JCastel358/Eltec406mca/hardware/single_detector_usb_master_r1/research/adc_seller_image_05.jpg

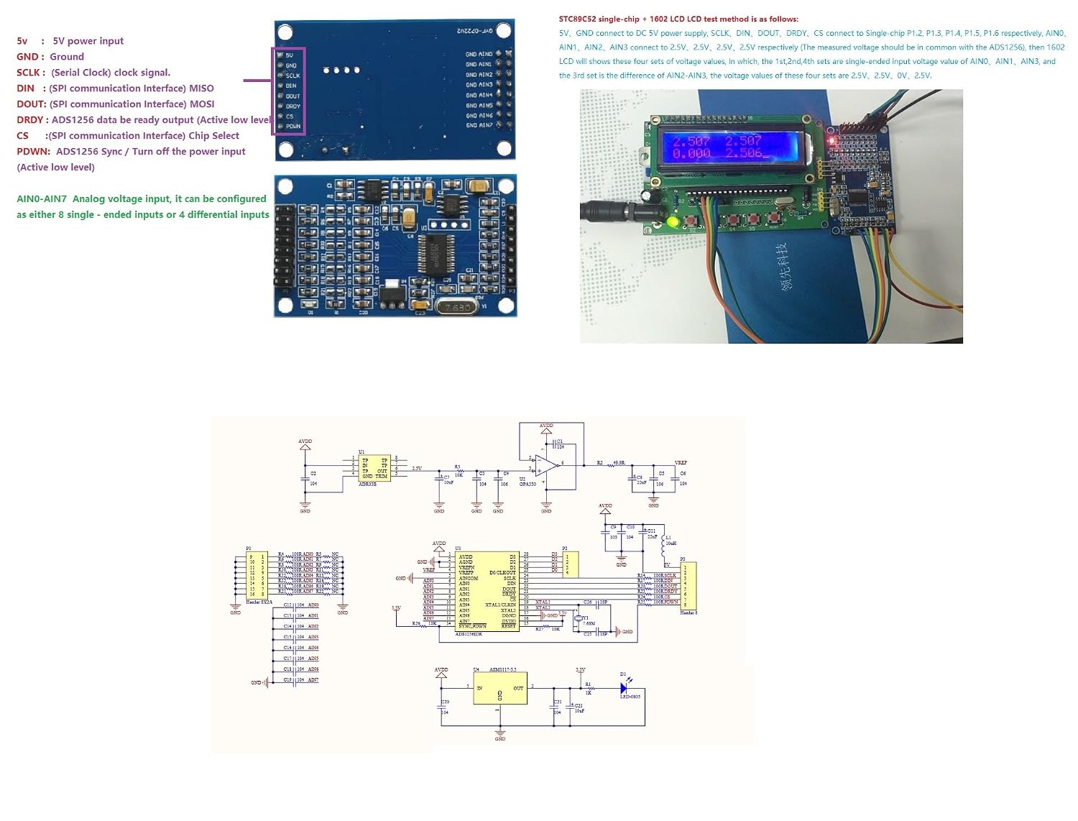
hardware/single_detector_usb_master_r1/research/adc_seller_image_05.jpg
