JCastel358/Eltec406mca/hardware/single_detector_usb_master_r1/reports/copper_review_complete/review.md

# Completed-board copper verification

**Final bounded verification is complete; no additional native repair is requested.** Audited main PCB SHA-256: `2ab4937f2ec558227736722549489c8d60b382db2a86436887f104acd336f4e2`. It matches `reports/final_ground_integration/integration.json`. The native integration report and its hash verify **0 DRC violations, 0 unconnected items and 0 schematic parity issues**. Protected-Kelvin verification passes independently on the audited snapshot.

The actual filled-reference audit was rerun into this new directory; all historical reports remain intact. The 562 selected SPI/control and analog tracks across 58 nets produce the same reference-coverage results as the preceding signal-route review: no sampled EM_GND crossing or antenna intrusion; 179 local reference-void runs, with a maximum individual span of 1.496 mm. The preceding detailed check identified their midpoints as through-pad/via clearance openings. The local clock/MOSI geometry and limits documented in `reports/copper_review_final/review.md` remain applicable because the final integration preserved every prior signal track and added only ground connections.

Actual nearest GND through-connection distances now confirm the intended improvement:

| Signal transition, mm | Before | Completed board | Actual GND stitch, mm |
| --- | --- | --- | --- |
| ADC_SCLK [55.8,91.25] | 7.994 mm | 1.005 mm | [55.9,92.25] |
| AMP_OUT5 [31.35,20.25] | 18.120 mm | 2.789 mm | [28.65,19.55] |
| AMP_OUT5 [32.5,22.5] | 18.863 mm | 2.003 mm | [32.6,24.5] |
| AMP_OUT5 [31.7,24.4] | 18.066 mm | 0.906 mm | [32.6,24.5] |

Each listed GND via connects the actual filled GND regions on both In1.Cu and In2.Cu. C11, C13, C39 and C36 retain their dedicated 1.2 mm local surface ground access. The separate C12/C16 ground improvements are present in the verified integration report. No CAD was modified by this audit, and the audit/helper tools are frozen after this evidence.

This confirms native geometry, sampled reference coverage and shorter physical inter-plane return access. It does not qualify RF performance, impedance, measured noise, mounted ESL, regulator stability or detector performance. Evidence is in `complete_validation.json`, `copper_review.json` and the hashed `source_snapshot.kicad_pcb`; the combined native DRC evidence remains under `reports/final_ground_integration`.
