JCastel358/Eltec406mca/hardware/single_detector_usb_master_r1/exports/board_review/final_candidate/visual_review.md

# Final board PDF visual review

The primary design agent viewed all seven individually rendered pages on
2026-09-09, after export from board SHA-256
`2ab4937f2ec558227736722549489c8d60b382db2a86436887f104acd336f4e2`.
The accompanying JSON binds this review to the exact PDFs and rendered pages.

| File / page | Inspected result |
|---|---|
| assembly_top.pdf / 1 | Outline, module envelopes, centered references, polarity/pin markers and CUSTOMER annotations visible. Antenna keepout text is inside its empty region. Drawing and right-side module labels clear the page frame and title block. |
| copper_top.pdf / 1 | Complete top copper and legend shown; C12 and C16 return stubs visible. Board drawing clears the title block. Dense copper/legend overlay is intentional; use assembly drawing for part identification. |
| copper_bottom.pdf / 1 | Complete bottom view, explicitly labeled mirrored. Outline and copper contained within margins; title clear. |
| copper_layers.pdf / 1 | Complete F.Cu drawing, viewed from top, with no legend overlay. |
| copper_layers.pdf / 2 | Complete In1.Cu fill; ground-domain separations and antenna void visible; outline and title clear. |
| copper_layers.pdf / 3 | Complete In2.Cu fill; ground-domain separations and antenna void visible; outline and title clear. |
| copper_layers.pdf / 4 | Complete B.Cu drawing viewed from top, consistent with the separately mirrored bottom review. |

No unresolved page clipping, title overlap, missing drawing region or misplaced
module label was found. The earlier automatic-fit copper drawings touched the
title block; these final exports use explicit 2:1 scaling on A3 portrait pages
and resolve that issue. Small pin/reference details require normal PDF zoom.

This review checks the appearance of the PDFs. Native DRC/connectivity, copper
reference analysis, fabrication coordinates and physical qualification are
separate evidence. DNP crosses on the two jacks are deliberate. Module envelopes
are placement references, not fabricated module bodies or confirmed fit.
