JCastel358/Eltec406mca/hardware/single_detector_usb_master_r1/exports/fabrication_draft/20260909T153915_341509Z_690d80156d71_DRAFT/evidence/native_drill_report_DRAFT.txt

Drill report for single_detector_usb_master.kicad_pcb
Created on 2026-09-09T11:39:25

Copper Layer Stackup:
    =============================================================
    L1 :  F.Cu                      front
    L2 :  In1.Cu                    in1
    L3 :  In2.Cu                    in2
    L4 :  B.Cu                      back

Drill file 'single_detector_usb_master-PTH.drl' contains
    plated through holes:
    =============================================================
    T1  0.300mm  0.0118"  (214 holes))
    T2  0.800mm  0.0315"  (3 holes))
    T3  1.000mm  0.0394"  (18 holes)  (with 6 slots)
    T4  1.020mm  0.0402"  (54 holes))
    T5  1.200mm  0.0472"  (6 holes))

    Total plated holes count 295

Drill file 'single_detector_usb_master-NPTH.drl' contains
    unplated through holes:
    =============================================================

    Total unplated holes count 0
