JCastel358/Eltec406mca/docs/DATA_MAP.md

# Data map — where results, captures and calibration files live

**Nothing the apps record is stored inside this repository.** Every batch CSV,
attempt log, waveform snapshot, raw noise capture and reference-calibration
file is written to a per-model folder under the signed-in user's `Documents`.
This file maps those folders, the naming conventions, the in-repo evidence
that backs the production constants, and the backup routine.

Reconciled with the Windows bench laptop on **2026-09-02**.

---

## 1. Results roots (one per sensor model)

| Model | Root (Windows `%USERPROFILE%\Documents\…`, Xubuntu `~/Documents/…`) | Set in |
| --- | --- | --- |
| 405 M22 | `Eltec_405M22_Test_Results\405m22_esp32\` | `sensor_versions.py` / `m405m22` tester |
| 406 MCA | `Eltec_406MCA_Test_Results\v6_1_esp32\` (the folder name is the historical v6.1 build id — it is the correct, live location) | `m406mca` tester |
| 449 M18 | `Eltec_449M18_Test_Results\449m18_esp32\` | `m449m18` tester |
| 40623 array (DAQ rig) | `Eltec_40623_Test_Results\40623_array_daq\` | `array_rig/m40623` tester (`ELTEC_ARRAY_RESULTS_ROOT` overrides it for engineering runs) |

The apps create these on first save. A batch started on Windows is readable on
Xubuntu and vice versa (same CSV format, same layout). Re-entering an existing
batch number resumes it at the next sensor.

On the single-detector rigs a sensor number is only spent by a **PASS**
(2026-09-02), so a batch CSV holds **one row per test**: `500-7` appears once
for each part tried under that number, the last of them the pass that earns
it. `number_attempt` says which of those a row is.

### Inside each root

```
<root>\
├── <prefix>_lot_<lot>.csv              one verdict row per TEST (the production record); a number
│                                       that has not been passed yet repeats until a part earns it
├── <prefix>_lot_<lot>_attempts.csv     one row per event: measured / measure_error / stopped /
│                                       saved / stream_retry / rig_note  (attempt history; since
│                                       2026-09-09 a reference-unit lockout is a measure_error row)
├── autosave\                           in-progress batch state (crash recovery)
├── waveform_snapshots\lot_<lot>\       PNG per "Capture waveform" (+ cycle CSV sidecars);
│                                       automatic for failing noise captures / unstable drives
├── noise_captures\lot_<lot>\           405 M22 only: <sensor>_noise_raw.csv + .npz — the RAW
│                                       1000 SPS emitter-off record (opt-in button, and automatic
│                                       whenever any window goes over the limit)
├── calibration\*_cycles.csv            stability_calibration.py evidence captures (engineering)
└── reference_sensor_calibration.json   AIN1 reference baseline (the gate is ON again on every
                                        model since 2026-09-09; files predating the isolated
                                        buffer board are refused on load and kept as evidence)
```

`<prefix>` is `405m22_esp32`, `406mca_esp32` or `449m18_esp32`. The 449 M18
snapshots carry `_5hz` / `_18hz` suffixes.

### Inside the array rig's root (one tray = up to fifty parts)

```
Eltec_40623_Test_Results\40623_array_daq\
├── 40623_array_lot_<lot>.csv               one row per loaded POSITION per noise attempt; automatically saved
│                                           after capture; every row is
│                                           stamped calibration_status / calibration_id / verdict_status
├── 40623_array_lot_<lot>_attempts.csv      one row per TRAY event: offset_measured / locked / vacuum_confirmed / stabilisation_shortened /
│                                           capture_started / capture_retry / capture_error / noise_settled / judged / saved / remeasure
├── noise_captures\lot_<lot>\tray_<n>_raw.npz   the RAW 1000 SPS capture of all 50 channels (float32 [50, N],
│                                           ~4 MB compressed per 60 s tray) + 310-sample edge contexts, channel/
│                                           position/sensor-number arrays and metadata — the evidence for the
│                                           pending noise-limit derivation; never delete
└── grid_snapshots\lot_<lot>\tray_<n>.png       the coloured 5x10 grid (the TP120 data sheet equivalent)
```

Columns: `array_rig/m40623/README.md`. Sensor numbers are assigned when
**Measure noise** freezes the accepted offset readings, row-major over the
loaded positions, continuing the batch's highest number. Offset screening
reserves no numbers: each `offset_measured` event retains JSON with all fifty
readings, occupancy and classifications, including failures before replacement.
Since 2026-09-08 this also keeps initial/recheck voltages, occupancy source,
the inferred-empty cutoff/policy, actual recheck delay, and each position's
classification **if loaded**, so zero-output readings excluded as likely empty
remain reviewable. `locked` records the accepted map and manual overrides;
`vacuum_confirmed` records the operator's map/count and gauge confirmation.
`stabilisation_shortened` explains the deliberate departure from TP120's
five-minute power-on delay (the app cannot measure time since power-on).
`noise_settled` retains the successful capture's settling trace, including
unsettled deadline starts. Each one-second window records loaded-channel
maxima/minima and their deltas. The raw NPZ duplicates that trace in
`quiet_diagnostics_json`; CSV and NPZ record `noise_timing_policy`, the
criterion/tolerance, minimum/maximum wait, actual wait and stop reason.
A noise retry keeps its numbers (`tray_attempt` increments). The legacy
engineering lock API still records high-offset failure rows at lock time.

Simulation uses a separate root: the system temp directory's
`eltec-array-simulation`, or `<ELTEC_ARRAY_RESULTS_ROOT>/simulation` when
overridden. Rows carry `simulated=YES` and demo noise-limit provenance.

CSV columns are documented in each model README
([405](../single_detector_rig/m405m22/README.md),
[406](../single_detector_rig/m406mca/README.md),
[449](../single_detector_rig/m449m18/README.md)). Older batch files keep their
original header when columns are added later — rows stay aligned, new columns
are simply absent. A `NOT MEASURED` row (rig fault, nothing recorded) has empty
measurement columns and `failure_mode_tag = NM`; it is excluded from yield.

### Provenance suffixes seen on the bench laptop

Files were occasionally renamed by hand to keep history:
`_superseded_<date>_<reason>`, `_backup_all50_<date>`, `_hold_…`,
`_new15_only_backup`, `…_crosstalk_contaminated_<date>.json.bak`. Treat any
such file as **frozen evidence** — never delete or "clean up" without checking
[`CALIBRATION_RECORD.md`](CALIBRATION_RECORD.md) for what it backs. Prefer this
convention for future manual archiving: `<original name>_<YYYYMMDD>_<reason>`.

---

## 2. What is on the bench laptop today (2026-08-28)

| Folder | Size | Contents that matter |
| --- | --- | --- |
| `Eltec_405M22_Test_Results\405m22_esp32\` | ~15 MB, 75 files | **lot 500** (`405m22_esp32_lot_500.csv` + `_backup_all50_20260818` + `_superseded_20260817_reference_crosstalk`), test lots (`lot_test`, `lot_test2`, `lot_test_2`), `noise_captures\` (39 files, 9.7 MB — the raw captures behind the 15 % rule, the 60 s soak and the FIR change), `waveform_snapshots\` (18 files), `noise_experiments\` (2026-08-13 bench A/B: `part_in`, `part_out`, `covered`, `fan_off` `.npz` + `noise_experiment.py`), copies of the lot-500 Excel pair data, `reference_sensor_calibration_crosstalk_contaminated_20260817.json.bak` |
| `Eltec_406MCA_Test_Results\v6_1_esp32\` | ~16 KB | `406mca_esp32_lot_test.csv` + attempts, `reference_sensor_calibration.json` (historical schema-v2 baseline; refused on load since the 2026-09-09 schema v3 bump — kept as evidence, recalibrate instead) |
| `Eltec_449M18_Test_Results\449m18_esp32\` | ~5 KB | one attempts log — no production batch yet (calibration pending) |

Related folders outside this repository:

- `Documents\Eltec_IR_Telescope\` — the two-detector IR telescope: its own git
  repository (firmware v2.2 with `STREAM,START,BOTH`, app, session data).
  Unrelated to the sensor rig except that the same ESP32 board is reflashed
  between the two.
- `Documents\406_mca_data\` and `Documents\rename_to_Eltec_TestRig.cmd` —
  LabJack-era loose data and a leftover rename script. Candidates for archiving
  or deletion; not referenced by anything in this repository.

---

## 3. Evidence kept inside the repository

| Path | What it is | Backs |
| --- | --- | --- |
| `analysis/405M22_Data/405M22_Data_old_fixture.xlsx`, `405M22_Data_new_fixture.csv.xlsx` | lot-500 paired measurements, legacy fixture vs this rig (2026-08-17) | sensitivity factor **4.30**, noise allowance **15 %** |
| `analysis/reports/405M22_Noise_Filtering_Explained.md` (+ `.docx`, two PNGs) | explainer for the noise pipeline passband and the anti-alias FIR (2026-08-20) | noise verdict band, FIR change |
| `analysis/reports/LabJack_T7_406MCA_Buffer.docx`, `406MCA_Original_Buffer_Issue_Explanation_Readable.docx` | LabJack-era buffer write-ups | historical background for the op-amp buffer stage |
| `analysis/reports/406MCA_SNR_Analysis_Report.docx`, `406MCA_SNR_Group_Summary.csv` | outputs of the retired v1 SNR sweep analysis | historical |

The raw captures themselves (`.npz`) are **not** in git (they are ignored by
`.gitignore`) — see §5.

---

## 4. Tools that read this data

| Tool | Reads | Purpose |
| --- | --- | --- |
| `engineer_tools/noise_band/replot_noise_capture.py` | `noise_captures/**/*_noise_raw.npz|.csv` | Replays a saved raw capture through the exact production pipeline and through alternative bands / boxcars; prints a verdict-comparison table and a PNG per capture. This is why raw captures must never be lost — any future limit or band change can be re-judged on real parts. `--boxcar 20` reproduces the pre-2026-08-20 pipeline. |
| `engineer_tools/noise_band/filter_response_analysis.py` | (synthetic + a measured capture spectrum) | Characterises the pipeline's passband and aliasing; tests legacy-amplifier passband hypotheses. |
| `single_detector_rig/<model>/stability_calibration.py` | live rig → `calibration/*_cycles.csv` | Collects known-good peak-delta evidence for the stability threshold (`capture`, `summarize`). Engineering only — never issues verdicts. |
| `array_rig/m40623/daq_bench_probe.py` | live DAQ → stdout, optional `.npz` (`--save`) | Bench checks of the array rig's acquisition path (identity, self-cal, config read-back, own-scale scan — the -HG question needs a known, metered voltage on an input — unsettled conversion slot, instrument floor, 60 s stream integrity, crosstalk). Engineering only. |
| `array_rig/m40623/daq_rig_readout.py` | live DAQ → stdout; CSV (`-o`) and `.npz` (`--npz`) only where told | The array rig's bench readout (offsets of any or all positions, captures, text-mode watch). Writes nothing unless given an output path — never under `Documents`. Its `.npz` uses the bench probe's key layout (+ `drop_first`) and replays in `replot_noise_capture.py` given the file path. Engineering only, no verdicts. |
| `array_rig/m40623/daq_live_waveform.py` | live DAQ → screen; `s` or `--save-on-exit` → `<save-dir>/daq_live_<YYYYmmdd_HHMMSS>.npz` | The array rig's live scope. `--save-dir` defaults to the current working directory (never `Documents`); a saved file holds the whole buffer of all channels (up to `--max-window`) in the readout's layout and replays in `replot_noise_capture.py` given the path. Engineering only, no verdicts. |
| `engineer_tools/array_parity/array_noise_parity.py` | `noise_captures/lot_<lot>/tray_*.npz` (or the lot CSV) + a typed legacy data sheet | Pairs legacy-fixture DMM readings with array captures by sensor id (or tray + position), fits the chain factor (median ratio and regression through origin, worst-window and median-window metrics), replays other bands, proposes the pin-level noise limits and writes `calibration/parity_<date>.csv|.png` (CALIBRATION_RECORD §4b.2). |
| `engineer_tools/reference_unit/reference_candidate_qualifier.py` | live rig → `~/Documents/Eltec_ReferenceCandidates/<label>/<label>_run<n>_<stamp>.json|.npz`, `comparison_<stamp>.csv|.png` | Reference-unit candidate selection: each run is the production 406 MCA path on one candidate (offset settle series, the adaptive 10 Hz capture, a drive hold, the post-emitter offset re-read) saved as JSON (numbers + series) and npz (raw waveforms, `waveform_v` + `sample_rate_hz` so the replot tool can read them); `compare` ranks the candidates. Its own folder, never an evidence folder (the tool refuses `Eltec_*_Test_Results`). Engineering only, no verdicts. |
| `engineer_tools/noise_band/replot_noise_capture.py --model 40623 [--position 2-4]` | `noise_captures/lot_<lot>/tray_*_raw.npz` | Replays one or every loaded position of an array tray capture through the production pipeline and alternative bands; "no limit" until the array limits exist. |

---

## 5. Backup — required, not optional

The ~15 MB of captures on the bench laptop is the **only copy** of the
evidence behind three production constants (the 4.30 factor, the 15 % noise
rule, the 60 s soak). The laptop is a single point of failure.

Routine (owner: the rig engineer):

1. **After every calibration lot and at least monthly**, zip the four roots:
   `Eltec_405M22_Test_Results`, `Eltec_406MCA_Test_Results`,
   `Eltec_449M18_Test_Results`, `Eltec_40623_Test_Results` →
   `Eltec_TestResults_backup_<YYYY-MM-DD>.zip` (the array root grows by a
   few MB per tray: every raw 50-channel capture is kept).
2. Copy the zip to the company share / cloud drive (not the same laptop).
3. Open the zip once and confirm `lot_500` CSVs and `noise_captures\lot_500\`
   are inside.
4. Note the backup date in [`CHANGELOG.md`](../CHANGELOG.md) when a
   calibration lot was added.

Keep the lot-500 files permanently. Test-lot files (`lot_test*`) can be pruned
once backed up, but the `noise_captures` under them are still useful for
replay work.

Also back up `analysis/405M22_Data/` implicitly — it is in git, so pushing to
the remote covers it.
