JCastel358/Eltec406mca/hardware/single_detector_usb_master_r1/research/source_mechanical_audit.md

# Source and mechanical evidence audit

Date: 2026-09-09. This is a read-only audit of the supplied original design and photographs; no original files were changed. Coordinates and dimensions below are confirmed in the supplied CAD, not physical measurements or approval of the replacement board.

## Source selection and provenance

- Original archive: `C:/Users/JoseCastelblanco/Downloads/ESP32_test_board.zip`, 111,006,702 bytes, SHA256 `2DADA1CE844D0854E8EF3A0DF1814969033200C3C066BBAC00AF3113214D43CF`.
- Current native members: `ESP32_test_board/ESP32_test_board.kicad_sch`, `.kicad_pcb`, and `.kicad_pro`. Selected current top-level files; excluded `.history` git internals and `_restore_backup_2026-07-27T09-18-41-617`.
- Extracted bytes are under `../source_reference/ESP32_test_board/`; all extraction targets were normalized and checked to stay within `source_reference`, individual entries were restricted to 5 MB, and original archive paths were retained.
- `../source_reference/source_provenance.json` records member names, lengths, and SHA256 hashes for every extracted file and copied photograph.
- Original native PCB SHA256: `9A4D2F2CABA80031463D3540B79024CE9E34D5625D32769739845703F8EAEA64`.
- Original native schematic SHA256: `8CF750AB7967E7993EF7BA2EA656DF6E8EEC73FAEB421930F8CC7B3901AD3F88`.
- Original archive project SHA256: `61F5AFC5841D5DF5EDEE4F90A96EB91648CF93F5C522C01B3AECA97D9C2D84B8`.
- `C:/Users/JoseCastelblanco/Documents/ESP32_test_board/ESP32_test_board.kicad_pcb` and `.kicad_sch` exactly match the extracted originals. The Documents `.kicad_pro` differs only by `pcbnew/last_paths/step` being an empty string rather than absent; this is export-path state, not different design geometry.
- Native schematic identifies itself as **ESP32 Modular Interface, rev B, 8-4-2026**, generated by KiCad 10.0. Board format is `20260206`; schematic format is `20260306`. Installed KiCad 10.0.6 Python/pcbnew reopened the supplied PCB successfully for this inspection.

## Supplied files that are photographs, not mechanical CAD

- `SingleDetectorCase` has JPEG/JFIF/Exif file contents. Preserved byte-for-byte as `../source_reference/SingleDetectorCase.jpg` for display. The photo shows a hinged printed optical enclosure, a detector at the lower end, and external cable routing. It contains no scale or dimension annotations.
- `SingleDetectorPCB` also has JPEG/JFIF/Exif contents. Preserved byte-for-byte as `../source_reference/SingleDetectorPCB.jpg`. It shows the populated blue carrier board, socketed USB-C ESP32, an ADS1256 module, two right-angle barrel jacks, and soldered emitter/detector wires.
- `SingleDetectorPCBschematic.png` is a schematic raster. The native schematic is more authoritative for connectivity and coordinates.
- A bounded search of Downloads and the unpacked original project found no related STEP/STP, STL, DXF, Fusion, SolidWorks, FreeCAD, or IGES enclosure/block drawing. Unrelated 50SensorBreakoutBoard STEP files were not treated as evidence for this fixture.
- Do not infer detector optical-axis locations, enclosure clearances, mounting-hole centers, connector manufacturer, or dimensions by scaling these photos.

## Confirmed original board geometry

| Item | Native CAD evidence | Confidence/limitation |
|---|---|---|
| Outline | One Edge.Cuts rectangle from (12, 12) to (98, 115) mm; 86 x 103 mm | Confirmed original CAD outline; physical dimensions unmeasured |
| Copper stack | 2 copper layers; board thickness 1.6 mm | Native design setting |
| Carrier mounting holes | No NPTH pads and no mounting-hole footprints; original NPTH drill file is empty | Original carrier has no designed mounting holes; module holes visible in photograph belong to modules |
| Original layout inventory | 55 footprints, 401 track/via objects, 1 copper zone | Does not establish electrical correctness |
| Barrel-jack separation | J1 and J2 pad-1 origins separated by 48 mm | Original CAD; preserve if reusing enclosure interface |
| USB interface | USB-C receptacle belongs to plug-in ESP32 board; no independent carrier USB connector | Photo and native schematic agree |

All coordinates below are in the original KiCad global coordinate system (mm). Subtract (12,12) for offsets from the original outline minimum corner.

## Original externally constrained component locations

| Reference | Footprint | Anchor X,Y mm | Rotation deg |
|---|---|---|---|
| J1 | `Connector_BarrelJack:BarrelJack_GCT_DCJ200-10-A_Horizontal` | 82.2, 26.5 | 90 |
| J2 | `Connector_BarrelJack:BarrelJack_GCT_DCJ200-10-A_Horizontal` | 82.2, 74.5 | 90 |
| U1 | `Eltec Footprints:ESP32_DEVKITV1` | 44.17, 113.67 | 90 |
| U2 | `Eltec Footprints:ADS1256_BOARD` | 44.32, 83.515 | 90 |
| Test1 | `Eltec Footprints:Sensor` | 23.62, 83.4075 | 180 |
| Ref1 | `Eltec Footprints:Sensor` | 23.62, 70.985 | 180 |
| Test2 | `Eltec Footprints:Sensor` | 23.62, 58.5825 | 180 |
| Ref2 | `Eltec Footprints:Sensor` | 23.62, 46.1625 | 180 |
| Test3 | `Eltec Footprints:Sensor` | 23.74, 34.3625 | 180 |
| Ref3 | `Eltec Footprints:Sensor` | 23.6541, 21.985 | 180 |
| E1 | `Eltec Footprints:Emitter` | 32.235, 111.17 | 90 |
| E2 | `Eltec Footprints:Emitter` | 23.735, 111.17 | 90 |
| E3 | `Eltec Footprints:Emitter` | 15.235, 111.17 | 90 |

### Barrel jacks

- Assigned footprint: `Connector_BarrelJack:BarrelJack_GCT_DCJ200-10-A_Horizontal`; footprint description cites GCT drawing `https://gct.co/files/drawings/dcj200-10.pdf` and 5.5 mm outer / 2.05 mm inner mating diameter. This identifies the design footprint, **not the manufacturer of the physically installed jack**, which is not recoverable from the photo.
- J1 is the detector/reference/buffer battery input; J2 is the emitter battery input. Pad 1 is positive, pad 2 is battery return; pad 3 has no electrical net in the original design. Do not connect its mounting/support tab to ground unless the chosen part confirms that use.
- Slot geometry is directly recoverable. These drill dimensions are the unrotated pad-local dimensions; the footprints are rotated 90 degrees in the board.

| Ref.pad | Center X,Y mm | Pad-local size mm | Pad-local drill mm |
|---|---|---|---|
| J1.1 | 82.2, 26.5 | 4.6, 2 | 3.6, 1 |
| J1.2 | 88.5, 26.5 | 4.2, 2 | 3.2, 1 |
| J1.3 | 85.1, 21.7 | 2, 4.2 | 1, 3.2 |
| J2.1 | 82.2, 74.5 | 4.6, 2 | 3.6, 1 |
| J2.2 | 88.5, 74.5 | 4.2, 2 | 3.2, 1 |
| J2.3 | 85.1, 69.7 | 2, 4.2 | 1, 3.2 |

### ESP32 module/header

- U1 is a 30-position ESP32 DEVKIT V1 pattern: two 1x15 rows, 2.54 mm pitch, 25.4 mm row separation. Pads are 2 mm circles with 1 mm drills in the source. The existing photograph supports a 30-pin USB-C module, but exact ESP32 module vendor, underside height, and USB plug keepout remain unverified.
- Row A: pad 1 (3V3) at (86.08,87); pad 15 (D23) at (50.52,87). Row B: pad 16 (VIN) at (86.08,112.4); pad 30 (EN) at (50.52,112.4). Each row runs toward decreasing X.
- **Source defect:** there are actually 31 pads because pad 28 occurs twice. One duplicate pad 28 is coincident with pad 27 at (58.14,112.4), while the intended pad 28 is (55.6,112.4). The duplicate is present both in the board and original library. Preserve the proper 30 pin locations, remove the coincident erroneous duplicate in the new design, and verify symbol-to-footprint parity.
- Original module footprint is marked `smd` despite through-hole pads and has no courtyard. Recreate as an appropriate socket/module assembly representation and include physical keepouts. Do not use the source metadata unchanged to generate placement data.
- Module ground pins 2 and 17 have differently named nets in the source; do not infer intentional isolation merely from these names because the plug-in module may connect them internally. Likewise the ADC module ground headers need explicit continuity reasoning.

### ADS1256 module/header

- U2 has 24 unique positions: one digital/power 1x8 header and an analog 2x8 header; all pitch is 2.54 mm. Pads are 2 mm circles with 1 mm drills.
- Digital/power row: pads 1 through 8 have centers X = 53.21 + 2.54*(pad-1), Y = 80.975 mm.
- Analog input row: pads 9 through 16 have centers X = 53.21 + 2.54*(pad-9), Y = 23.825 mm.
- Analog ground row: pads 17 through 24 have centers X = 53.21 + 2.54*(pad-17), Y = 26.365 mm.
- Separation of the digital row and analog input row is 57.15 mm; digital to analog ground row is 54.61 mm.
- The standalone library silk body rectangle is 62.23 x 35.56 mm. It is a draft graphic, not a manufacturer body drawing; pin coordinates are stronger evidence than that body rectangle. No module mounting holes are implemented in the carrier footprint.
- Original module footprint is marked `smd` despite through-hole pads; no proper courtyard is defined. Socket height and clearance under the module require actual header choice and module underside measurements.

| U2 pad | Native symbol/function | Original net |
|---|---|---|
| 1 | 5V | `Net-(U1-VIN)` |
| 2 | GND | `Net-(U2-GND)` |
| 3 | SCLK | `Net-(U1-D18)` |
| 4 | DIN | `Net-(U1-D23)` |
| 5 | DOUT | `Net-(U1-D19)` |
| 6 | DRDY | `Net-(U1-D4)` |
| 7 | CS | `Net-(U1-D5)` |
| 8 | PDWN | `Net-(U1-3V3)` |
| 9 | AIN0 | `Net-(U2-AIN0)` |
| 10 | AIN1 | `Net-(U2-AIN1)` |
| 11 | AIN2 | `Net-(U2-AIN2)` |
| 12 | AIN3 | `Net-(U2-AIN3)` |
| 13 | AIN4 | `Net-(U2-AIN4)` |
| 14 | AIN5 | `Net-(U2-AIN5)` |
| 15 | AIN6 | `unconnected-(U2-AIN6-Pad15)` |
| 16 | AIN7 | `Net-(U2-AIN7)` |
| 17 | GND0 | `Net-(O1-V-)` |
| 18 | GND1 | `Net-(O1-V-)` |
| 19 | GND2 | `Net-(O1-V-)` |
| 20 | GND3 | `Net-(O1-V-)` |
| 21 | GND4 | `Net-(O1-V-)` |
| 22 | GND5 | `Net-(O1-V-)` |
| 23 | GND6 | `unconnected-(U2-GND6-Pad23)` |
| 24 | GND7 | `Net-(O1-V-)` |

### Detector/reference and emitter wire connections

- E1/E2/E3 are **wire solder-pad patterns**, not emitter body footprints: 2 pads on 2.54 mm pitch, 2 mm pads with 1.2 mm drills. The source symbol value is IR-56. No emitter optical or body geometry can be recovered from these pads.
- Test1/Ref1 through Test3/Ref3 are **wire solder-pad patterns**, not directly mounted sensor bodies. Pads 1 and 2 are 5.08 mm apart, diameter 2.54 mm, drill 1 mm; pad 3 is a 2.54 x 7 mm rectangular surface pad for return/shield soldering.
- Pad 1 is detector V+, pad 2 is signal, pad 3 is GND/case. The photo shows wires and shield/braid soldered to the first test/reference pair. Nothing in the source establishes optical detector lead orientation or optical-axis spacing.
- The original generic footprint metadata uses `smd` and DNP/assembly attributes for these solder pads; solder land groups should not become fictitious physical components in a new populated-board BOM.

| Ref | V+ pad center mm | Signal/return pad center mm | GND/case surface pad center mm |
|---|---|---|---|
| Test1 | 16, 81.5025 | 16, 76.4225 | 21.842, 78.5815 |
| Ref1 | 16, 69.08 | 16, 64 | 21.842, 66.159 |
| Test2 | 16, 56.6775 | 16, 51.5975 | 21.842, 53.7565 |
| Ref2 | 16, 44.2575 | 16, 39.1775 | 21.842, 41.3365 |
| Test3 | 16.12, 32.4575 | 16.12, 27.3775 | 21.962, 29.5365 |
| Ref3 | 16.0341, 20.08 | 16.0341, 15 | 21.8761, 17.159 |
| E1 | 36.045, 109.9 | 33.505, 109.9 | n/a |
| E2 | 27.545, 109.9 | 25.005, 109.9 | n/a |
| E3 | 19.045, 109.9 | 16.505, 109.9 | n/a |

## Library and assembly completeness of the original

- `Eltec Footprints.pretty` contains 9 supplied `.kicad_mod` files: ADS1256_BOARD, AMS1117, Battery, Emitter, ESP32_DEVKITV1, IRLB8748, LMC6062, Sensor, and Untitled.
- No standalone current `.kicad_sym` library or `sym-lib-table` is included. Custom symbols are embedded inside the schematic under `lib_symbols` (`Eltec Part:*`); these can be extracted into the new project-owned symbol library.
- `fp-lib-table` also names `${KIPRJMOD}/eltect footprintw.pretty`, but that directory is not present in the current project (only in an excluded older backup). New project libraries must not retain this stale dependency.
- Original `production/bom.csv` lists electronic SMD parts, but omits RV1, the headers/modules, jacks, wire pads, and logo. It is historical evidence, not a complete purchasing/assembly BOM for the new project.
- Original RV1 uses `Potentiometer_THT:Potentiometer_Bourns_3296W_Vertical`, 1 kOhm, 2.54 mm pin pitch. User requests only the ESP32, ADS1256 and jacks be unpopulated, so any retained trimmer and sockets need explicit assembly purchasing support rather than inheriting the old BOM omission.
- Original production exports identify KiCad 10.0.3 and a 2026-08-04 timestamp. They are stored for comparison only; never submit these as outputs for the replacement design.

## Decisions recoverable without asking the user

- Preserve the original 86 x 103 mm outline and jack/header locations as the first trial geometry; label the revised placement preliminary until actual module clearances and enclosure fit are checked.
- Preserve the original wire-pad polarity and avoid pretending the emitter and detector bodies are on the PCB.
- Rebuild the malformed module footprint metadata and ESP32 duplicate pad in new project libraries.
- Retain independent emitter and detector supply returns where the schematic genuinely isolates them; do not short returns solely to simplify routing.

## Evidence still needed before mechanical/fabrication release

1. Confirmation that the replacement must fit the photographed enclosure with exactly the original carrier outline and jack/USB locations; no dimensioned enclosure/block drawing was supplied. Existing native carrier geometry can be used for trial layout without claiming fit approval.
2. Actual socket part numbers or allowed substitution, installed header height, underside component protrusion, and USB connector/cable clearance. Original pin-center geometry is known; vertical clearances are not.
3. Actual replacement barrel-jack part or confirmation that the existing two jacks will be transferred and fit the original slot pattern. Assigned footprint identity alone is not actual part authentication.
4. If moving from soldered wires to populated detachable connectors, connector selection and any enclosure clearance constraint must be resolved; original source does not select such connectors.
5. Actual optical-block CAD/lead drawings if the design scope expands to mounting detector/emitter bodies directly. The current supplied design only carries wire attachment points.

## Verification performed in this audit

- Checked JPEG magic and visually inspected both photographs.
- Compared SHA256 of top-level native original files against the separately unpacked project.
- Reopened the original PCB using installed KiCad 10.0.6 `pcbnew.LoadBoard`, read board outline, layer count, thickness, footprint locations, pads, drills, and net names; did not save or mutate it.
- Cross-checked absence of NPTH with original drill export; examined library entries and duplicate pad numbers.
- This audit did **not** run ERC/DRC or certify original board correctness, new layout correctness, module internals, enclosure fit, battery ratings, or power sequencing. Those checks belong to the new project validation work.
