JCastel358/Eltec406mca/analysis/reports/406MCA_SNR_Analysis_Report.docx

406MCA SNR Sweep Analysis

CSV analyzed: C:\Users\vma\Documents\Eltec_406MCA_Test_Results\406mca_results.csv

Report generated: 2026-06-02T11:17:30

Main Result

Strict highest-SNR candidate: 5.6 cm at 5.5 V with mean SNR 16.63 dB, mean sensitivity 16.50 mV, and mean noise 0.736 mV.

Practical lower-voltage candidate within 1 dB of strict best: 5.6 cm at 5.2 V with mean SNR 16.15 dB, mean sensitivity 12.37 mV, and mean noise 0.598 mV.

Top Candidates

Distance cm | Voltage V | Runs | Mean SNR dB | Sensitivity mV | Noise RMS mV | Pass rate
5.6 | 5.5 | 1 | 16.63 | 16.50 | 0.736 | 100%
5.6 | 5.4 | 1 | 16.61 | 15.49 | 0.692 | 100%
5.6 | 5.3 | 1 | 16.26 | 13.93 | 0.676 | 100%
5.6 | 5.2 | 1 | 16.15 | 12.37 | 0.598 | 100%
4.5 | 5.5 | 1 | 15.96 | 24.03 | 1.284 | 100%
6.5 | 5.5 | 1 | 15.94 | 15.51 | 0.757 | 100%
4.5 | 5.4 | 1 | 15.74 | 22.20 | 1.230 | 100%
5.6 | 5.1 | 1 | 15.60 | 10.93 | 0.575 | 100%
6.5 | 5.4 | 1 | 15.58 | 14.61 | 0.712 | 100%
5.6 | 5 | 1 | 15.29 | 10.73 | 0.543 | 100%

Best Setting By Distance

Distance cm | Best voltage V | Best SNR dB | Sensitivity mV | Noise RMS mV
4.5 | 5.5 | 15.96 | 24.03 | 1.284
5.6 | 5.5 | 16.63 | 16.50 | 0.736
6.5 | 5.5 | 15.94 | 15.51 | 0.757

Warnings And Follow-Up

- 39 of 39 distance/voltage groups have fewer than 3 runs. Repeat the leading candidates before making a final setting.

- All logged distances are under 10 cm. If these were intended to be 45, 56, or 65 cm, enter the full centimeter value in the tester.

- At 4.5 cm, the best SNR was at the highest tested voltage (5.5 V). If safe, test slightly above this voltage or repeat the top range.

- At 5.6 cm, the best SNR was at the highest tested voltage (5.5 V). If safe, test slightly above this voltage or repeat the top range.

- At 6.5 cm, the best SNR was at the highest tested voltage (5.5 V). If safe, test slightly above this voltage or repeat the top range.

- The strict best candidate is based on too few repeats for a production decision.

What Signal-To-Noise Ratio Means

SNR compares the useful waveform signal to the random or repeatability noise. Here it is calculated as signal RMS divided by noise RMS, then converted to dB with 20 * log10(signal RMS / noise RMS). Higher dB is better.

A 3 dB improvement is about 1.41x more signal-to-noise ratio. A 6 dB improvement is about 2x. A 10 dB improvement is about 3.16x.

What Was Done In This Tester

- The tester records AIN0 waveform samples and AIN2 blade sync samples.

- The waveform is split into complete blade-sync cycles after the initial settling cycles are ignored.

- Stable cycles are selected using the existing stability check.

- Sensitivity is measured as the median peak-to-peak signal from the stable cycles, corrected for external gain.

- Noise is measured by aligning stable cycles by phase, subtracting the average cycle shape, and calculating the residual RMS.

- SNR uses the RMS of the average cycle shape as signal RMS and the residual RMS as noise RMS.

- Distance and input voltage are logged with every run so settings can be grouped and compared.

Other Useful Ways To Choose Distance And Voltage

- Repeat the best candidates 3 to 5 times each and compare means plus variation, not just single runs.

- Randomize or reverse the run order to catch drift from warm-up, sensor heating, or alignment changes.

- Use a response-surface sweep: coarse voltage/distance grid first, then smaller steps near the best region.

- Use a practical tie rule: if settings are within 1 to 2 dB, prefer lower voltage, lower current, lower heat, and easier fixture distance.

- Track current, emitter temperature, and any clipping warnings so the best SNR setting is also safe and stable.

- Run a dark/no-emitter or blocked-path noise capture to separate electronics noise from optical/signal noise.

- Validate the chosen setting on multiple sensors, not only one sensor, before using it as a production setting.

- If production tolerance matters, use confidence intervals or an ANOVA-style comparison to decide whether differences are real.
