JCastel358/Eltec406mca/docs/daq_usb_aio16_64ma/DPK-AIO16-64MA_Useful_Links.docx

# DPK-AIO16-64MA DAQ Useful Links

Install the 64MA Windows driver/software package before using the DAQ. The LabVIEW VIs are optional and are not a substitute for the driver.

DPK-AIO16-64MA Product Page (https://accesio.com/product/dpk-aio16-64ma/)

USB-AIO16-64MA Windows Driver and Software Package (https://accesio.com/files/packages/USB-AIO16-64MA%20Install.exe)

USB-AIO16-64MA Datasheet (https://accesio.com/DS/USB-AIO16-64MA%20Datasheet.pdf)

DAQ-PACK M Series User Guide (https://accesio.com/MANUALS/DAQ-PACK%20M%20Series%20Guide.pdf)

USB Software Reference Manual (https://accesio.com/MANUALS/USB%20Software%20Reference%20Manual.html)

LabVIEW Software Packages (Optional) (https://accesio.com/files/VIs)
