JCastel358/Eltec406mca/output/pdf/Eltec_USB_Master_Power_Rev_A.pdf

# One USB switch; two battery supplies

Complete retrofit = battery switch board + protected ADC socket adapter. No firmware change is required.

ELTEC | USB master power | Rev A | 2026-09-08 | Prototype: bench qualification required | 1 / 6

### Laptop / PC

Original USB data connection

### RIITOP switched extension

Use its device-side switched power

### ESP32 + ADS1256

USB still powers the existing digital circuitry

### Battery 1: 6.5 V

Emitter: maximum 200 mA stated by user

### Q1 battery switch

Positive lead only; schematic on sheet 2

### Existing emitter barrel jack

Keep the regulator and emitter PWM circuit

### Battery 2: 6.5 V

Detector + reference + buffer supply

### Q2 battery switch

Positive lead only; schematic on sheet 2

### Existing detector barrel jack

All detector-side loads remain behind Q2

SOCKET ADAPTER: unplug the ADS1256 module and insert the adapter beneath it.

Intercept every AIN0-AIN7 contact. Keep the two sides of each analog contact separate and connect them through sheet 4. Pass the other header contacts straight through by verified function. AINCOM may pass through only if it is grounded; otherwise it needs its own protected channel.

Take V5 and GND for this circuit from the USB-powered ADC supply. V5 must be the actual ADC AVDD rail: use the module 5V header only after confirming they are the same net. Preserve the original USB cable, USB-C configuration wiring, and signal-ground connections.

Build limits: 5.5-7.5 V battery range; 5 V USB only; analog signals 0-4.0 V while measuring. Confirm detector current and jack polarity. This is a prototype design, not a bench-tested retrofit.

# Battery switches - use both IRLB8748s

## CHANNEL 1 / EMITTER (original jack J2)

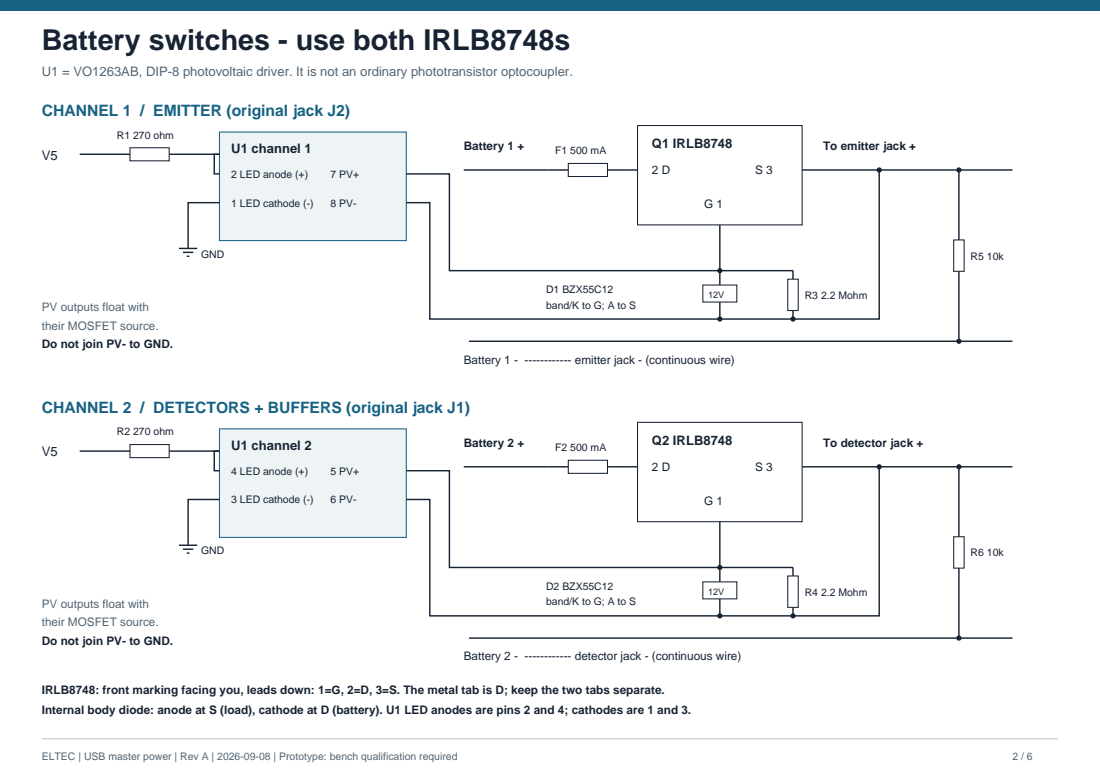
[picture p8: page 2]

U1 = VO1263AB, DIP-8 photovoltaic driver. It is not an ordinary phototransistor optocoupler.

PV outputs float with
their MOSFET source.
Do not join PV- to GND.

Battery 1 - ------------ emitter jack - (continuous wire)

CHANNEL 2 / DETECTORS + BUFFERS (original jack J1)

Battery 2 - ------------ detector jack - (continuous wire)

IRLB8748: front marking facing you, leads down: 1=G, 2=D, 3=S. The metal tab is D; keep the two tabs separate.
Internal body diode: anode at S (load), cathode at D (battery). U1 LED anodes are pins 2 and 4; cathodes are 1 and 3.

# ADC supply supervisor and isolation control

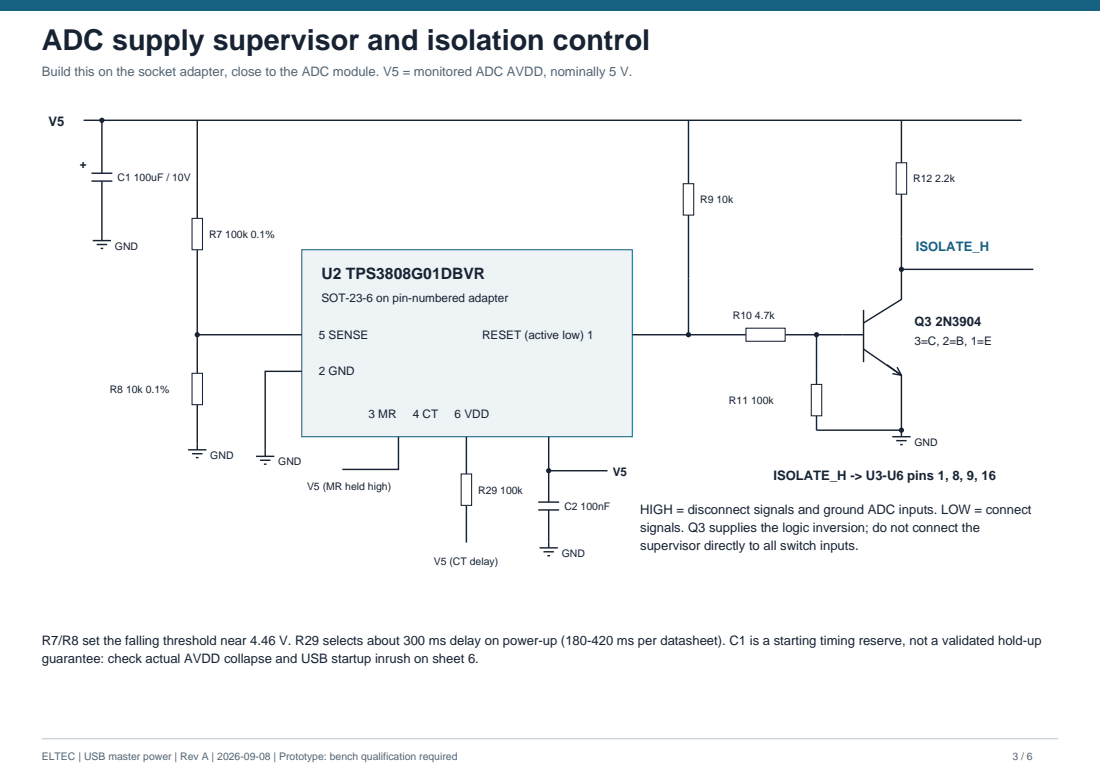
[picture p9: page 3]

Build this on the socket adapter, close to the ADC module. V5 = monitored ADC AVDD, nominally 5 V.

SOT-23-6 on pin-numbered adapter

HIGH = disconnect signals and ground ADC inputs. LOW = connect
signals. Q3 supplies the logic inversion; do not connect the
supervisor directly to all switch inputs.

R7/R8 set the falling threshold near 4.46 V. R29 selects about 300 ms delay on power-up (180-420 ms per datasheet). C1 is a starting timing reserve, not a validated hold-up
guarantee: check actual AVDD collapse and USB startup inrush on sheet 6.

# ADC socket adapter - two inputs per ADG4613

Build this circuit FOUR times: U3 (AIN0/1), U4 (AIN2/3), U5 (AIN4/5), U6 (AIN6/7).

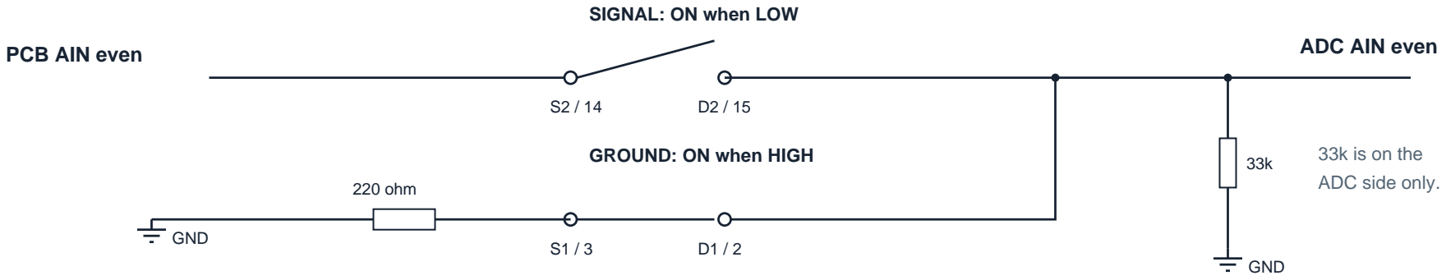
[picture p10: figure]
PCB AIN even; SIGNAL: ON when LOW; ADC AIN even; GROUND: ON when HIGH; 220 ohm; GND; 33k is on the ADC side only.
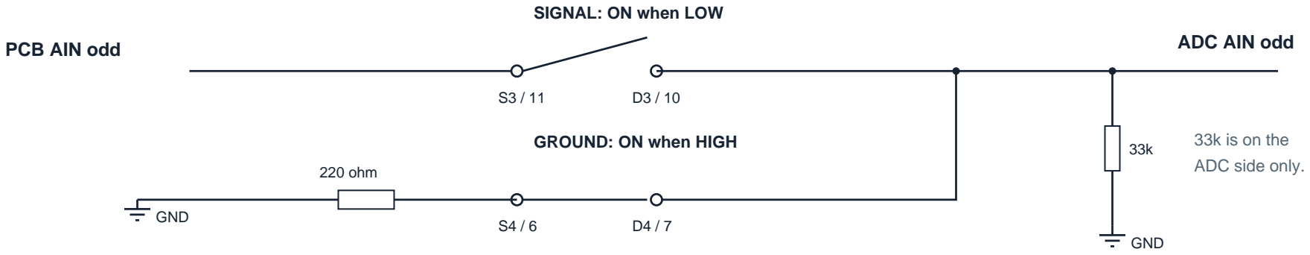
[picture p11: figure]
PCB AIN odd; SIGNAL: ON when LOW; ADC AIN odd; GROUND: ON when HIGH; 220 ohm; GND; 33k is on the ADC side only.

ELTEC | USB master power | Rev A | 2026-09-08 | Prototype: bench qualification required | 4 / 6

Each IC: pin 13 = V5; pins 4 and 5 = GND; pin 12 = no connection.
Pins 1, 8, 9 and 16 = ISOLATE_H. Fit one 100 nF capacitor C3-C6 from pin 13 to pin 5.

Do not leave a straight-through header pin or wire bypassing either signal switch.

The drawing shows ISOLATE_H = HIGH. At shutdown the 220-ohm ground paths discharge ADC-side capacitors. When power reaches zero, all ADG4613 switches open; the 33k resistors hold the ADC inputs near ground against leakage.

Use ADG4613BRUZ on TSSOP-16-to-DIP adapters, not ADG4612. Keep analog wiring short and away from emitter power leads. No added capacitors on analog inputs; verify existing module input capacitance is at most 1 uF per input.

# Parts and pin-to-pin wiring

Resistors: 1/4 W, 1% unless stated otherwise. Q1/Q2 IRLB8748 and perfboard are already available.

ELTEC | USB master power | Rev A | 2026-09-08 | Prototype: bench qualification required | 5 / 6
References | Qty | Value / part | Build note
U1 | 1 | VO1263AB, DIP-8 | Dual photovoltaic driver; DIP socket recommended
U2 | 1 | TPS3808G01DBVR | Adjustable supervisor + SOT-23-6 breakout
U3-U6 | 4 | ADG4613BRUZ | Four TSSOP-16 chips + four numbered DIP adapters
Q1,Q2 / Q3 | 2 / 1 | IRLB8748 / onsemi 2N3904 | Existing power MOSFETs / add one TO-92 NPN
D1,D2 | 2 | BZX55C12, 12 V zener | Cathode stripe to G; anode to S
R1,R2 / R3,R4 | 2 / 2 | 270 ohm 1% / 2.2 Mohm | LED current / gate discharge
R5,R6,R9 / R10 | 3 / 1 | 10k / 4.7k | Output bleeders + reset pull-up / Q3 base
R7 / R8 | 1 / 1 | 100k 0.1% / 10k 0.1% | Voltage-sense divider
R11,R29 / R12 | 2 / 1 | 100k / 2.2k | Base pull-down + CT timing / ISOLATE_H pull-up
R13-R20 / R21-R28 | 8 / 8 | 220 ohm / 33k | Ground discharge paths / ADC input pull-downs
C1 / C2-C6 | 1 / 5 | 100 uF 10 V / 100 nF 16 V | C1 electrolytic, - to GND; ceramic decouplers
F1,F2 | 2 | 500 mA DC fuses + holders | Initial choice; confirm both branch currents/inrush
Connections | set | Male/female headers; 22-24 AWG | Match actual ADC footprint and barrel dimensions

### Exact ADC routing (repeat the sheet 4 circuit for each row):

IC | PCB-side signals | ADC-side signal + grounding junctions | Ground resistor / pull-down
U3 | AIN0 -> 14; AIN1 -> 11 | AIN0 -> 15+2; AIN1 -> 10+7 | R13/R21 for AIN0; R14/R22 for AIN1
U4 | AIN2 -> 14; AIN3 -> 11 | AIN2 -> 15+2; AIN3 -> 10+7 | R15/R23 for AIN2; R16/R24 for AIN3
U5 | AIN4 -> 14; AIN5 -> 11 | AIN4 -> 15+2; AIN5 -> 10+7 | R17/R25 for AIN4; R18/R26 for AIN5
U6 | AIN6 -> 14; AIN7 -> 11 | AIN6 -> 15+2; AIN7 -> 10+7 | R19/R27 for AIN6; R20/R28 for AIN7

# Assembly checks and first power-up

Verify with current-limited supplies first; qualify the assembled board before technicians use it.

ELTEC | USB master power | Rev A | 2026-09-08 | Prototype: bench qualification required | 6 / 6
1. Map the module before soldering.
With all sources disconnected, confirm jack polarity and every header contact. V5 must follow the actual ADC AVDD; if the module has a regulator/filter between header 5V and AVDD, do not treat them as interchangeable. Confirm AINCOM is grounded and input capacitance is at most 1 uF per channel. Keep battery returns as originally wired; do not add a new ground tie across emitter isolation.
2. Test the battery board with dummy loads.
Use one 6.5 V current-limited source and a 33-ohm, 5 W resistor per branch (about 197 mA). Apply 5 V to V5/GND. Check each gate relative to its own SOURCE: at least 4.5 V ON, less than 0.5 V after OFF settles. Confirm switched outputs rise to the battery voltage and decay near zero after OFF. D and S must not be reversed. Keep the MOSFET drain tabs separate.
3. Test the socket adapter without the ADC.
Apply 5 V at V5; after the delay, ISOLATE_H should be below 0.4 V and each signal path should conduct. Below approximately 4.46 V it should go HIGH and each output should connect to ground through its 220-ohm path. With V5 absent and 4.0 V applied to each PCB-side input, each ADC-side input should remain below 0.2 V.
4. Check shutdown with an oscilloscope.
With the actual module and PC, capture AVDD, ISOLATE_H and each ADC input for USB OFF, unplugging, rapid toggles and brownouts. Require -0.3 V < AIN < AVDD + 0.3 V throughout; use a 0.2 V upper-margin target. Inputs must discharge before AVDD reaches zero. C1 sizing assumes no more than 500 mA discharges V5 and no more than 1 uF at each ADC input; verify both. Supervisor assertion time is typical, not a guaranteed system timing bound.
5. Recheck startup and measurement quality.
Confirm stable AVDD of 4.75-5.25 V and successful USB enumeration with the added 100 uF; check startup inrush and repeated starts on the actual PC. Verify every normal signal stays within 0-4.0 V. The switches and 33k loads change the analog path: compare offset, sensitivity, reference response and noise against the original setup, then recalibrate before production. Wait for the usual detector settling before testing.

Design basis and limits

Both batteries = 6.5 V and emitter maximum = 200 mA (user). Detector current, actual module circuitry and power waveforms remain unmeasured. The single-MOSFET battery paths do not block reverse current from an independently powered load and provide no reverse-battery protection. The adapter does not clamp an excessive detector voltage during normal ON operation.

IRLB8748 (https://www.infineon.com/part/IRLB8748) | VO1263 (https://www.vishay.com/doc/?84639) | TPS3808 (https://www.ti.com/lit/ds/symlink/tps3808.pdf) | ADG4613 (https://www.analog.com/media/en/technical-documentation/data-sheets/adg4612_4613.pdf) | 2N3904 (https://www.onsemi.com/download/data-sheet/pdf/2n3903-d.pdf) | BZX55 (https://www.vishay.com/docs/85604/bzx55.pdf)
