JCastel358/Eltec406mca/analysis/reports/406MCA_SNR_Group_Summary.csv

distance_cm | input_voltage_v | runs | pass_runs | fail_runs | pass_rate | mean_snr_db | std_snr_db | ci95_snr_half_width | min_snr_db | max_snr_db | mean_sensitivity_mv | std_sensitivity_mv | mean_noise_rms_mv | std_noise_rms_mv | mean_offset_v | fail_reasons
4.500000 | 4.300000 | 1 | 1 | 0 | 1.000000 | 12.105173 |  |  | 12.105173 | 12.105173 | 7.652134 |  | 0.542644 |  | 0.752494
4.500000 | 4.400000 | 1 | 1 | 0 | 1.000000 | 11.490319 |  |  | 11.490319 | 11.490319 | 8.093894 |  | 0.629949 |  | 0.750005
4.500000 | 4.500000 | 1 | 1 | 0 | 1.000000 | 11.628043 |  |  | 11.628043 | 11.628043 | 9.182543 |  | 0.691939 |  | 0.747228
4.500000 | 4.600000 | 1 | 1 | 0 | 1.000000 | 12.083600 |  |  | 12.083600 | 12.083600 | 11.202067 |  | 0.799934 |  | 0.743700
4.500000 | 4.700000 | 1 | 1 | 0 | 1.000000 | 12.425775 |  |  | 12.425775 | 12.425775 | 12.054056 |  | 0.859087 |  | 0.737268
4.500000 | 4.800000 | 1 | 1 | 0 | 1.000000 | 12.679899 |  |  | 12.679899 | 12.679899 | 13.332039 |  | 0.916153 |  | 0.732583
4.500000 | 4.900000 | 1 | 1 | 0 | 1.000000 | 13.001254 |  |  | 13.001254 | 13.001254 | 13.584495 |  | 0.988800 |  | 0.726324
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
