JCastel358/Eltec406mca/tech_app/v6_esp32/README.md

# Eltec 406MCA ESP32 Tester v6 for Xubuntu

This folder is the isolated v6 successor to the v5 ESP32/ADS1256 tester. It
keeps the guided batch workflow, battery and offset checks, waveform snapshots,
simulator, sensitivity/polarity/SNR gates, and strict serial diagnostics while
replacing fixed capture modes with adaptive peak-delta stabilization. Versions
v1 through v5 remain separate and unchanged.

## Reference sensor and test order

ADS1256 AIN1 is the permanently-mounted reference sensor and is a required
emitter-health gate. On the Batch information screen, the **AIN1 reference**
card simply shows whether the reference unit is calibrated. With a
known-good/new emitter installed, press **Calibrate reference unit**. For each
reading the app starts streaming immediately when PWM turns on; there is no
fixed warm-up delay. It requires five consecutive cycle-to-cycle robust-peak
deltas at or below `0.250 mV`, then averages the peak-to-peak response of the
next five complete cycles. Five of those stable reference readings are averaged
and saved here:

```text
~/Documents/Eltec_406MCA_Test_Results/v6_esp32/reference_sensor_calibration.json
```

All five calibration readings must themselves be repeatable within 10 percent
of their average. Calibration failure leaves DUT testing locked.

Every production measurement then follows this order:

```text
battery -> PWM on + immediate AIN1 peak-stability check -> five-cycle average -> +/-10% gate
        -> PWM off -> AIN0 DUT offset -> PWM on -> AIN0 adaptive capture
```

The app does not read AIN0 unless the fresh AIN1 reading is inside the saved
window. An out-of-window reading immediately stops the sequence, invalidates
the saved calibration, and blocks further DUT tests. Replace/check the emitter,
then use the visible **Calibrate AIN1 reference** button to establish a new
five-reading baseline. Each completed batch CSV records the calibration,
allowed window, fresh AIN1 reading, and percent drift used for that DUT.

Simulator mode uses a clearly identified synthetic in-range reference and does
not create or overwrite the hardware calibration.

The completed sensor screen emphasizes the large green **PASS** or red **FAIL**
verdict. Every FAIL also shows a required standard failure-mode selector. Use
**Show test details** to reveal offset, sensitivity, polarity, confidence, SNR,
stability telemetry, and diagnostic failure reasons. The
separate **Show waveform** control remains available independently.
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
