JCastel358/Eltec406mca/tech_app/v5_esp32/README.md

# Eltec 406MCA ESP32 Tester for Xubuntu

This folder contains the Xubuntu edition of the 406MCA emitter tester. It uses
the ESP32/ADS1256 rig and leaves the historical Windows/LabJack v4 application
unchanged.

It keeps the v4 guided batch workflow, CSV/snapshot output, simulator, live
waveform preview, Fast/Validation/Full capture modes, battery lockout, offset,
sensitivity, polarity, and pass/fail analysis. The hardware layer is replaced
with the ESP32/ADS1256 serial protocol on GPIO25/AIN0/AIN7.

## Firmware and rig status

The tester requires `Arduino/Eltec/Eltec.ino` **v1.7 or newer**. Version 1.7
verifies that the ADS1256 really accepted the 1000 SPS configuration, latches
real DRDY edges, and reports any ADC overrun. The application refuses older
firmware so a bad stream cannot create a test result.
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
