JCastel358/Eltec406mca/analysis/reports/405M22_noise_filter_chain.png

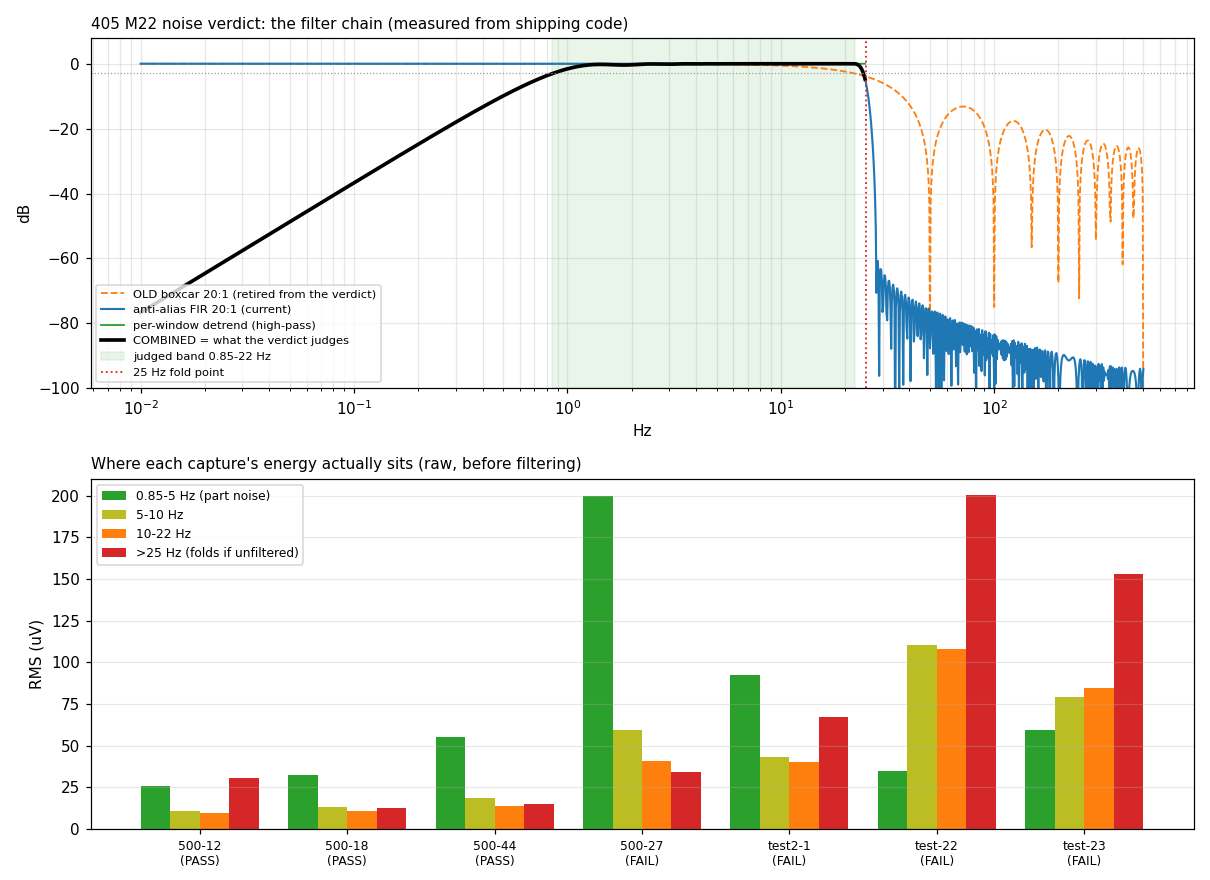
analysis/reports/405M22_noise_filter_chain.png
