JCastel358/Eltec406mca/hardware/single_detector_usb_master_r1/exports/board_review/final_routed_review/rendered_pages/copper_bottom-1.png

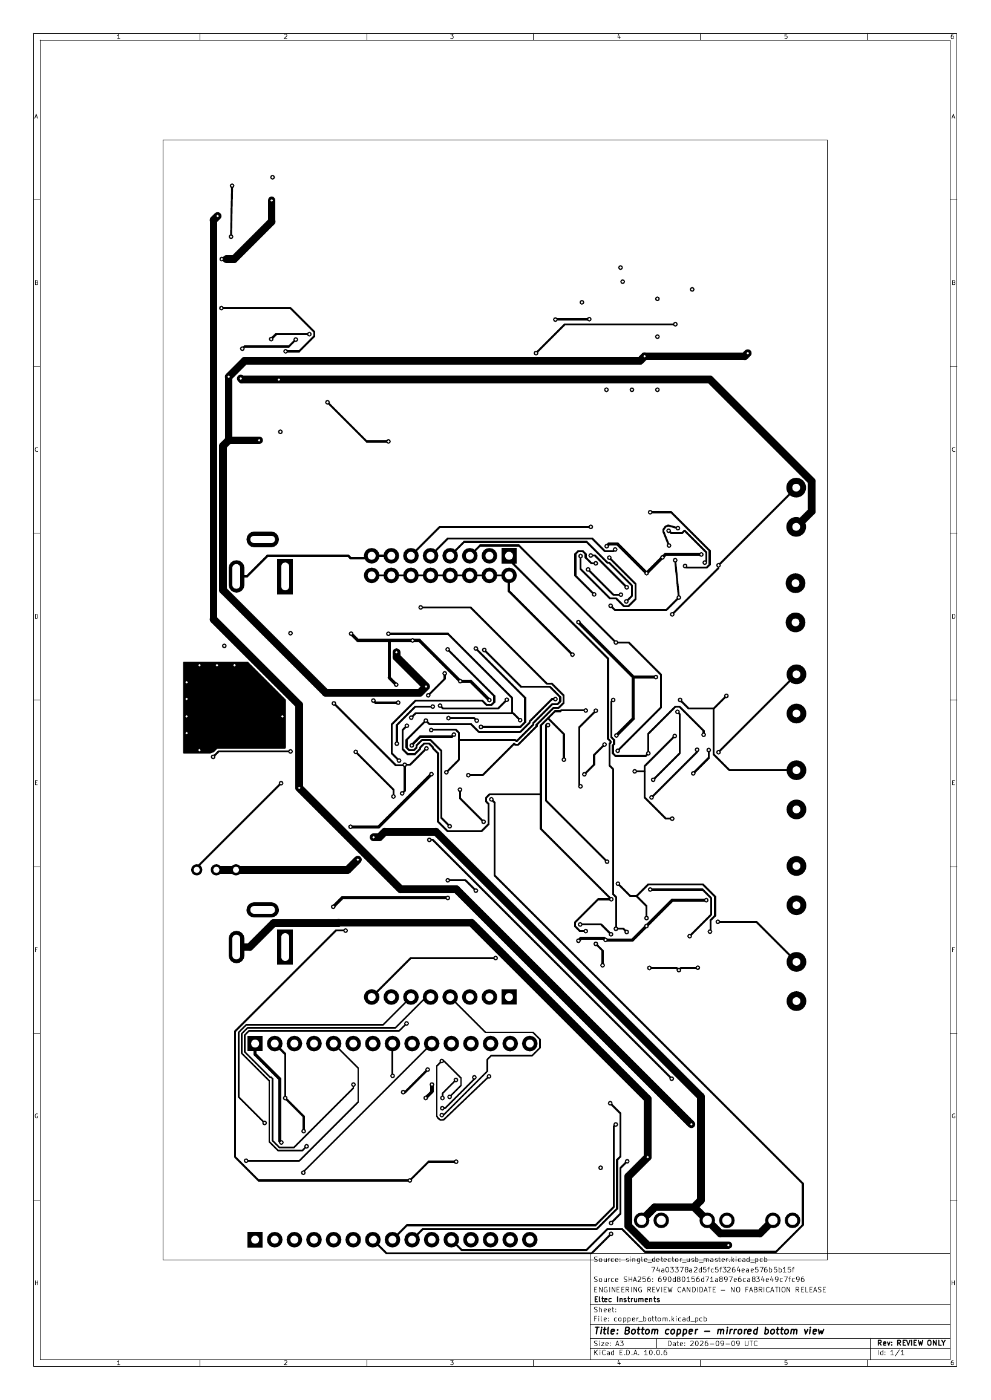
hardware/single_detector_usb_master_r1/exports/board_review/final_routed_review/rendered_pages/copper_bottom-1.png
