JCastel358/Eltec406mca/hardware/single_detector_usb_master_r1/exports/board_review/final_routed_review_v2/rendered_pages/copper_top-1.png

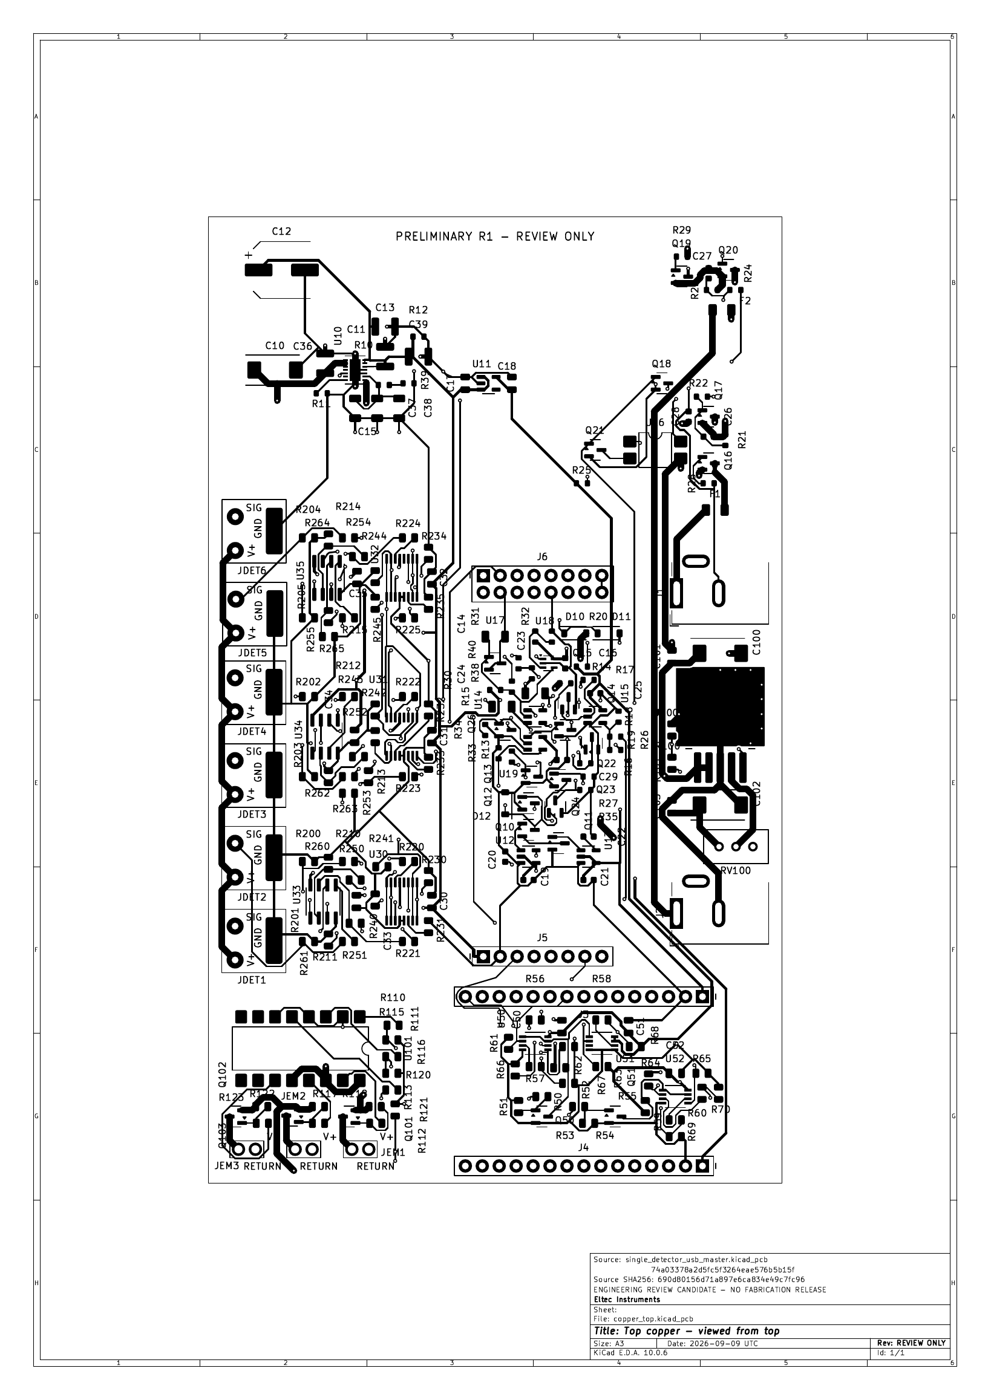
hardware/single_detector_usb_master_r1/exports/board_review/final_routed_review_v2/rendered_pages/copper_top-1.png
