JCastel358/Eltec406mca/hardware/single_detector_usb_master_r1/exports/board_review/trial01_copper_b/rendered_pages/copper_layers-4.png

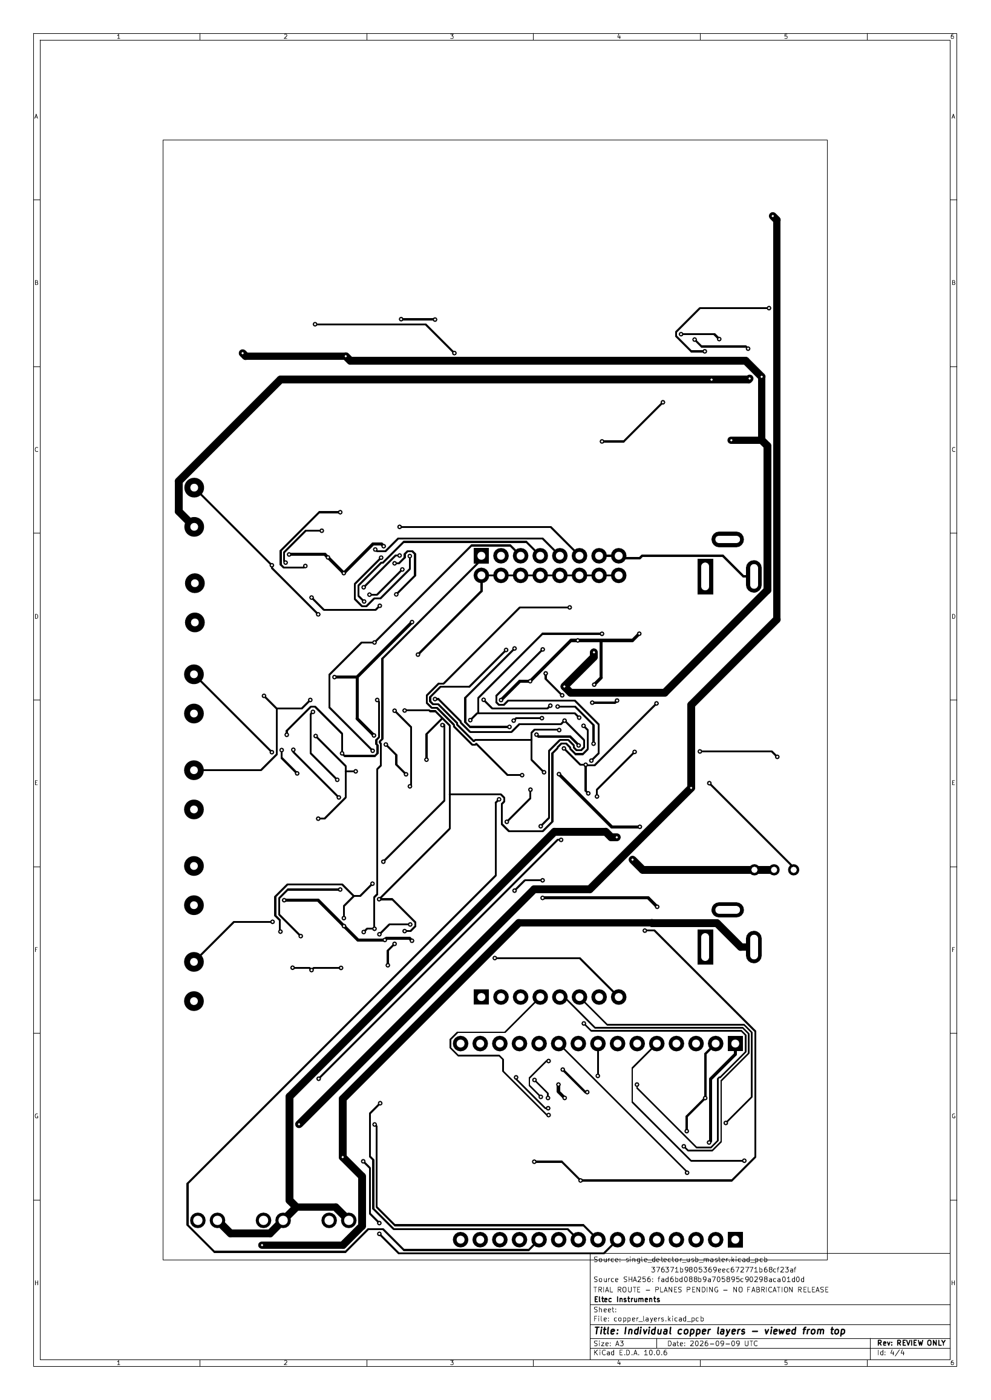
hardware/single_detector_usb_master_r1/exports/board_review/trial01_copper_b/rendered_pages/copper_layers-4.png
