JCastel358/Eltec406mca/hardware/single_detector_usb_master_r1/reports/detector_pdf_review/406MBN_2.png

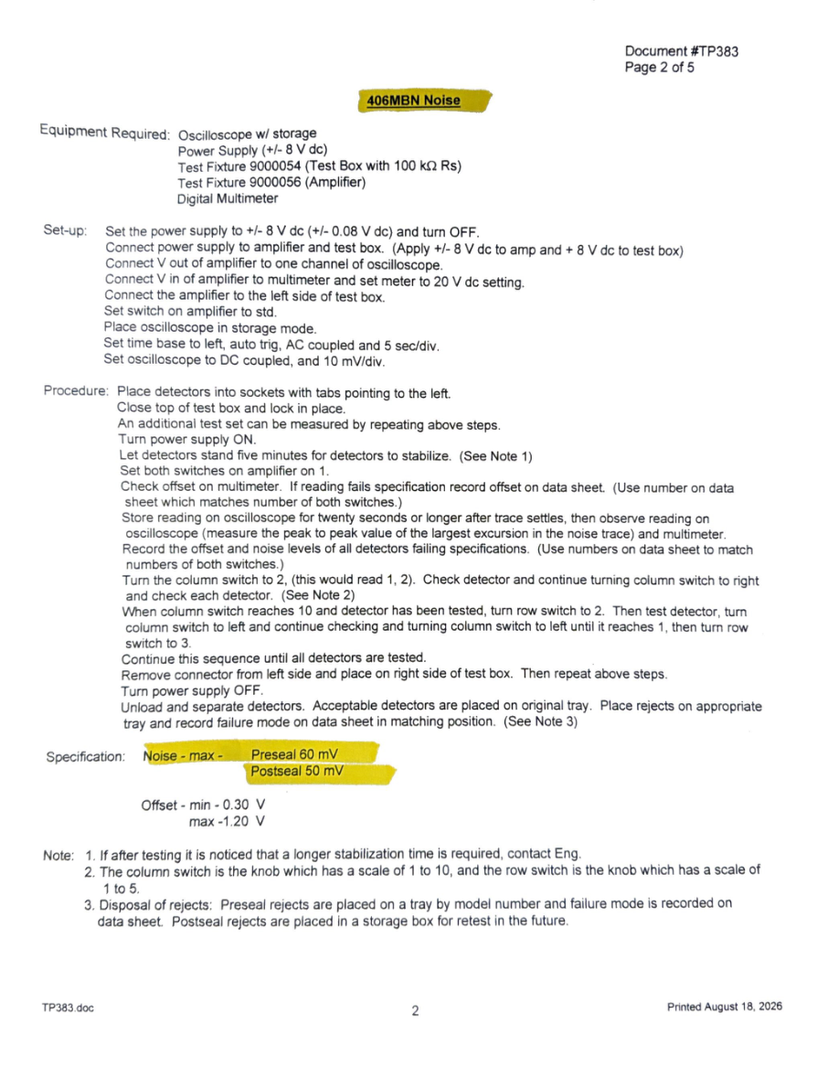
hardware/single_detector_usb_master_r1/reports/detector_pdf_review/406MBN_2.png
