JCastel358/Eltec406mca/hardware/single_detector_usb_master_r1/reports/detector_pdf_review/Data-Sheet-Model-405_1.png

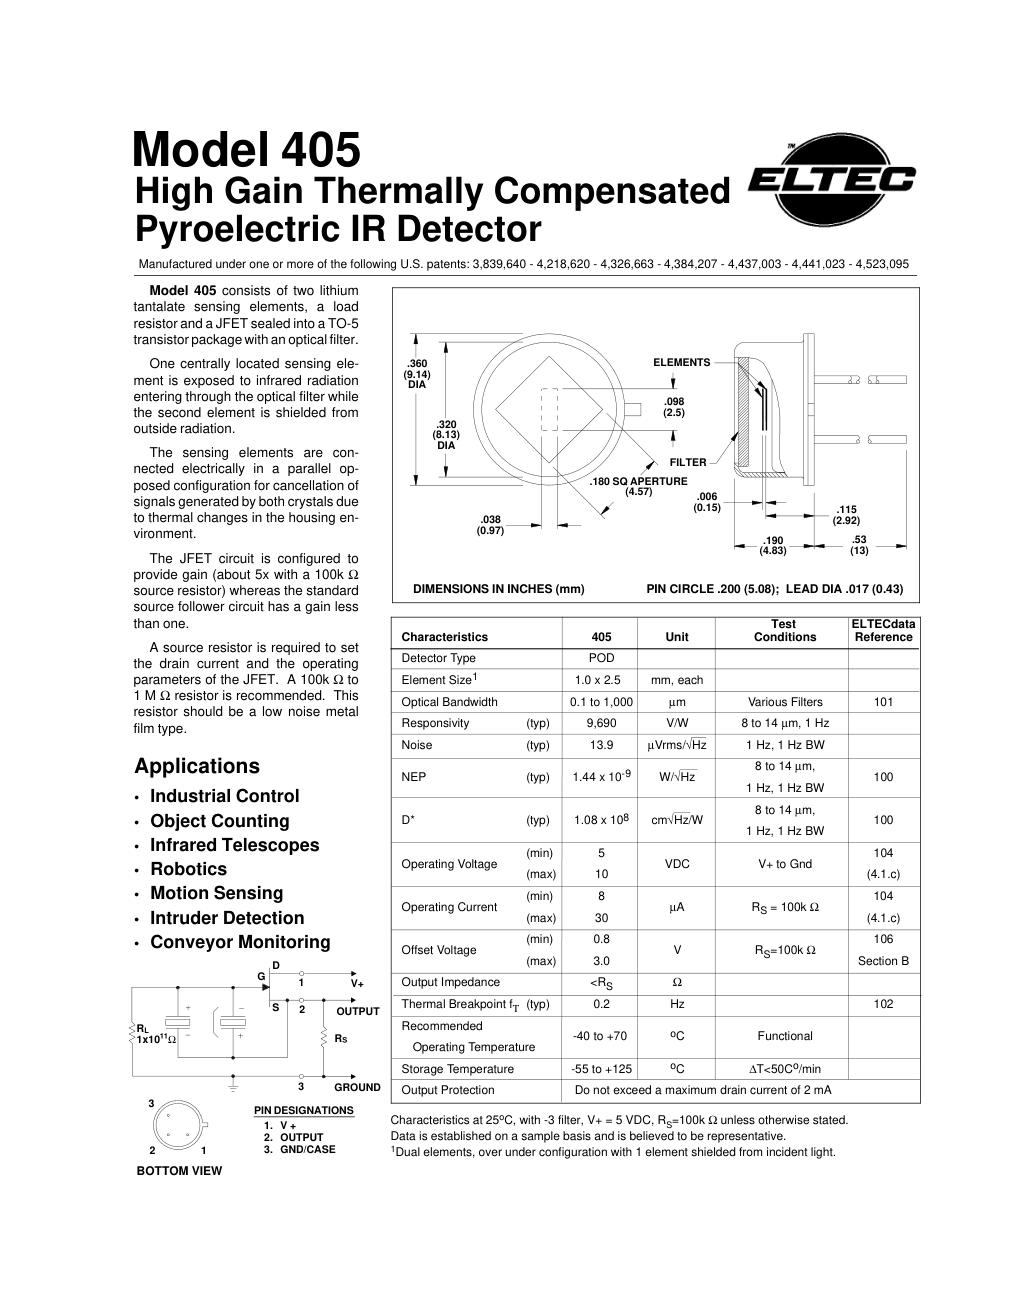
hardware/single_detector_usb_master_r1/reports/detector_pdf_review/Data-Sheet-Model-405_1.png
