JCastel358/Eltec406mca/hardware/single_detector_usb_master_r1/reports/drill_map_visual_review_2ab4937f/single_detector_usb_master-PTH-drl_map-1.png

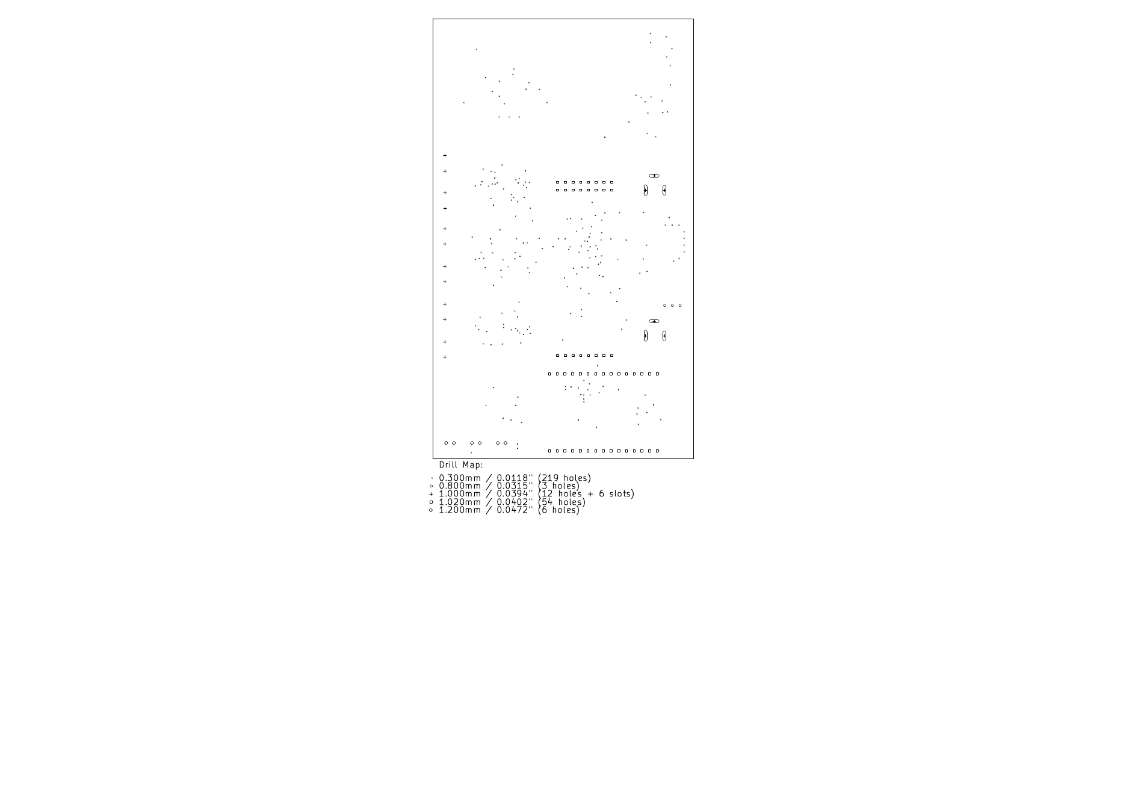
hardware/single_detector_usb_master_r1/reports/drill_map_visual_review_2ab4937f/single_detector_usb_master-PTH-drl_map-1.png
