JCastel358/Eltec406mca/hardware/single_detector_usb_master_r1/reports/placement_candidate.png

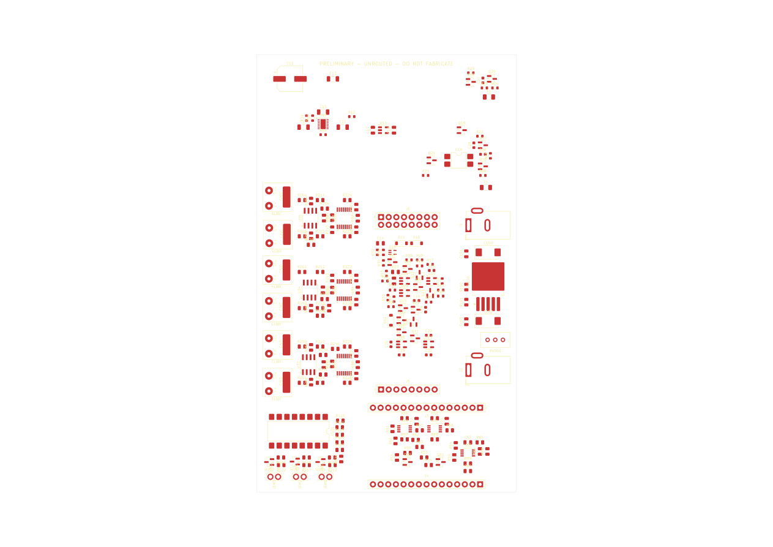
hardware/single_detector_usb_master_r1/reports/placement_candidate.png
