JCastel358/Eltec406mca/hardware/single_detector_usb_master_r1/reports/reference_planes/native_in1.png

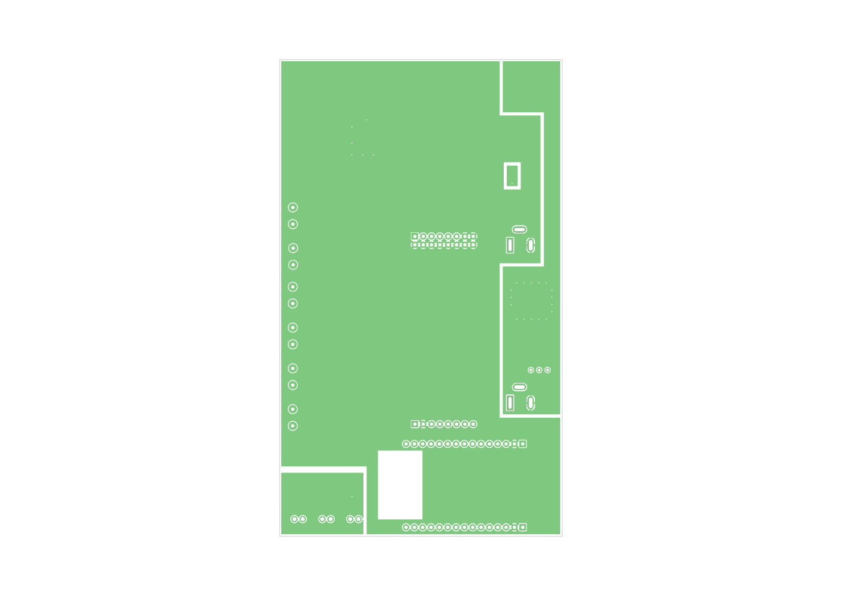
hardware/single_detector_usb_master_r1/reports/reference_planes/native_in1.png
