JCastel358/Eltec406mca/hardware/single_detector_usb_master_r1/reports/reference_planes/plane_plan.png

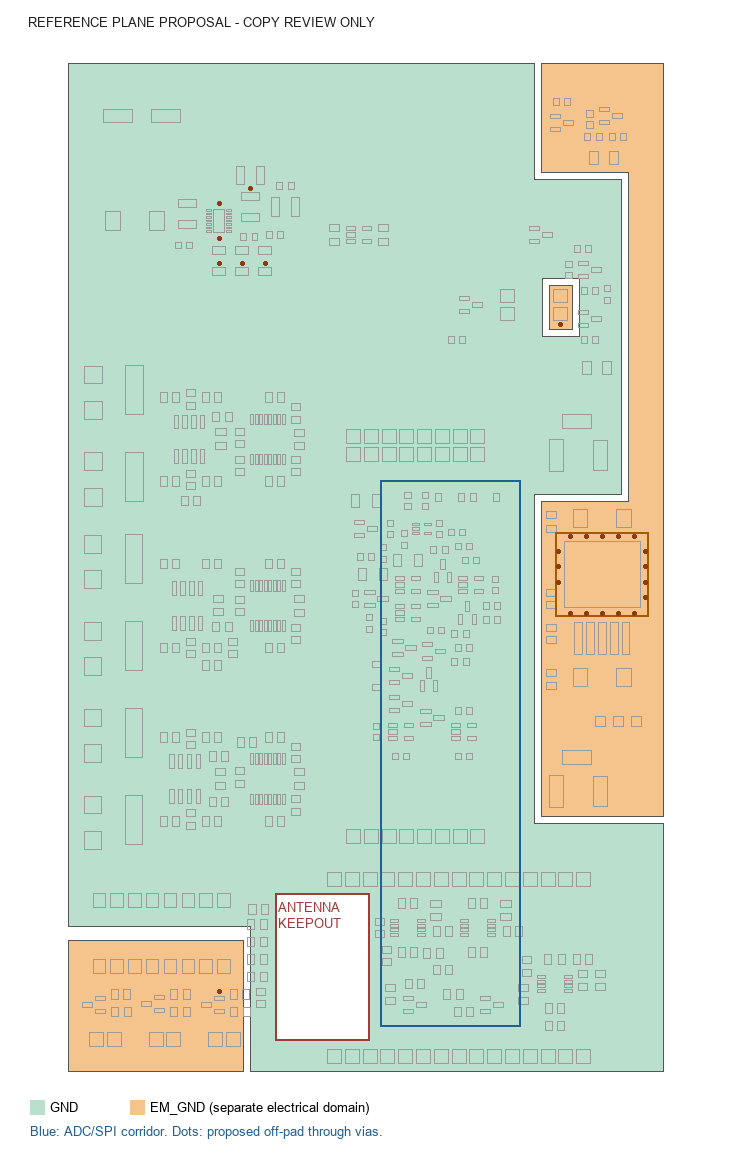
hardware/single_detector_usb_master_r1/reports/reference_planes/plane_plan.png
