JCastel358/Eltec406mca/hardware/single_detector_usb_master_r1/reports/reference_planes_routed/native_front.png

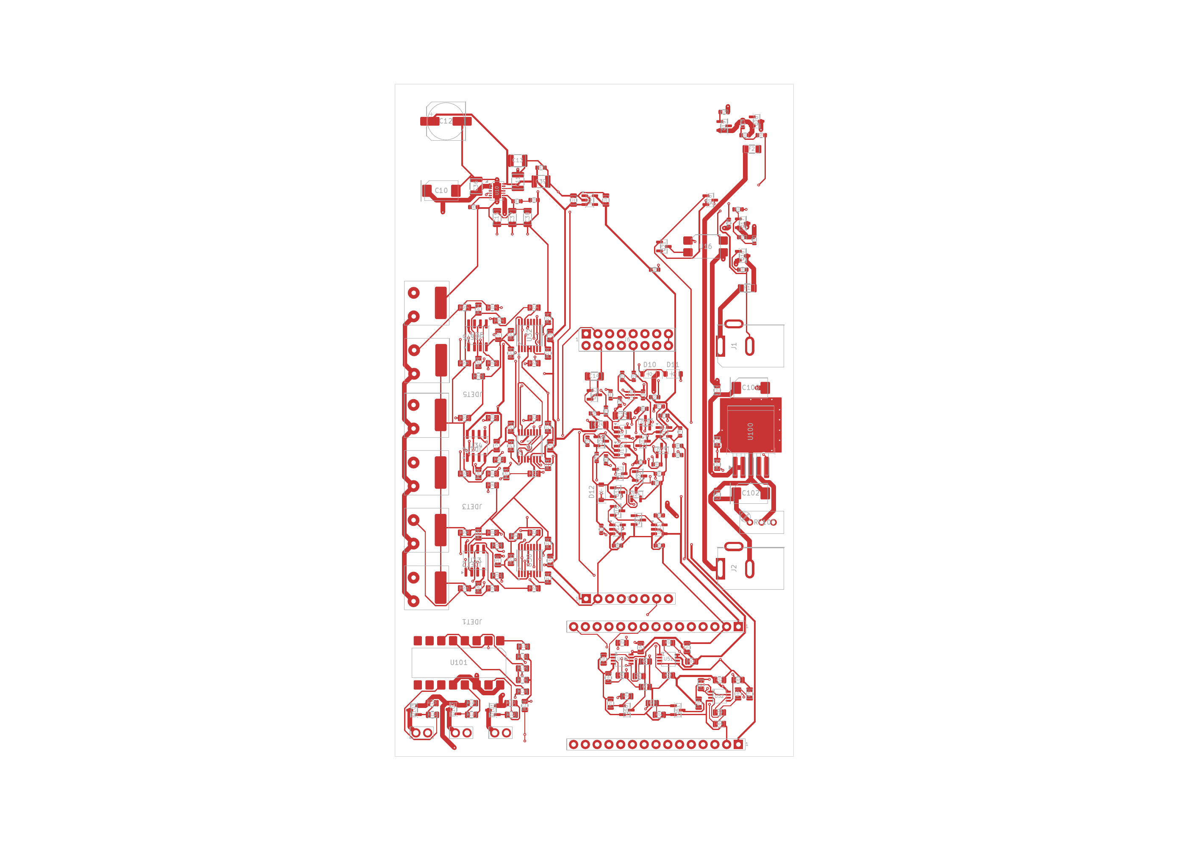
hardware/single_detector_usb_master_r1/reports/reference_planes_routed/native_front.png
