JCastel358/Eltec406mca/hardware/single_detector_usb_master_r1/reports/routing/trial01/power_top_closeup.png

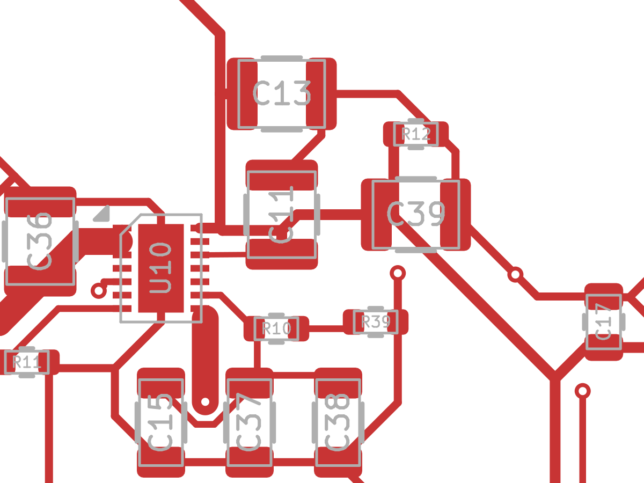
hardware/single_detector_usb_master_r1/reports/routing/trial01/power_top_closeup.png
