JCastel358/Eltec406mca/hardware/single_detector_usb_master_r1/reports/schematic_visual/adc_module_detail-03.png

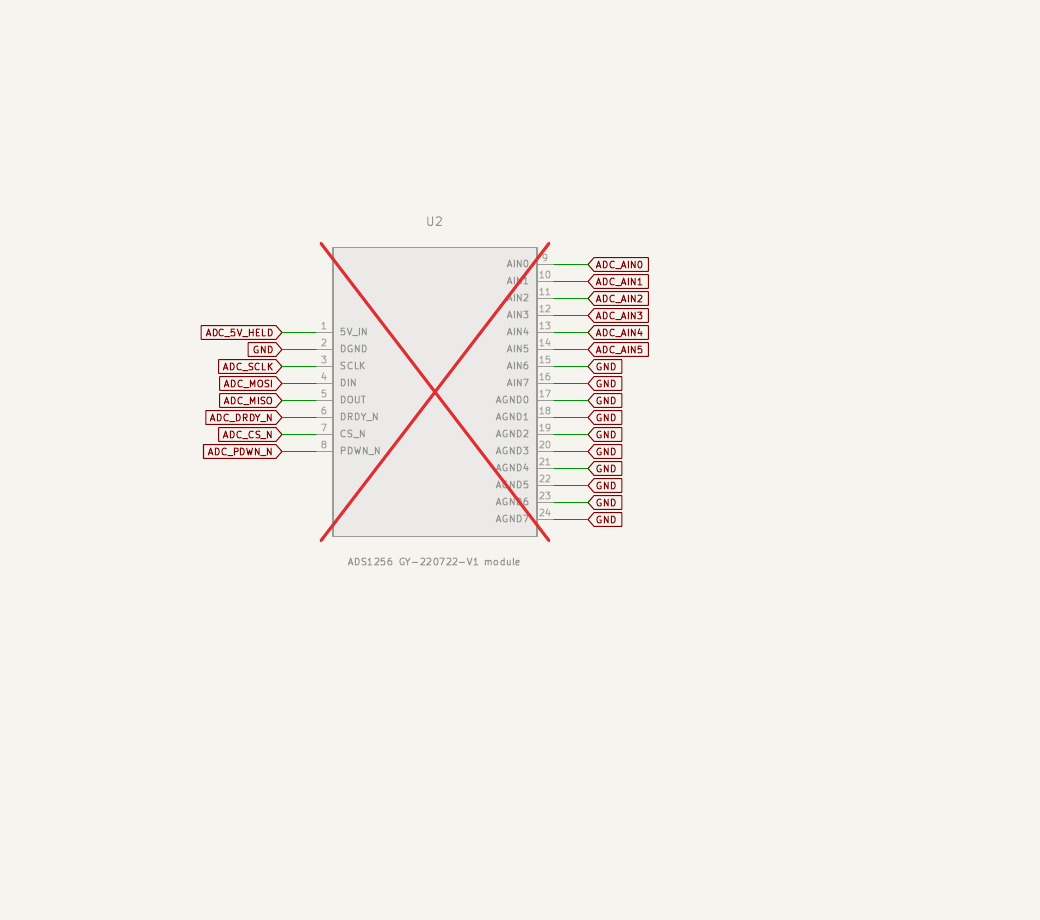
hardware/single_detector_usb_master_r1/reports/schematic_visual/adc_module_detail-03.png
