JCastel358/Eltec406mca/hardware/single_detector_usb_master_r1/reports/schematic_visual/current_page_15.png

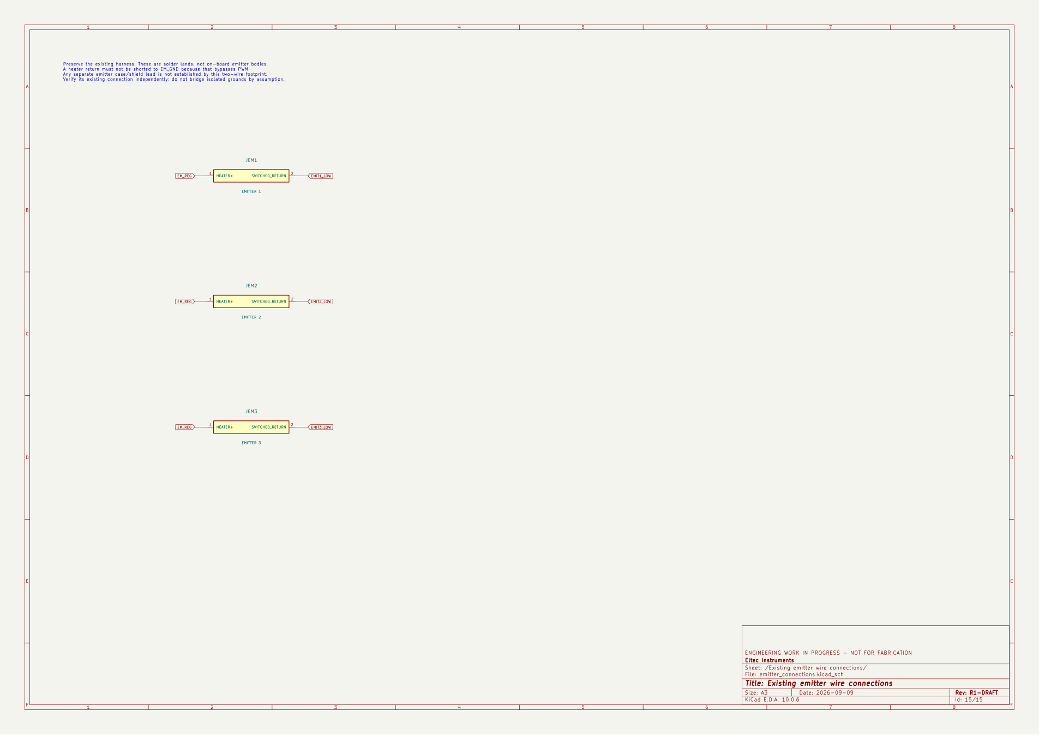
hardware/single_detector_usb_master_r1/reports/schematic_visual/current_page_15.png
