JCastel358/Eltec406mca/hardware/single_detector_usb_master_r1/reports/schematic_visual_current/page13_C102_detail-13.png

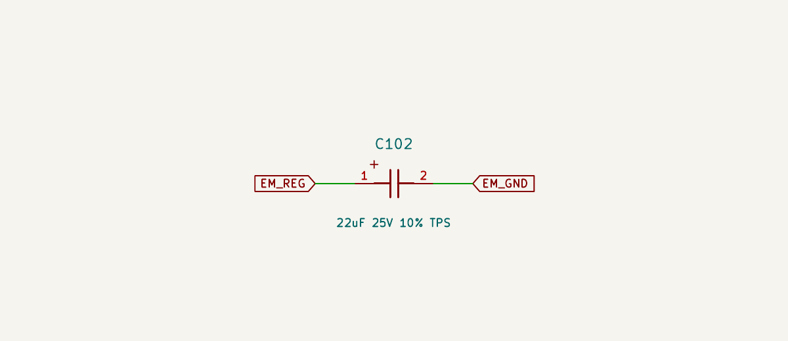
hardware/single_detector_usb_master_r1/reports/schematic_visual_current/page13_C102_detail-13.png
