JCastel358/Eltec406mca/hardware/single_detector_usb_master_r1/reports/silkscreen_cleanup/emitter_detail.png

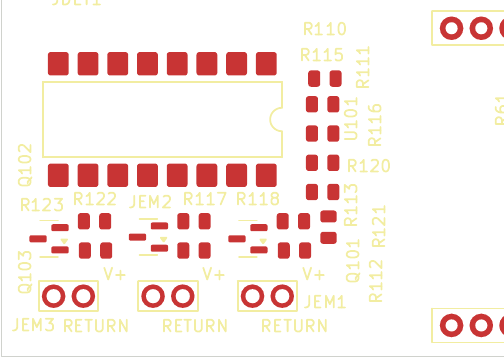
hardware/single_detector_usb_master_r1/reports/silkscreen_cleanup/emitter_detail.png
