JCastel358/Eltec406mca/hardware/single_detector_usb_master_r1/reports/silkscreen_cleanup/overview.png

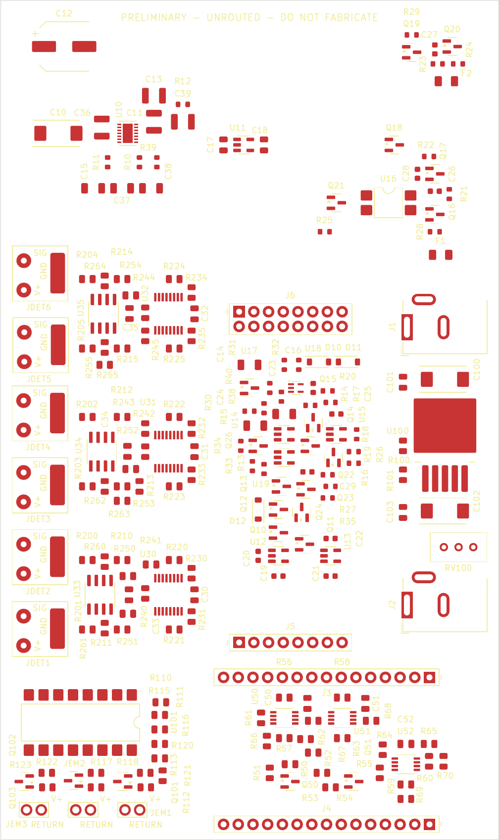
hardware/single_detector_usb_master_r1/reports/silkscreen_cleanup/overview.png
