JCastel358/Eltec406mca/hardware/single_detector_usb_master_r1/research/murata_grm32er71e226ke15_curves.png

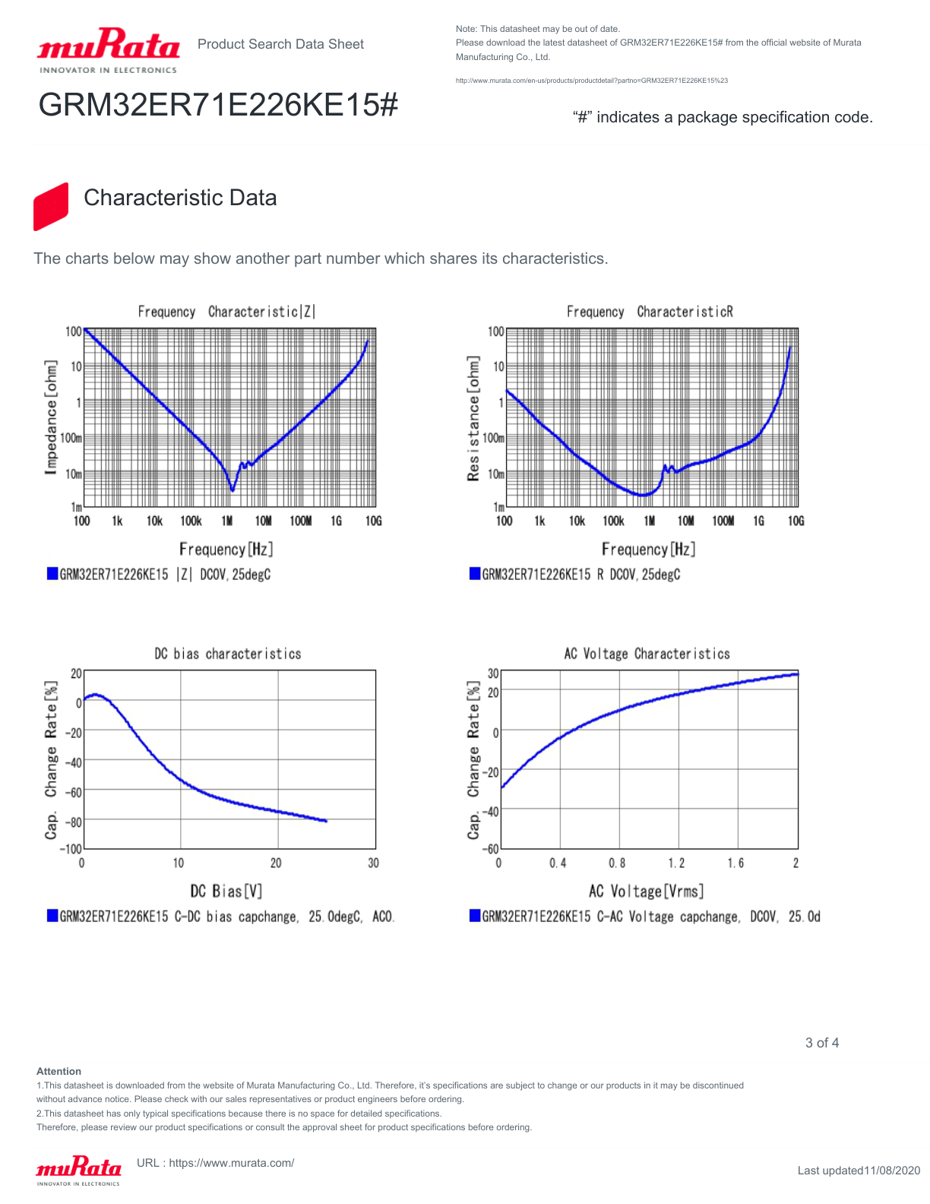
hardware/single_detector_usb_master_r1/research/murata_grm32er71e226ke15_curves.png
