JCastel358/Eltec406mca/hardware/single_detector_usb_master_r1/source_reference/SingleDetectorPCBschematic.png

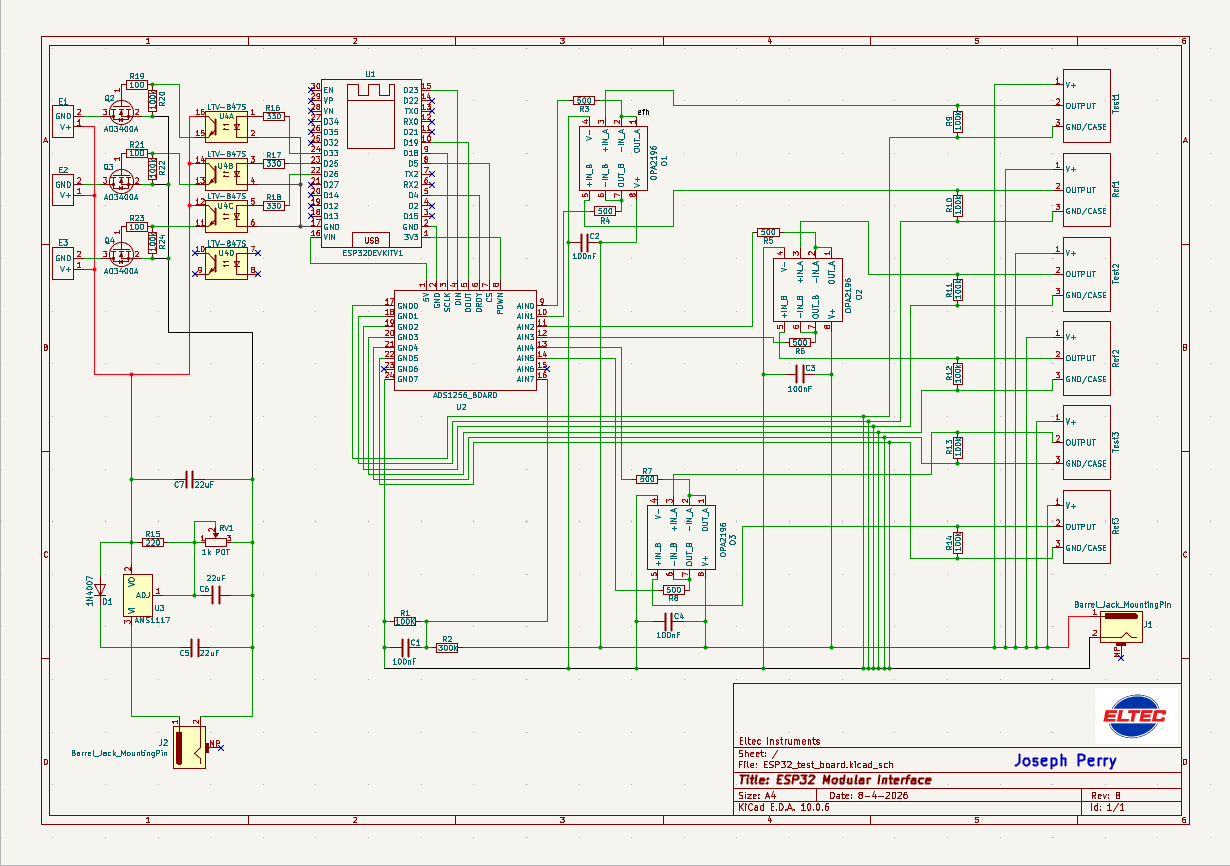
hardware/single_detector_usb_master_r1/source_reference/SingleDetectorPCBschematic.png
