JCastel358/Eltec406mca/tmp/emitter_stage_check/ir56_page2.png

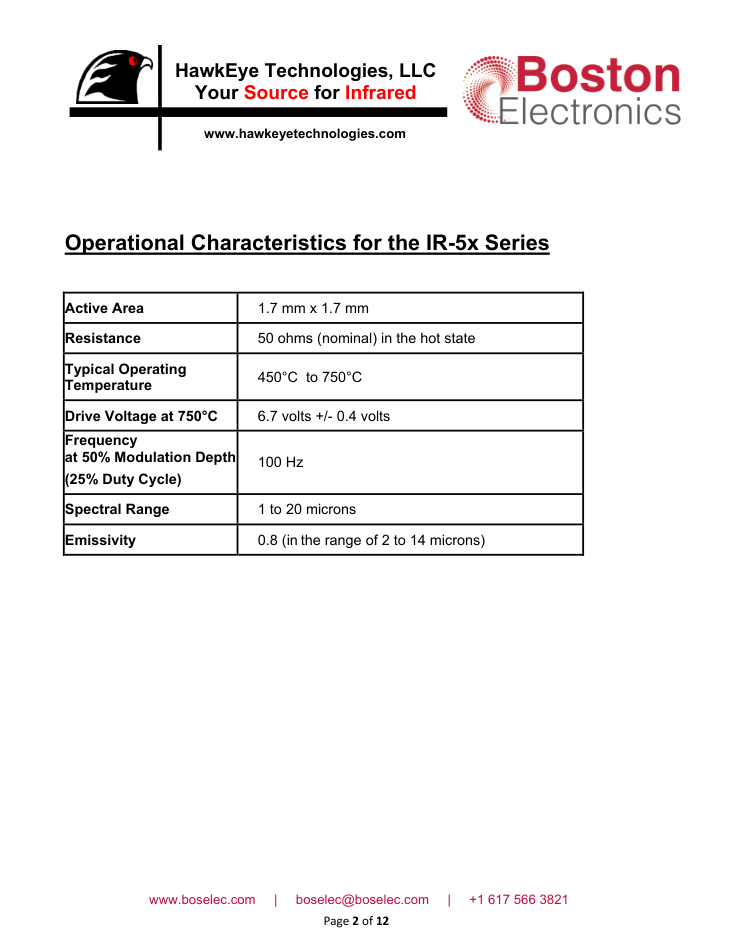
tmp/emitter_stage_check/ir56_page2.png
