JCastel358/Eltec406mca/tmp/emitter_stage_check/ir56_page4.png

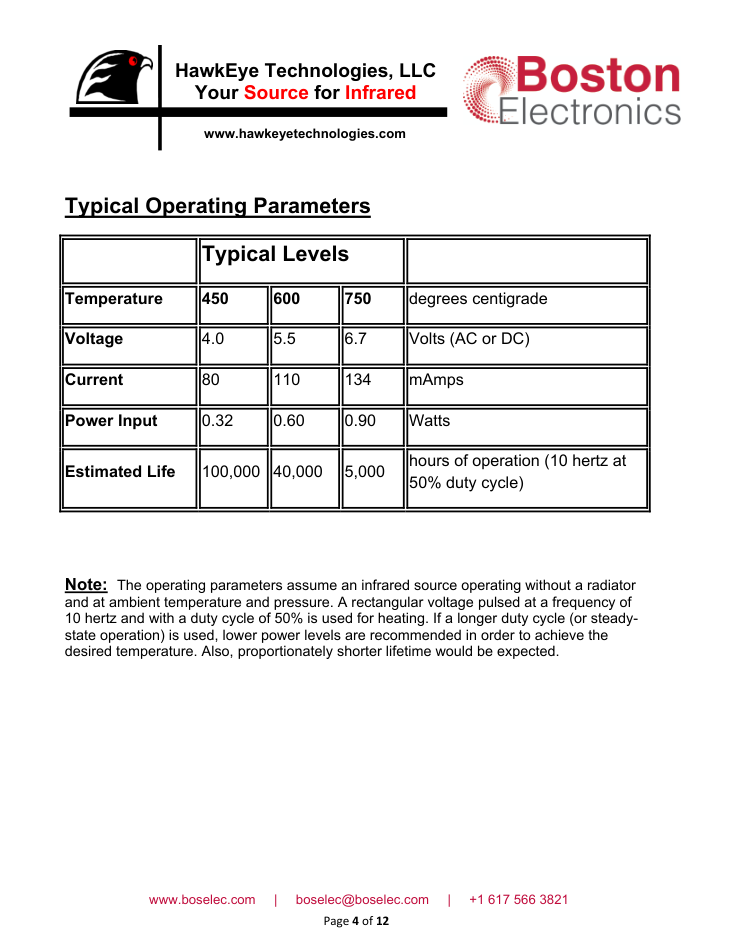
tmp/emitter_stage_check/ir56_page4.png
