JCastel358/Eltec406mca/tmp/emitter_stage_check/opa2325_clamp.png

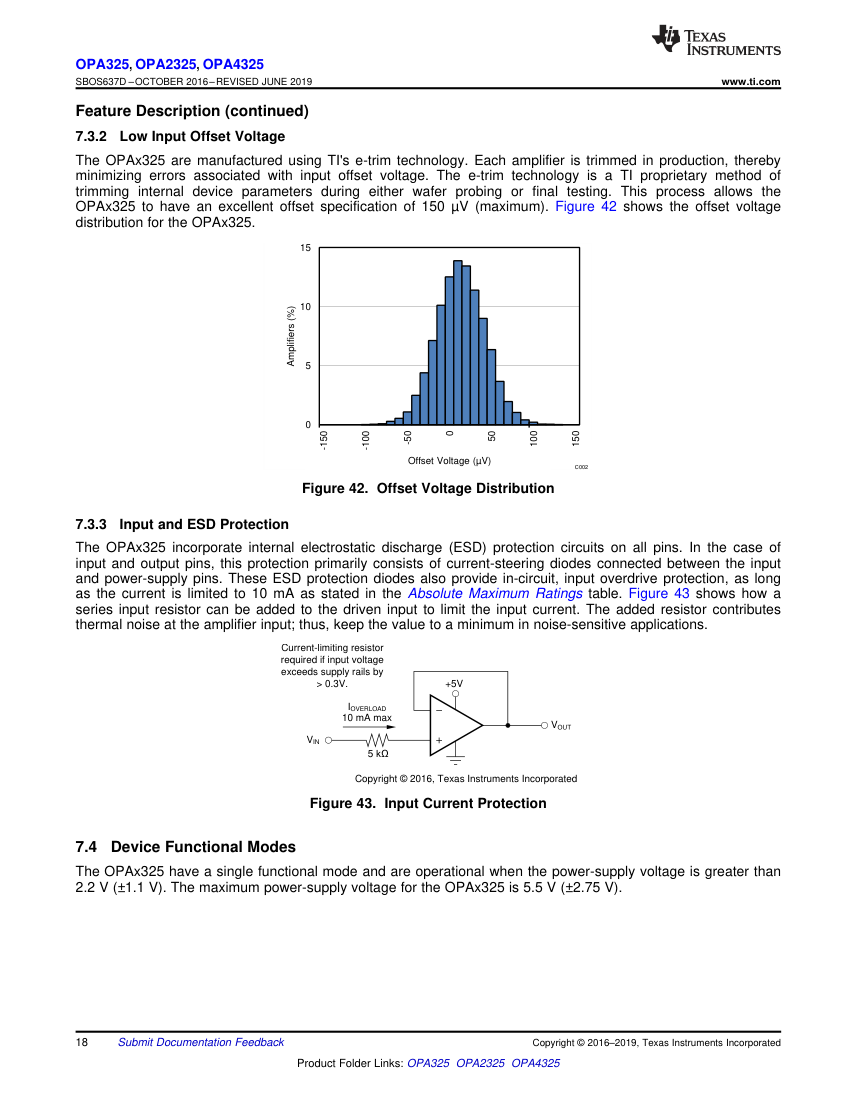
tmp/emitter_stage_check/opa2325_clamp.png
