JCastel358/Eltec406mca/tmp/emitter_stage_check/opa2325_power.png

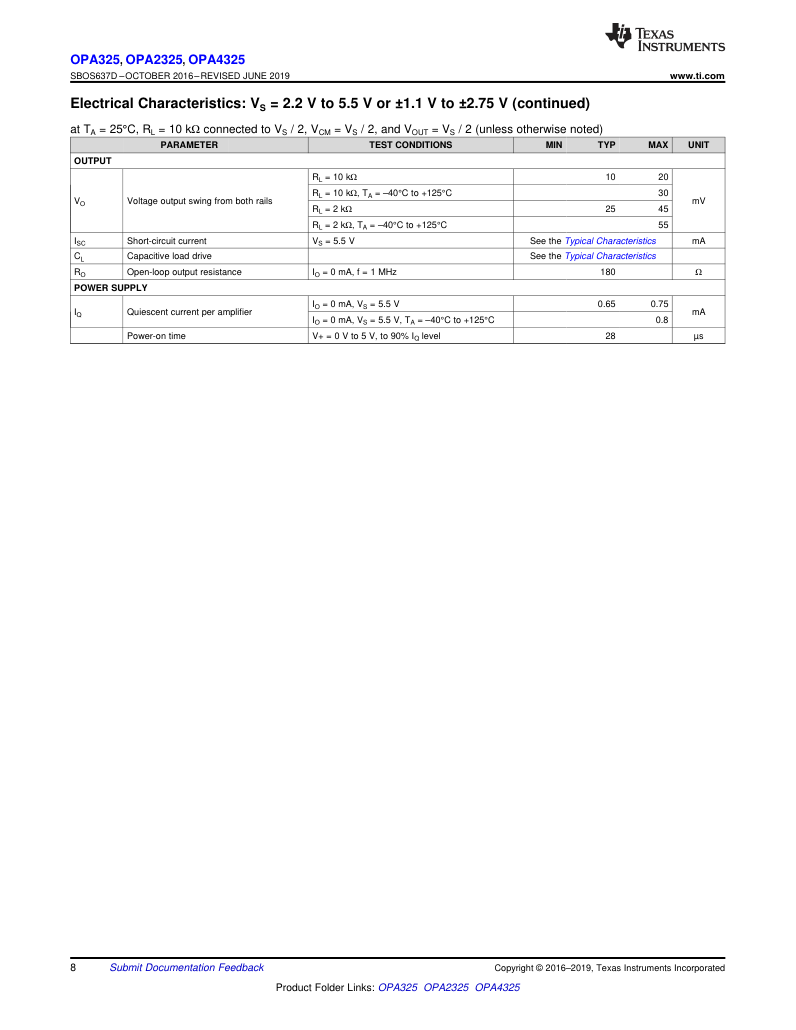
tmp/emitter_stage_check/opa2325_power.png
