JCastel358/Eltec406mca/tmp/emitter_stage_check/opa2325_table.png

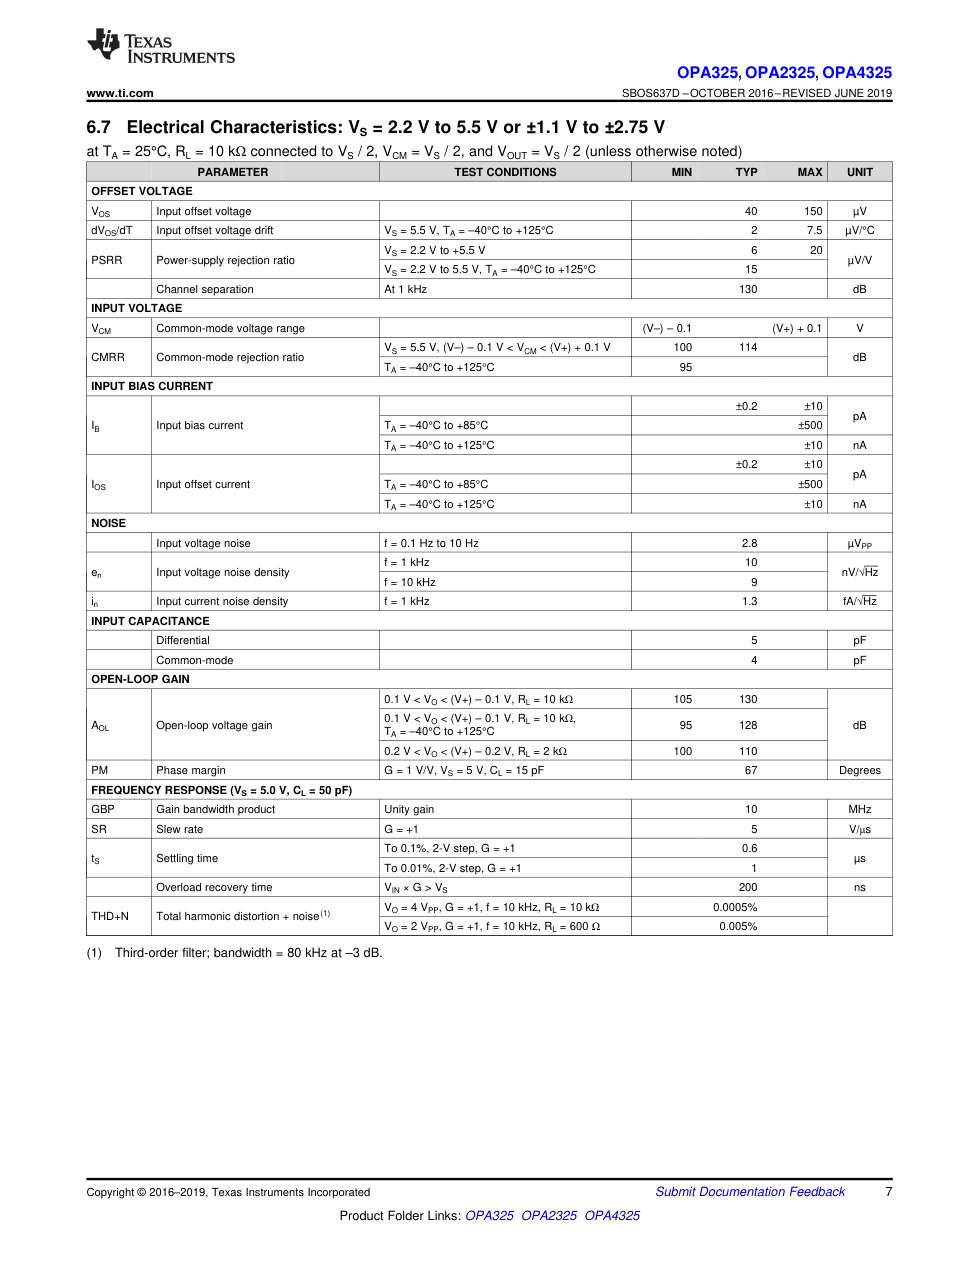
tmp/emitter_stage_check/opa2325_table.png
