JCastel358/Eltec406mca/tmp/emitter_stage_check/tps3842_table.png

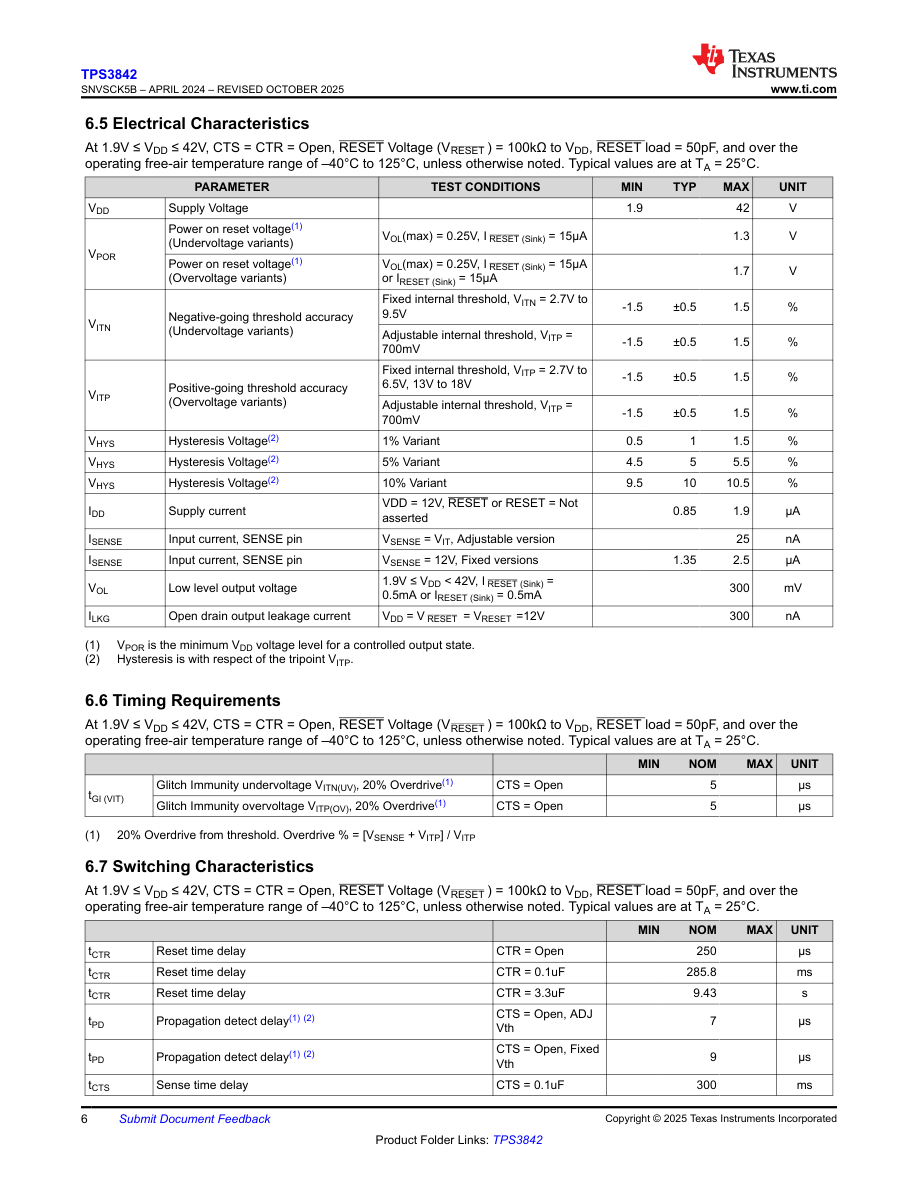
tmp/emitter_stage_check/tps3842_table.png
