JCastel358/Eltec406mca/tmp/emitter_stage_check/tps_table6.png

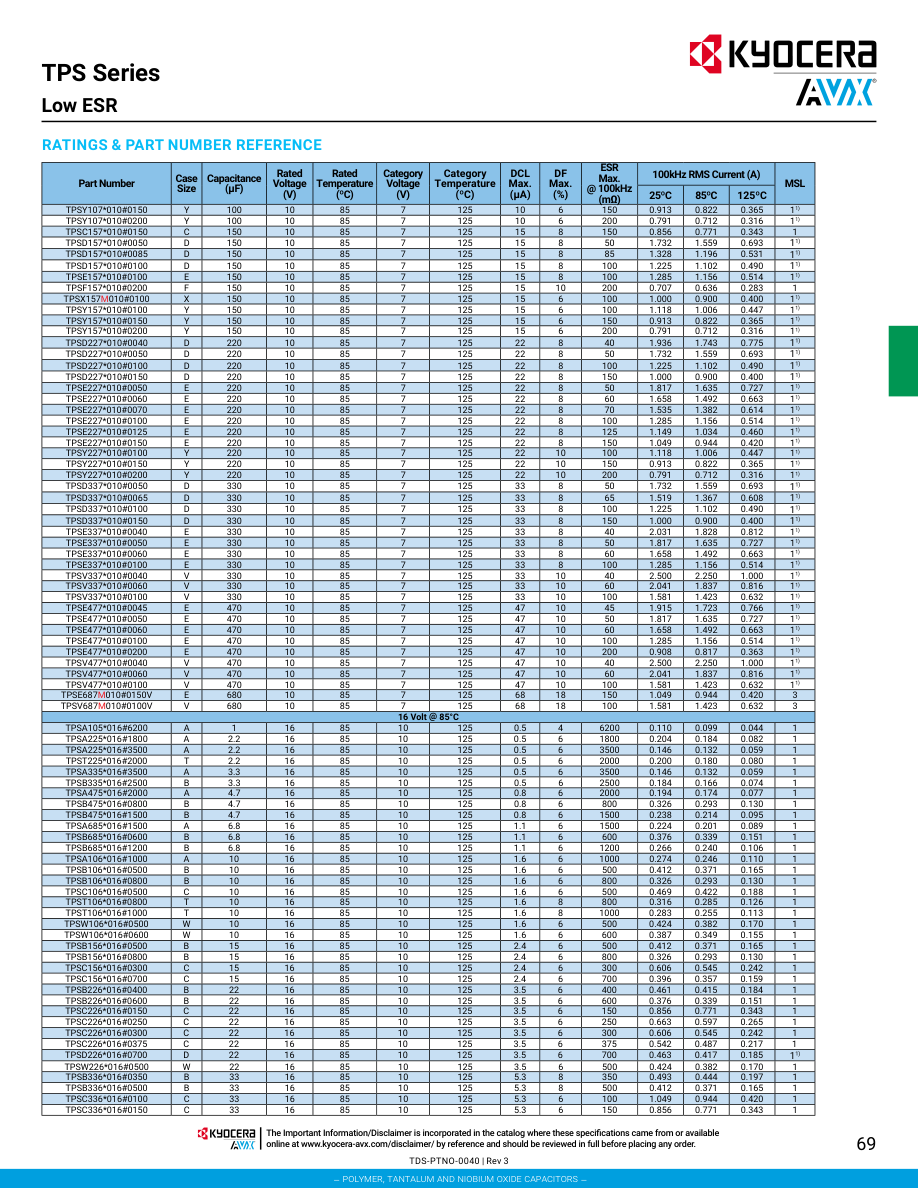
tmp/emitter_stage_check/tps_table6.png
