JCastel358/Eltec406mca/tmp/emitter_stage_check/tps_table8.png

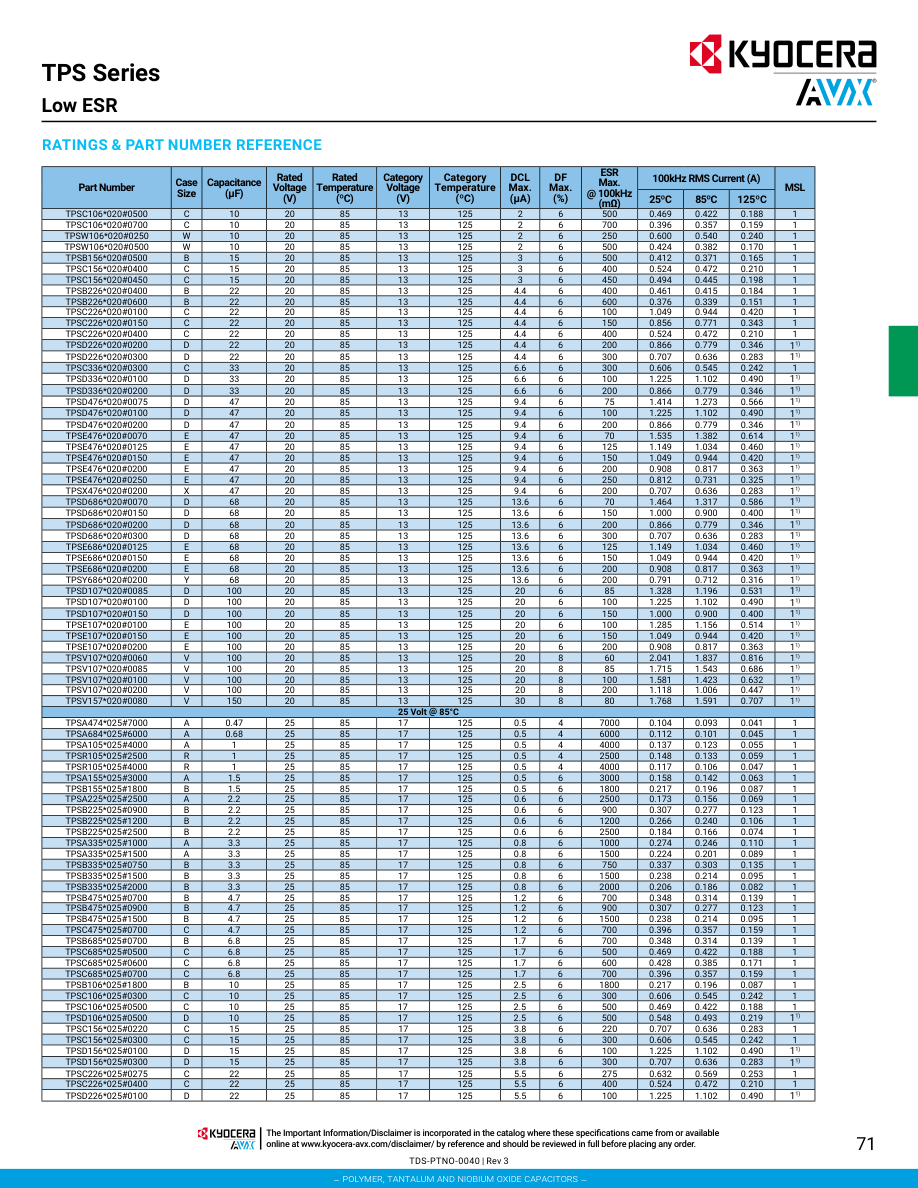
tmp/emitter_stage_check/tps_table8.png
