JCastel358/Eltec406mca/tmp/power_board_schematic/rendered/page-1.png

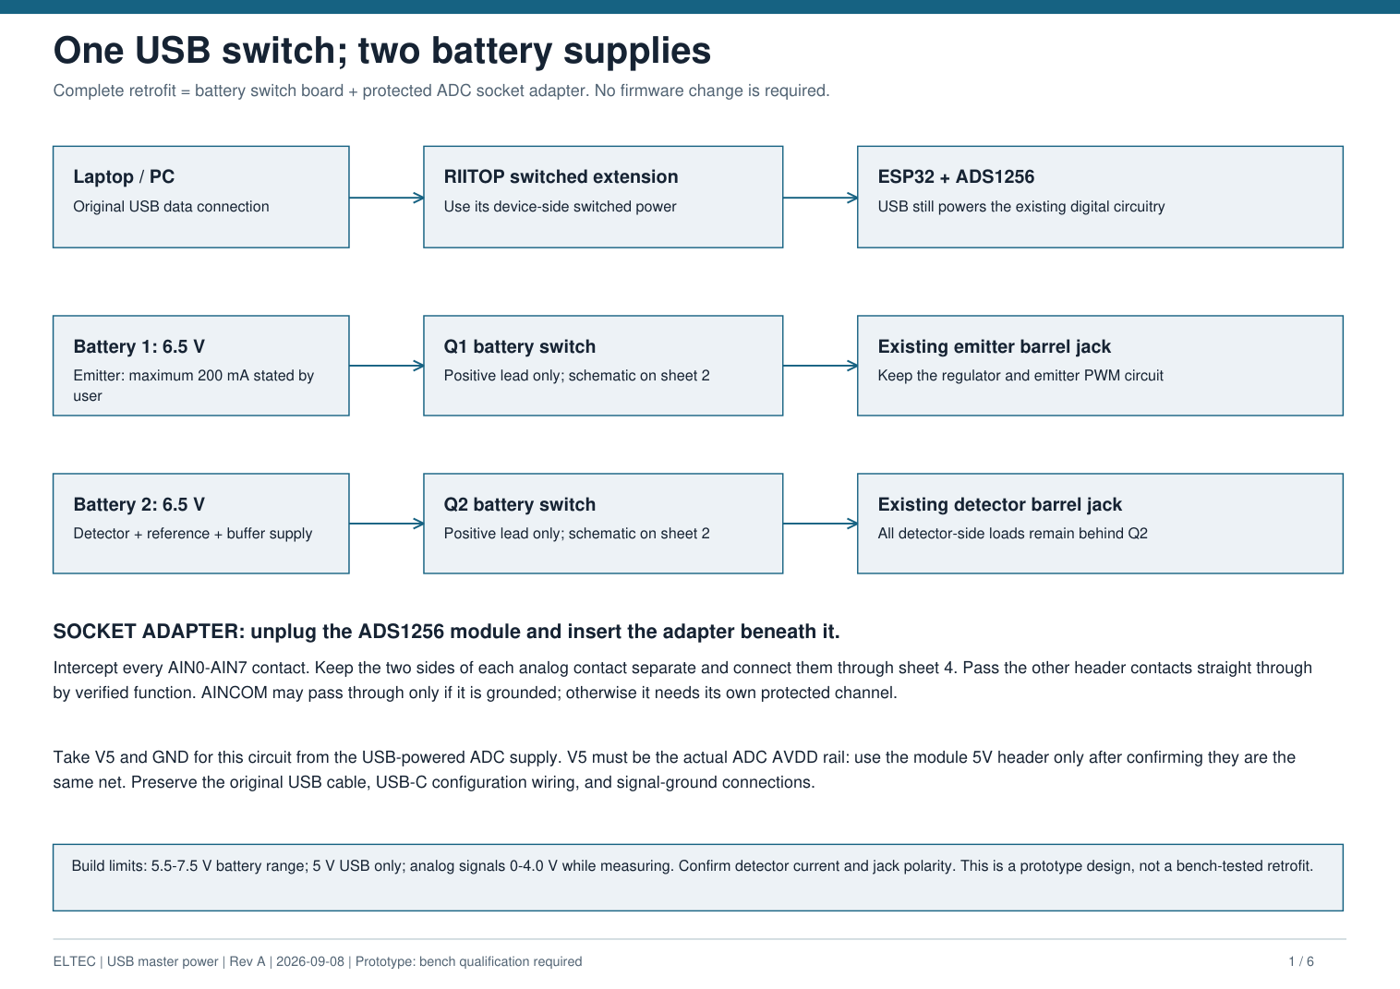
tmp/power_board_schematic/rendered/page-1.png
