JCastel358/Eltec406mca/tmp/power_board_schematic/rendered/page-4.png

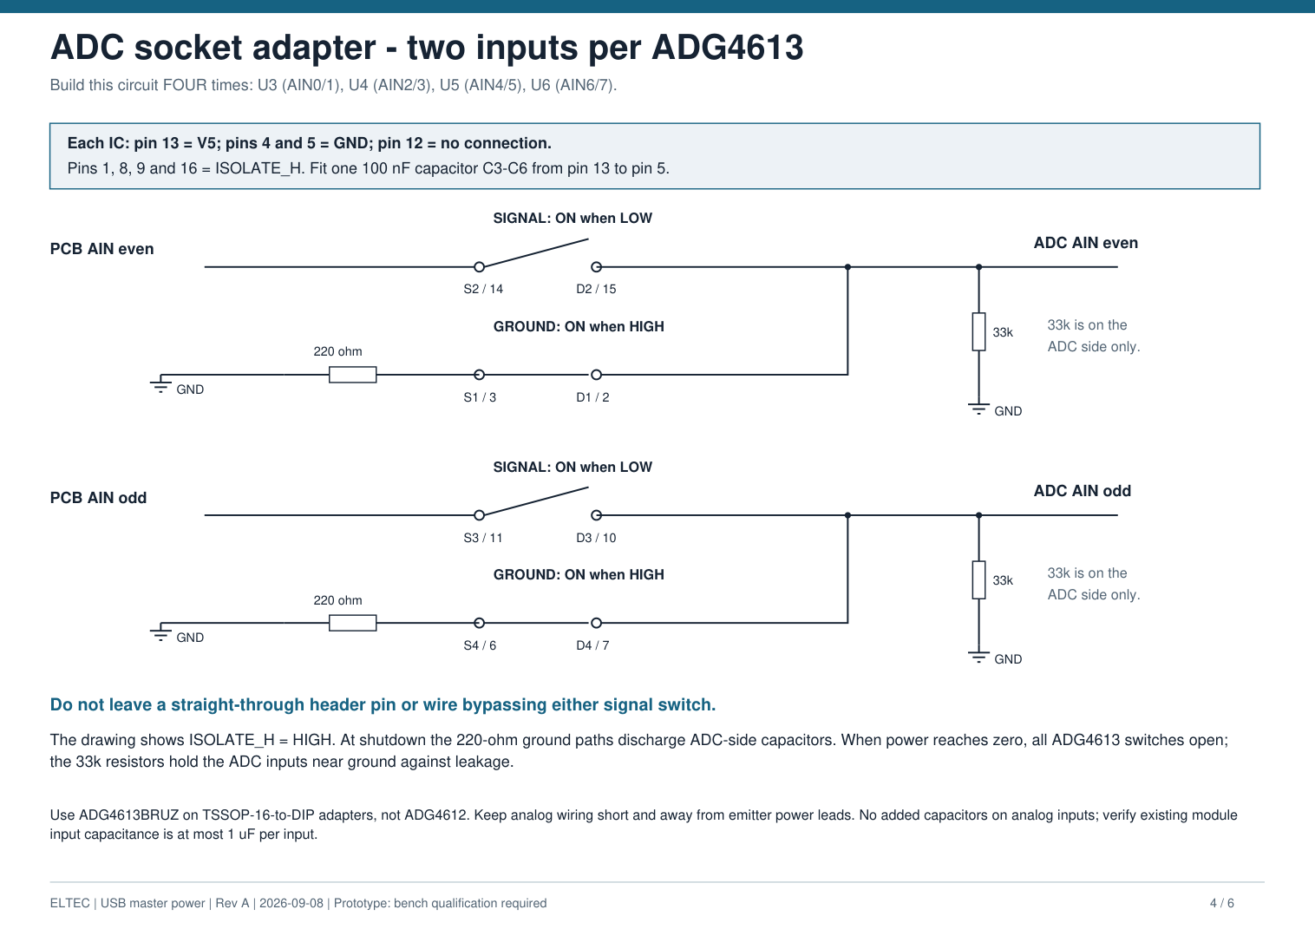
tmp/power_board_schematic/rendered/page-4.png
