JCastel358/Eltec406mca/tmp/power_board_schematic/vo1263-pinout.png

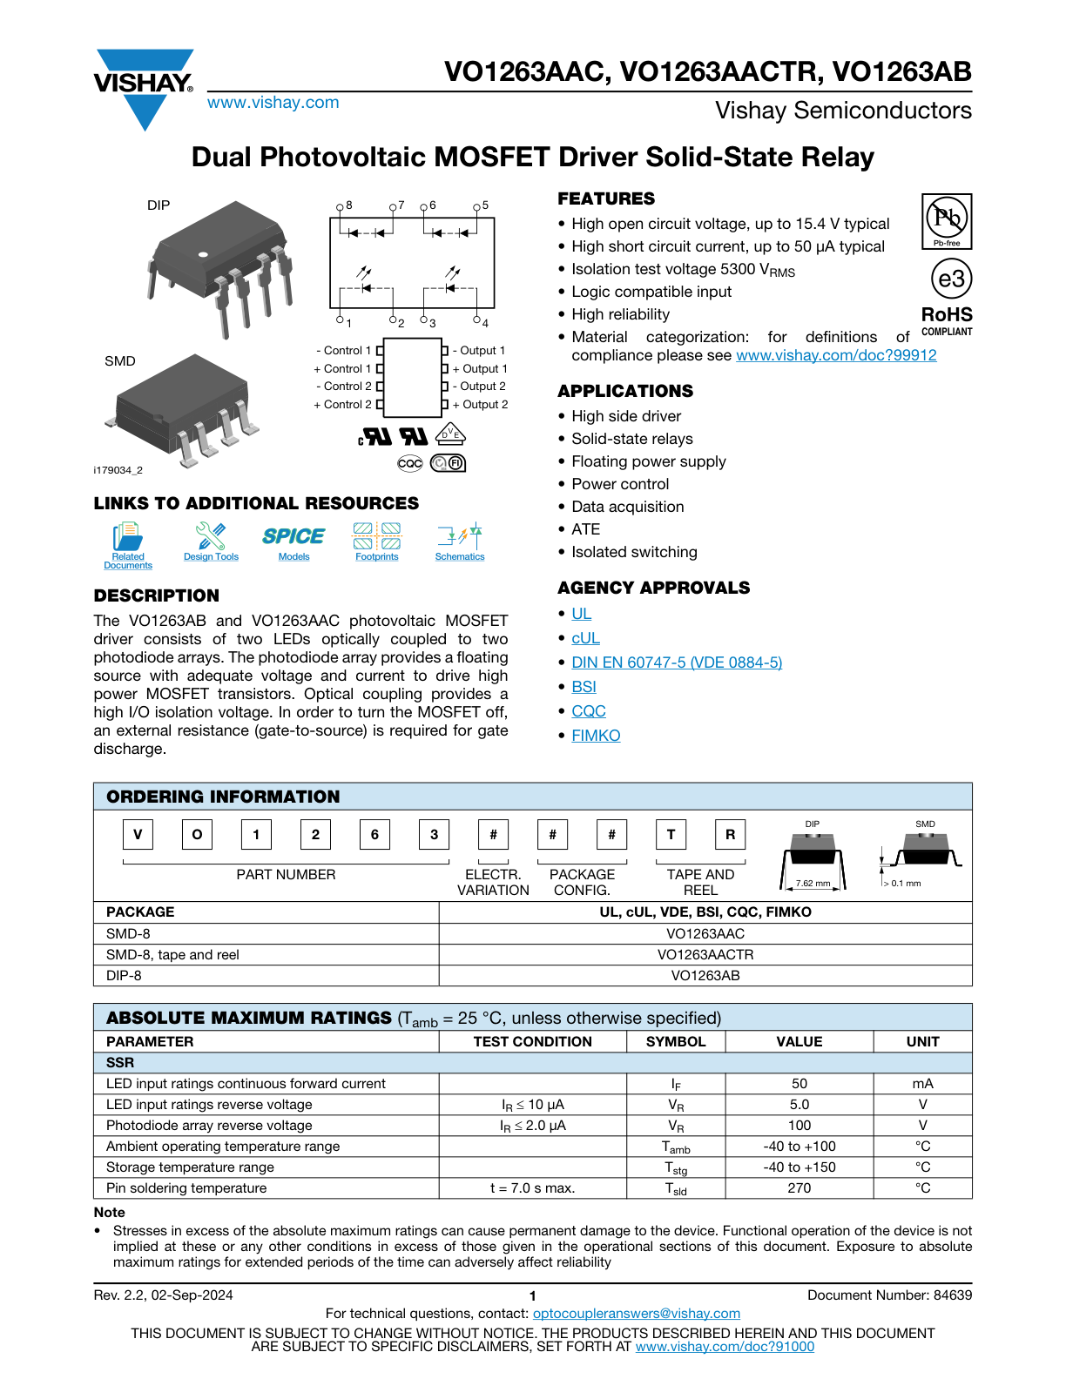
tmp/power_board_schematic/vo1263-pinout.png
