JCastel358/Eltec406mca/hardware/single_detector_usb_master_r1/exports/assembly_draft/README.md

# Draft assembly data — do not order

195 fitted components, including sockets and trimmer. Customer installs only the ESP32, ADS1256 module and two barrel jacks. Detector/emitter wire lands are copper features.

9 references have unresolved sourcing fields; see each entry in assembly_export.json. The engineering BOM and sourcing report identify them. No substitution is authorized.

CPL coordinates are millimeters from the candidate board bottom-left corner; positive X is right, positive Y is up, rotation is counterclockwise. THT connector/trimmer body-center offsets are explicit in assembly_export.json. Every vendor library rotation, allocation and assembly process still needs review.

Generated from the native KiCad PCB; BOM/CPL/native fitted reference sets and native origins agree. Native routing checks are recorded separately in board_validation.json. Mechanical fit, electrical qualification and release remain separate gates.

[JLC BOM/CPL guidance](https://jlcpcb.com/help/article/how-to-generate-the-bom-and-centroid-file-from-kicad), [placement format](https://jlcpcb.com/help/article/pick-place-file-for-pcb-assembly).
