JCastel358/Eltec406mca/hardware/single_detector_usb_master_r1/exports/board_review/trial01_copper_b/rendered_pages/assembly_top-1.png

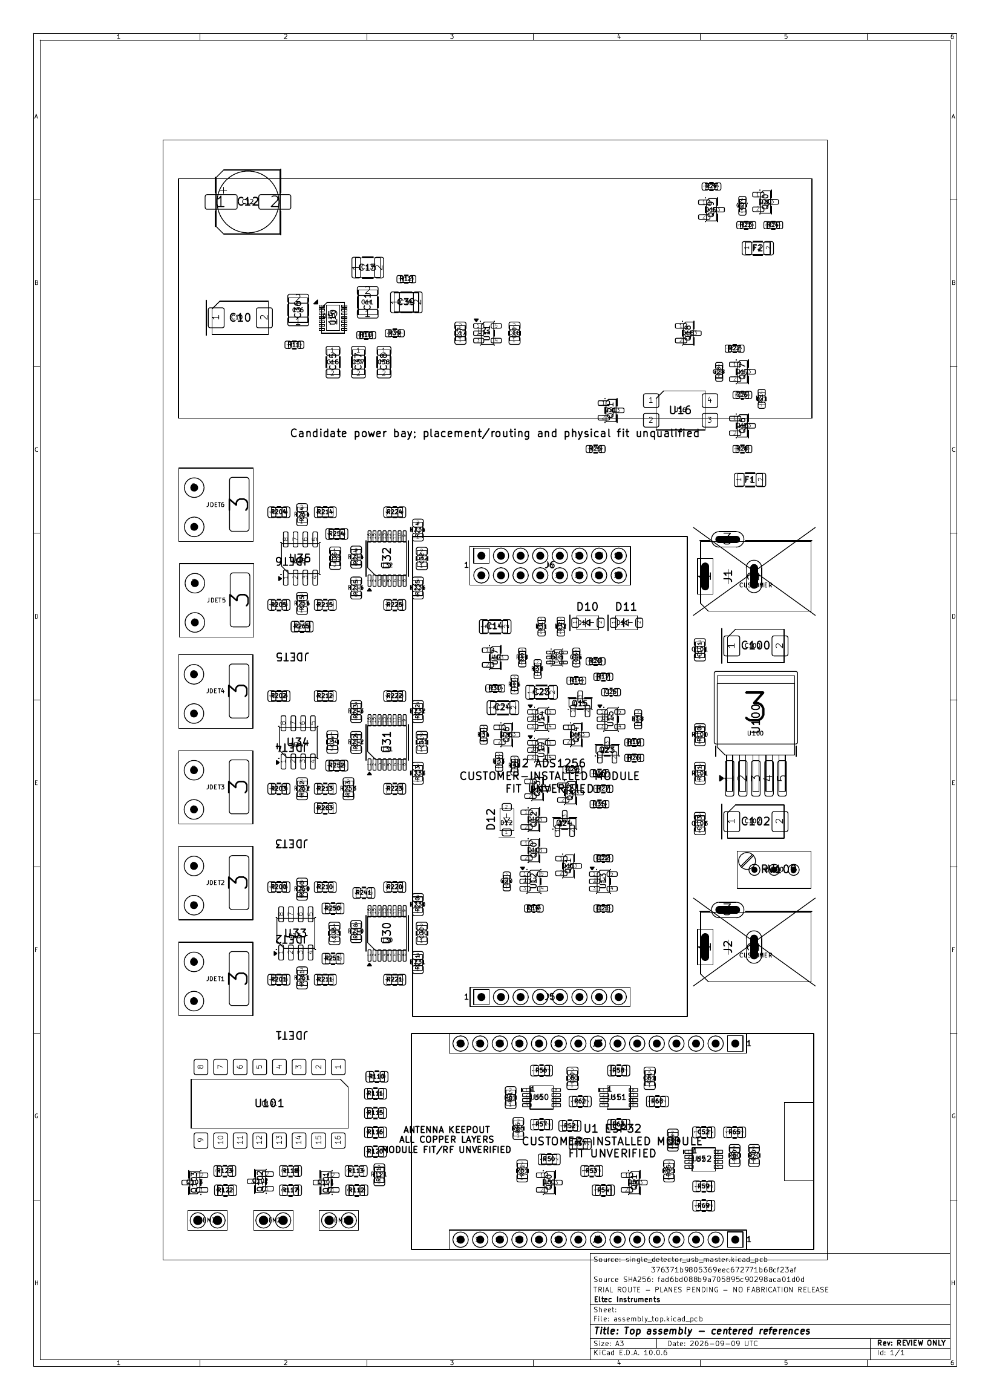
hardware/single_detector_usb_master_r1/exports/board_review/trial01_copper_b/rendered_pages/assembly_top-1.png
