JCastel358/Eltec406mca/hardware/single_detector_usb_master_r1/reports/amp_signal_debug.png

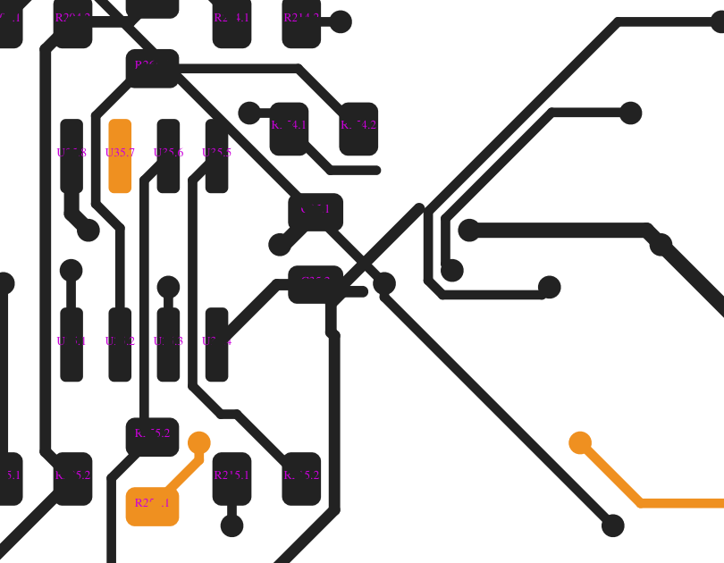
hardware/single_detector_usb_master_r1/reports/amp_signal_debug.png
