JCastel358/Eltec406mca/hardware/single_detector_usb_master_r1/exports/board_review/final_candidate/copper_layers.pdf

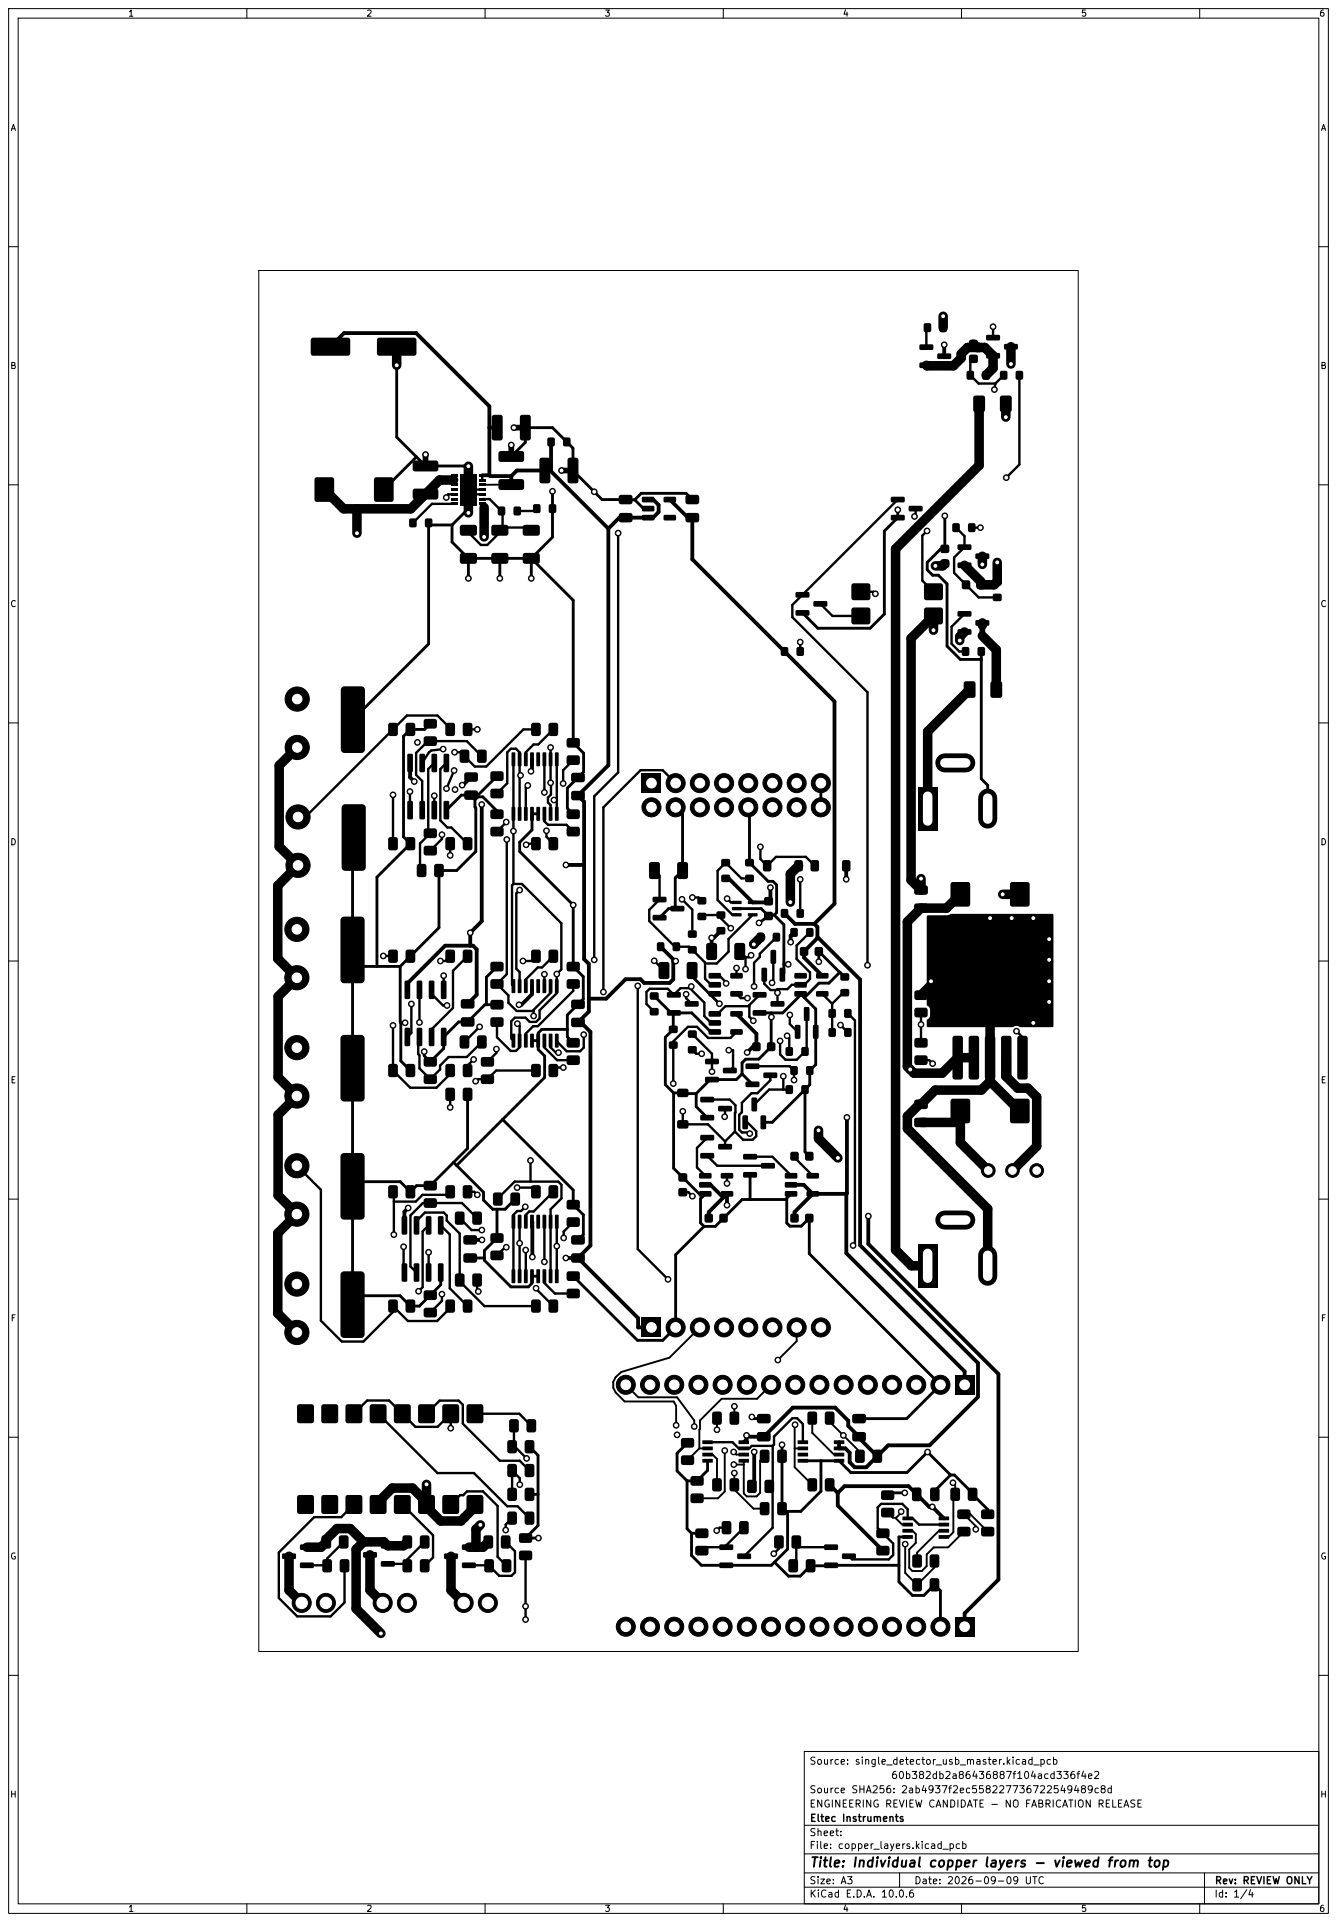
[picture p119: page 1]

Source SHA256: 2ab4937f2ec558227736722549489c8d
ENGINEERING REVIEW CANDIDATE - NO FABRICATION RELEASE
Eltec Instruments
Sheet:
File: copper_layers.kicad_pcb
Title: Individual copper layers - viewed from top

Size: A3 | Rev: REVIEW ONLY
KiCad E.D.A. 10.0.6 | Id: 1/4

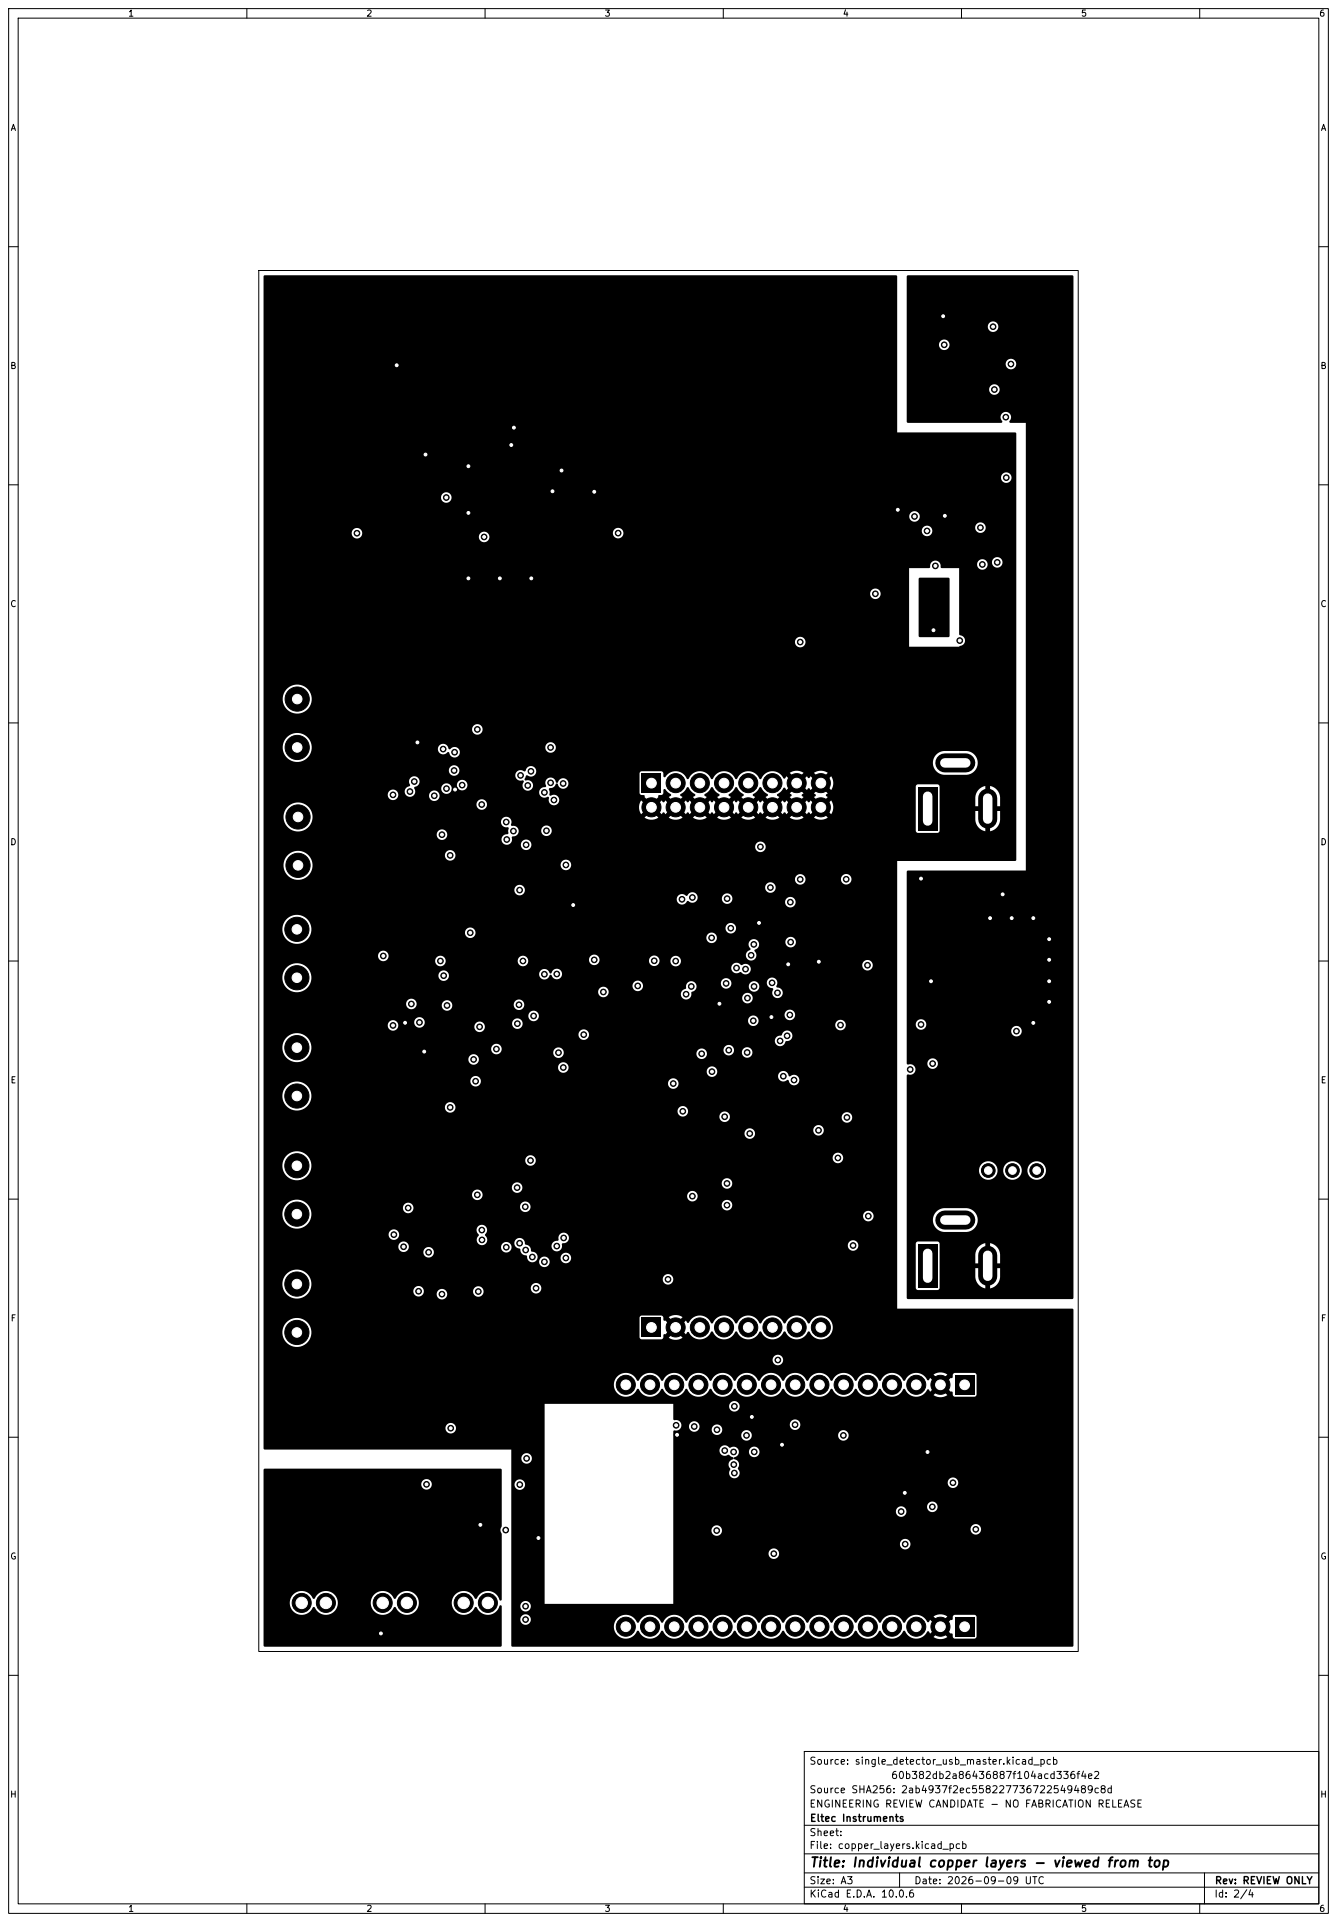
[picture p120: page 2]

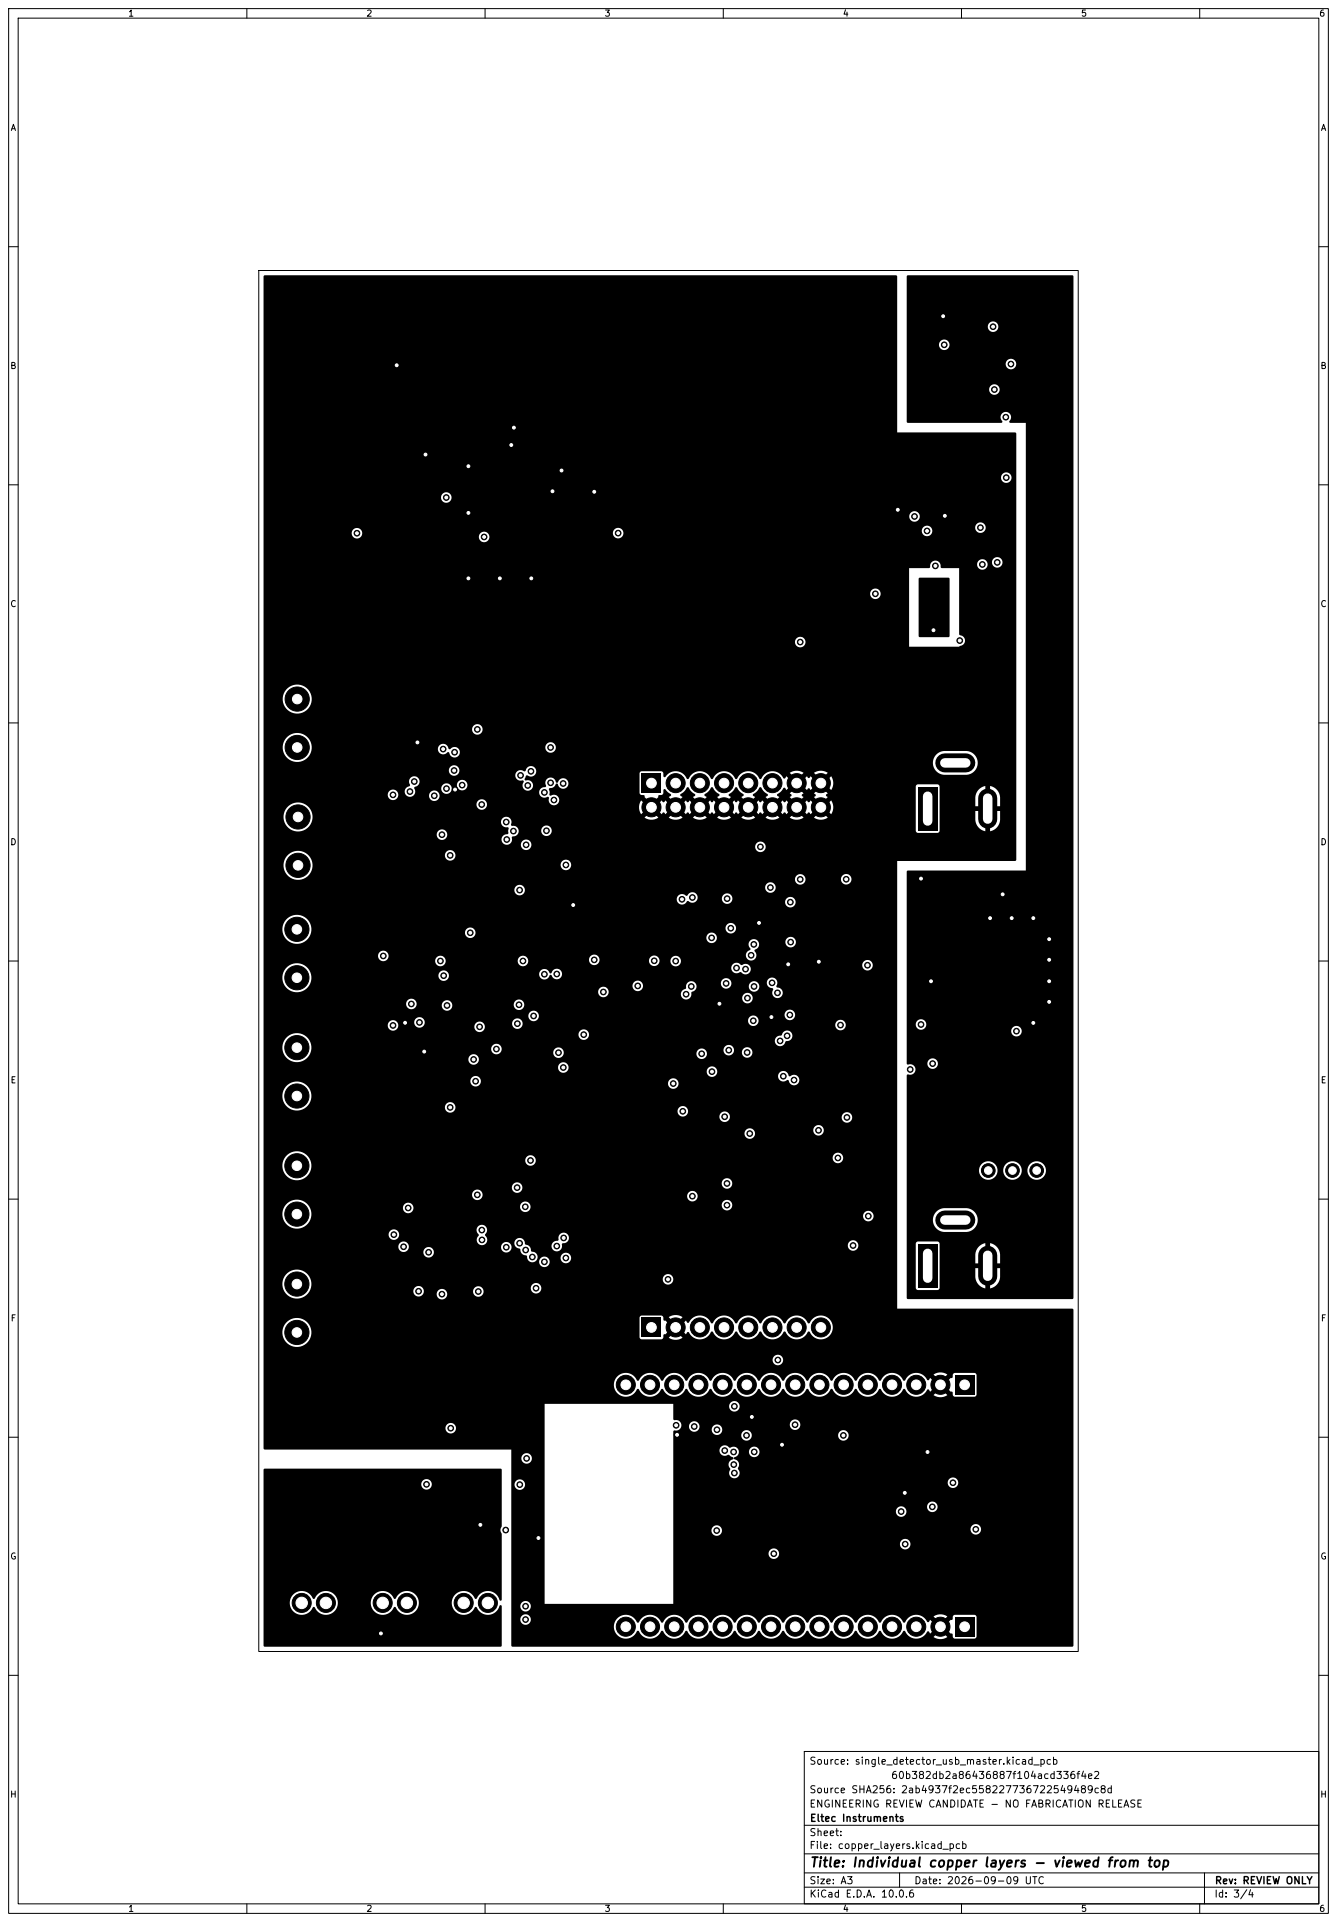
[picture p121: page 3]

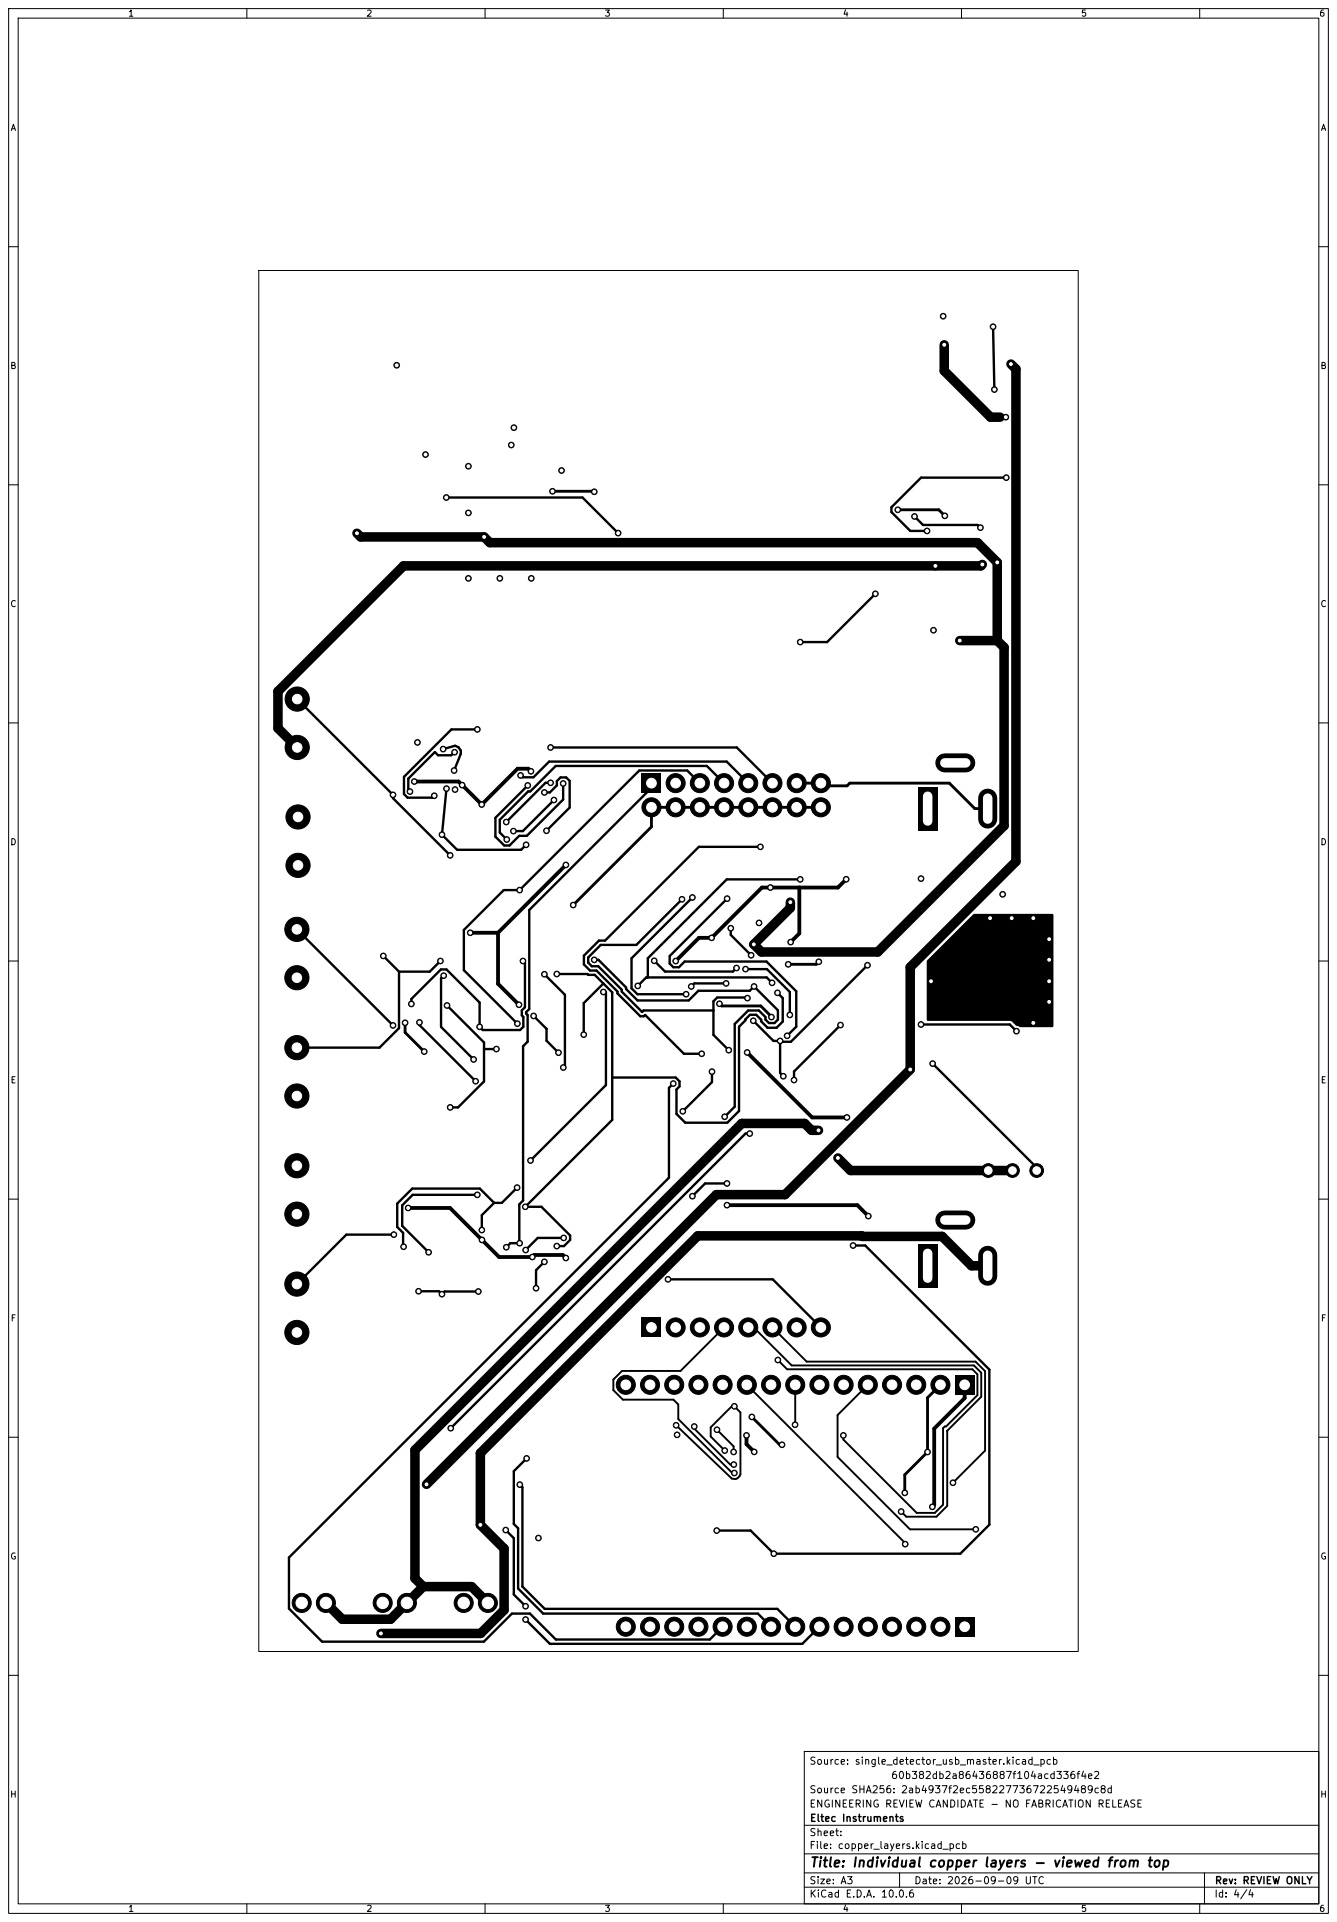
[picture p122: page 4]
