JCastel358/Eltec406mca/hardware/single_detector_usb_master_r1/exports/board_review/final_candidate/copper_top.pdf

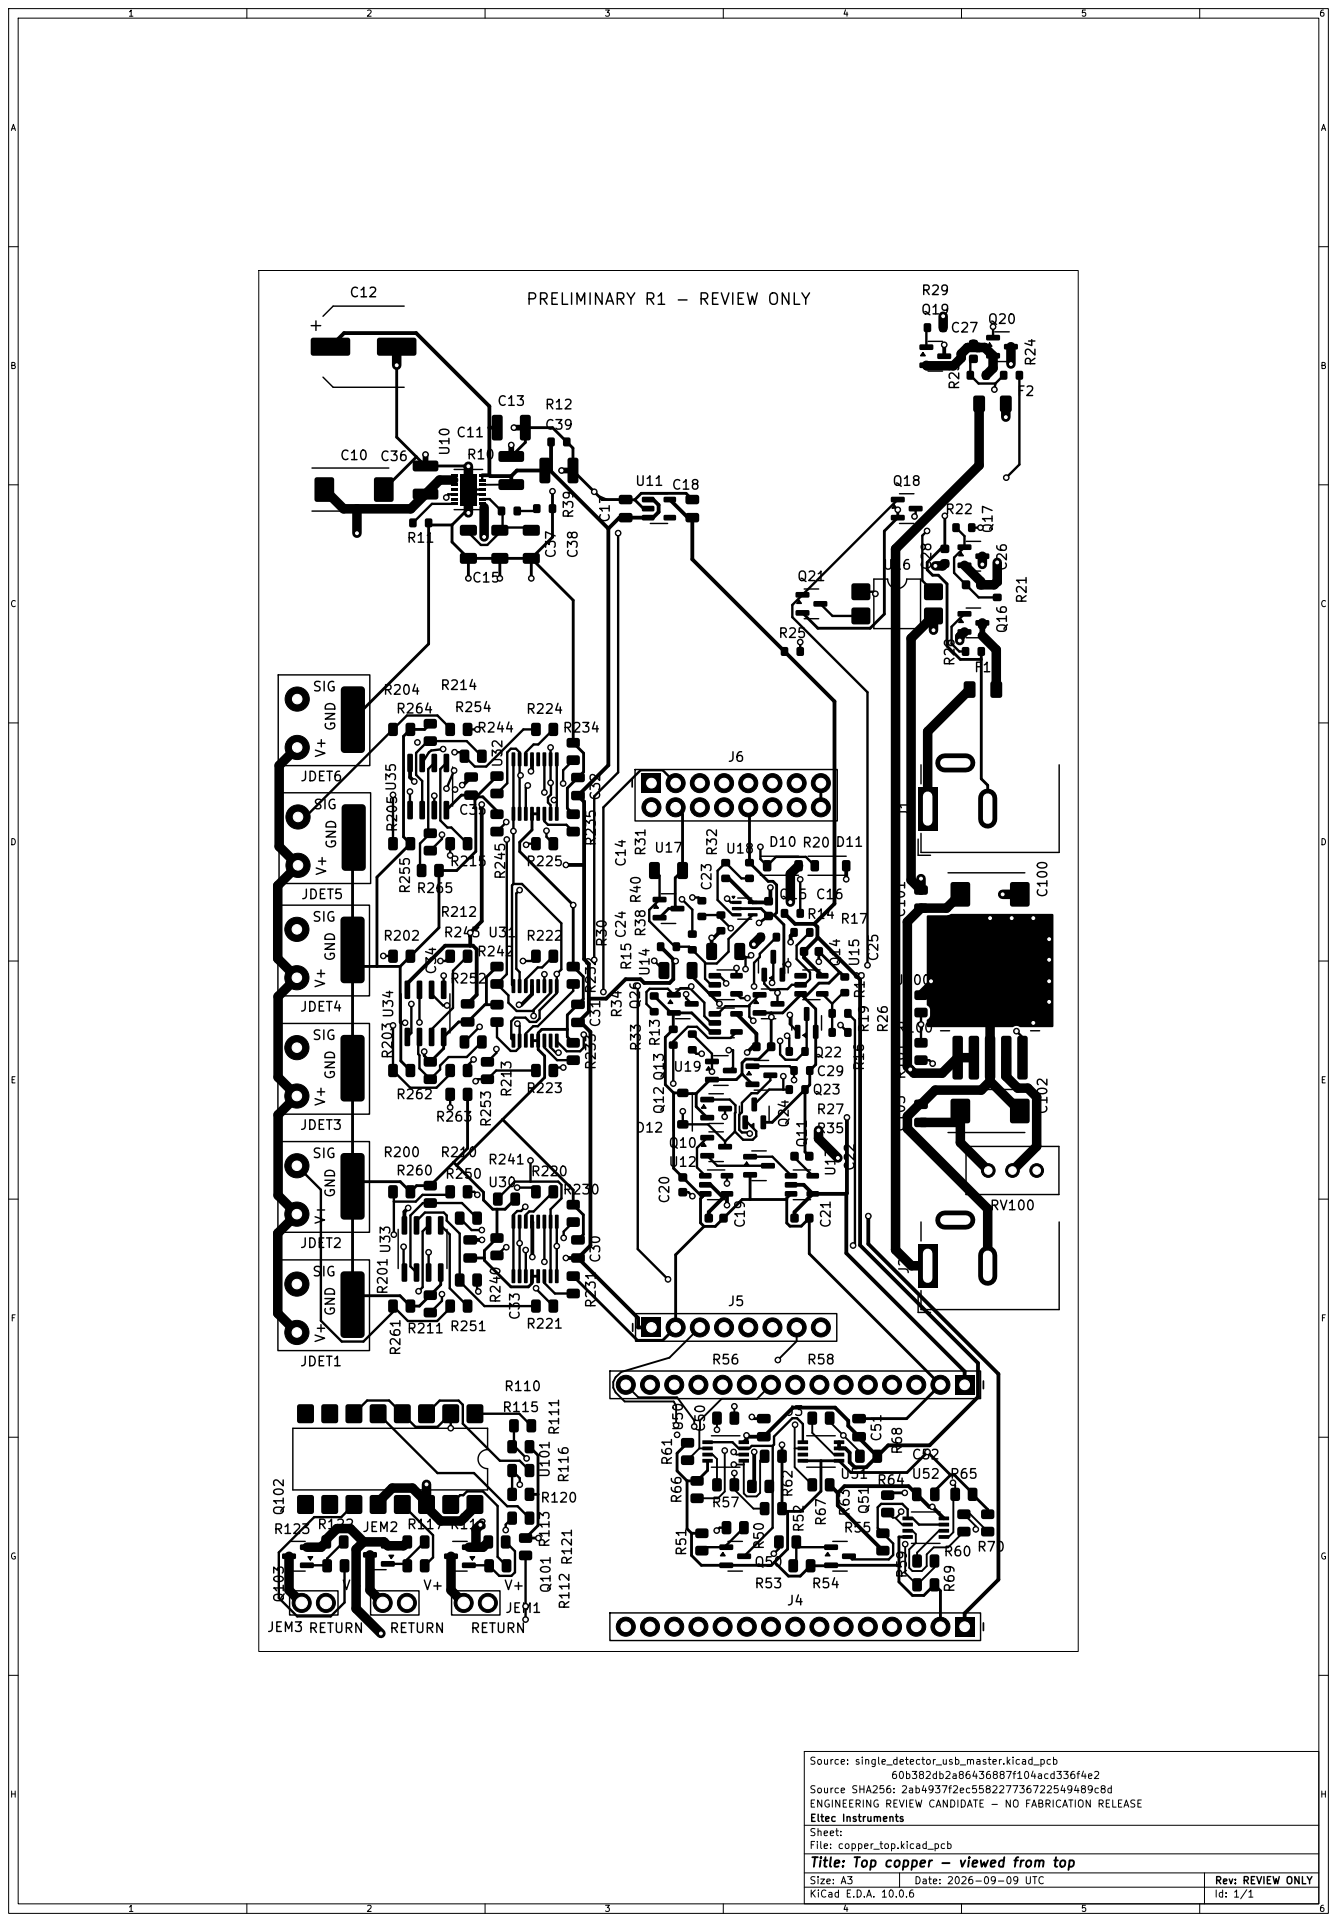
[picture p123: page 1]

Source SHA256: 2ab4937f2ec558227736722549489c8d
ENGINEERING REVIEW CANDIDATE - NO FABRICATION RELEASE
Eltec Instruments
Sheet:
File: copper_top.kicad_pcb
Title: Top copper - viewed from top

Size: A3 | Rev: REVIEW ONLY
KiCad E.D.A. 10.0.6 | Id: 1/1
