JCastel358/Eltec406mca/hardware/single_detector_usb_master_r1/exports/board_review/final_routed_review/copper_layers.pdf

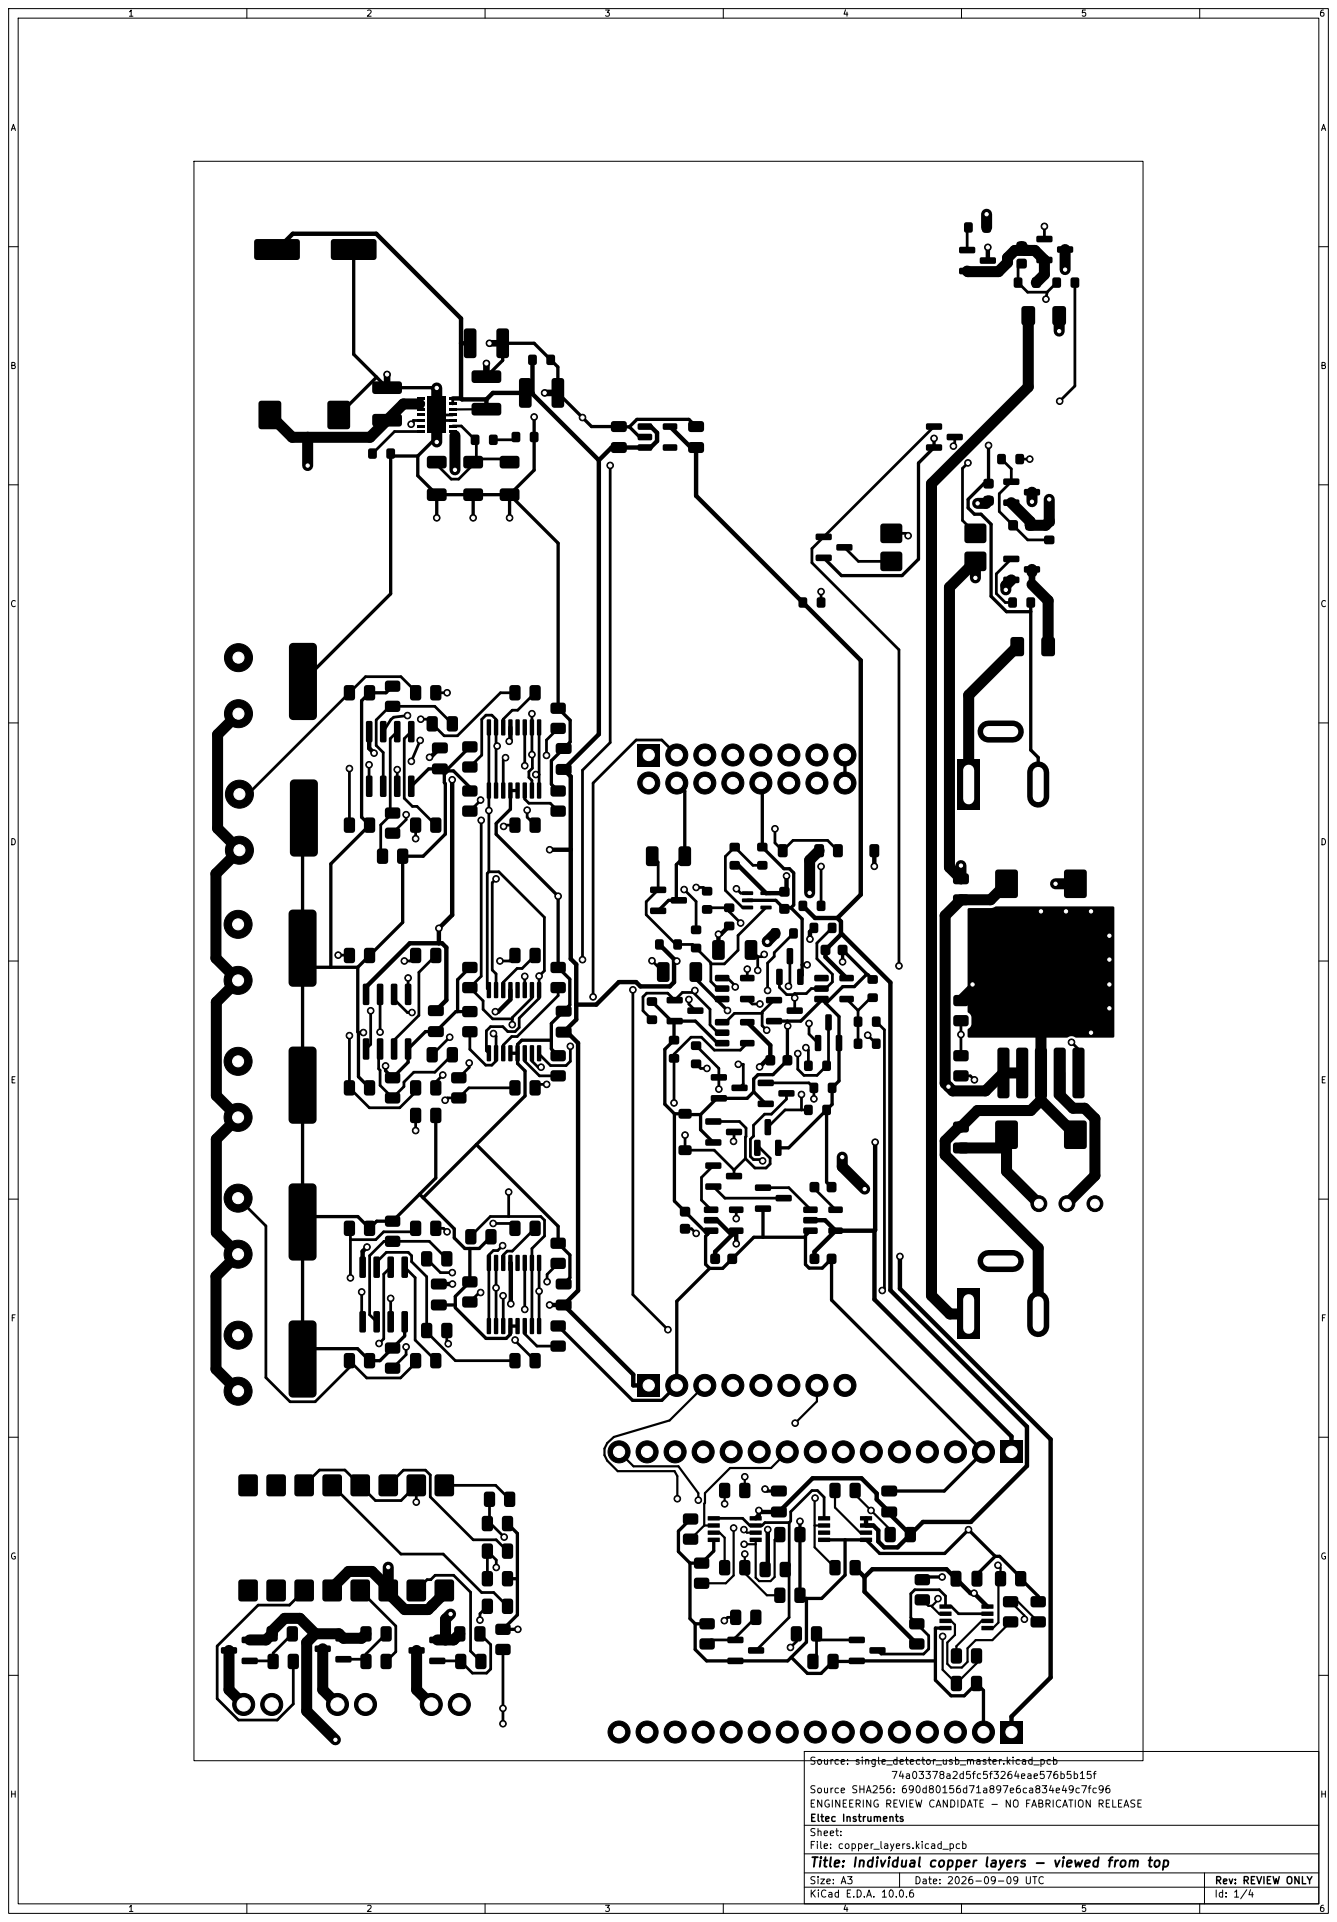
[picture p124: page 1]

Source SHA256: 690d80156d71a897e6ca834e49c7fc96
ENGINEERING REVIEW CANDIDATE - NO FABRICATION RELEASE
Eltec Instruments
Sheet:
File: copper_layers.kicad_pcb
Title: Individual copper layers - viewed from top

Size: A3 | Rev: REVIEW ONLY
KiCad E.D.A. 10.0.6 | Id: 1/4

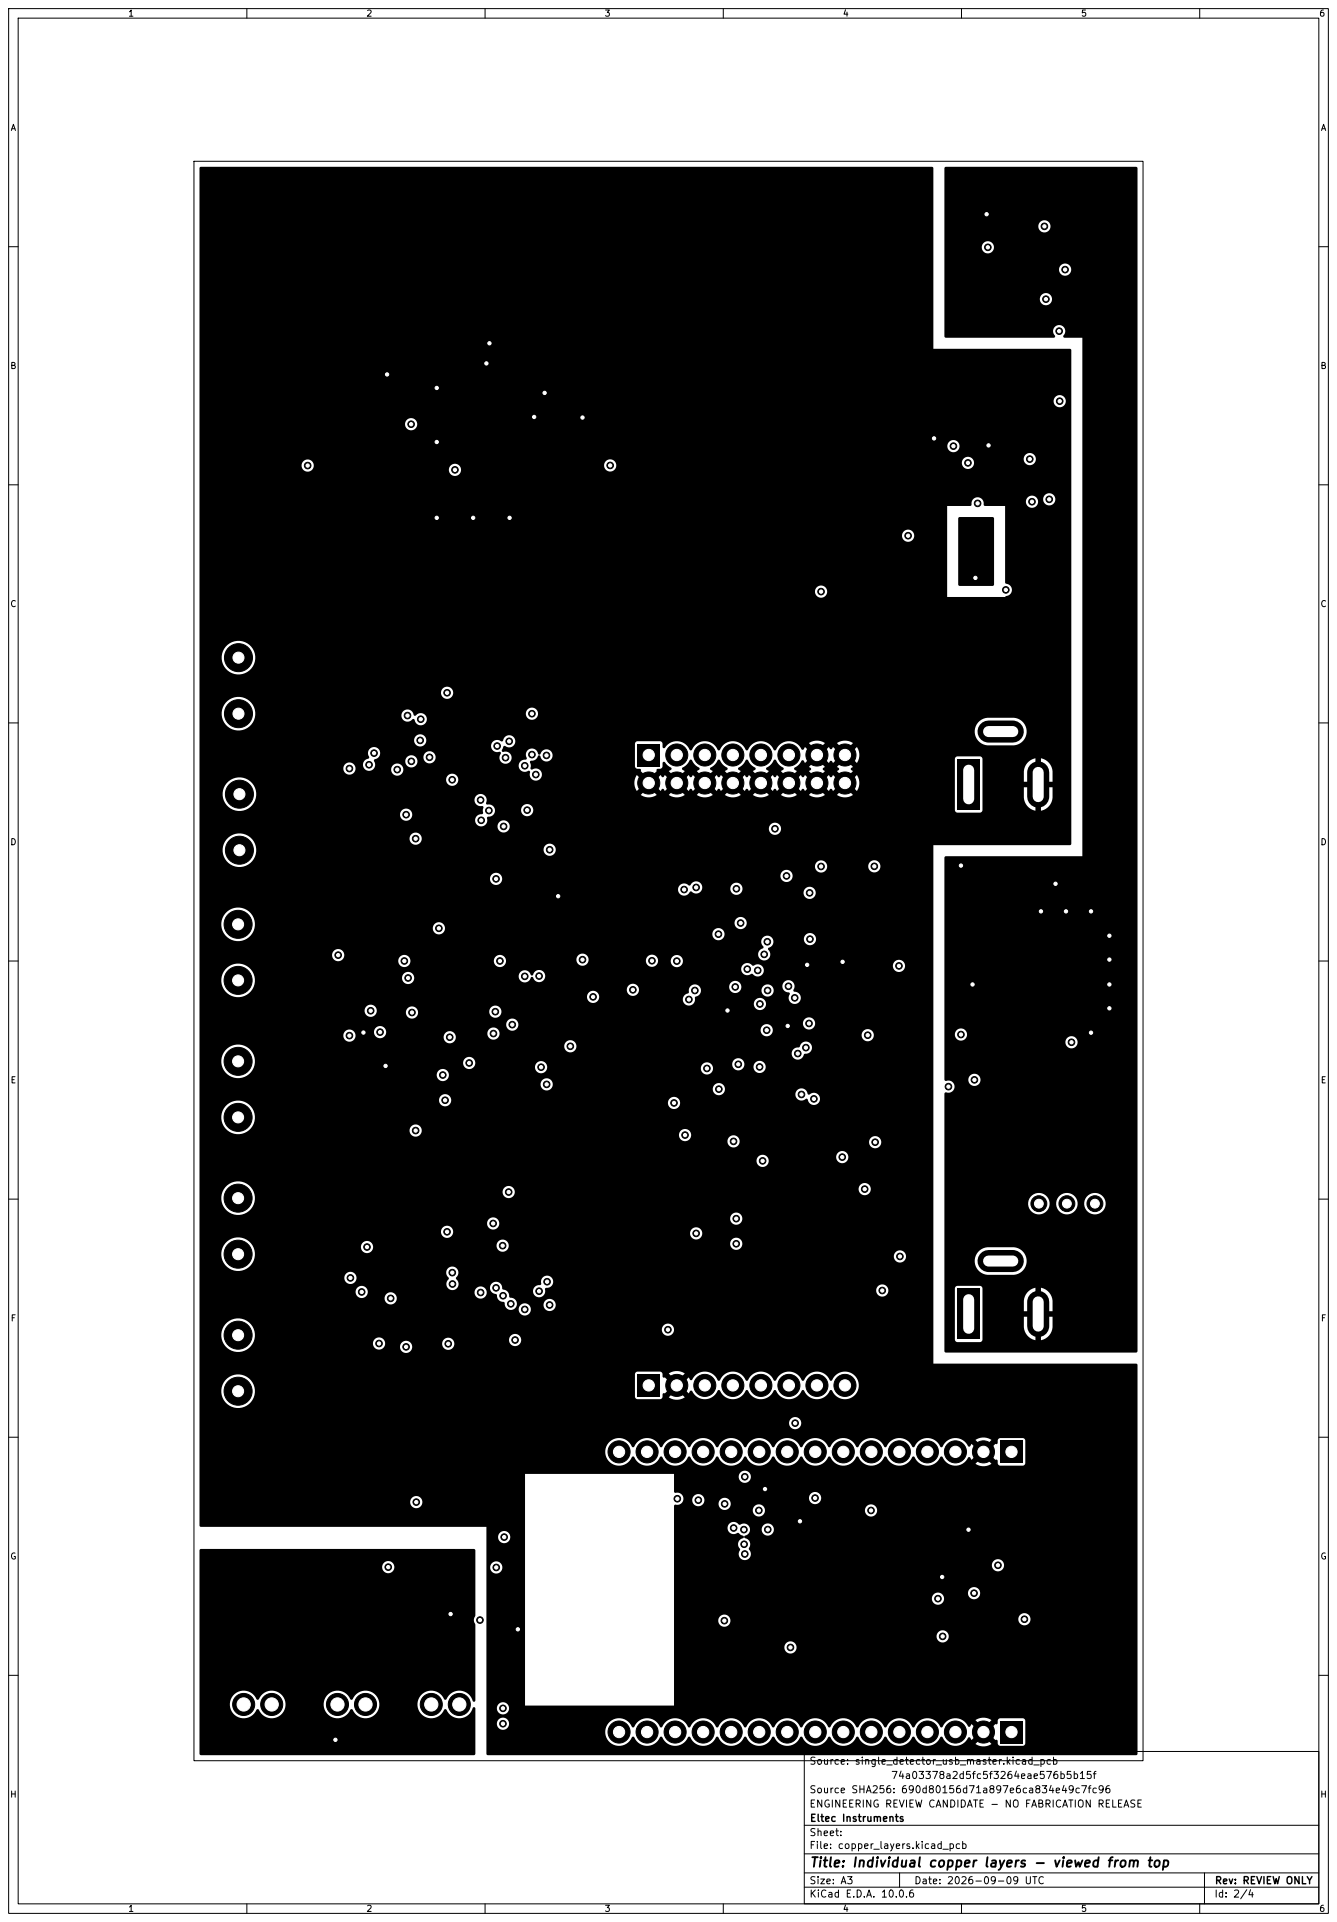
[picture p125: page 2]

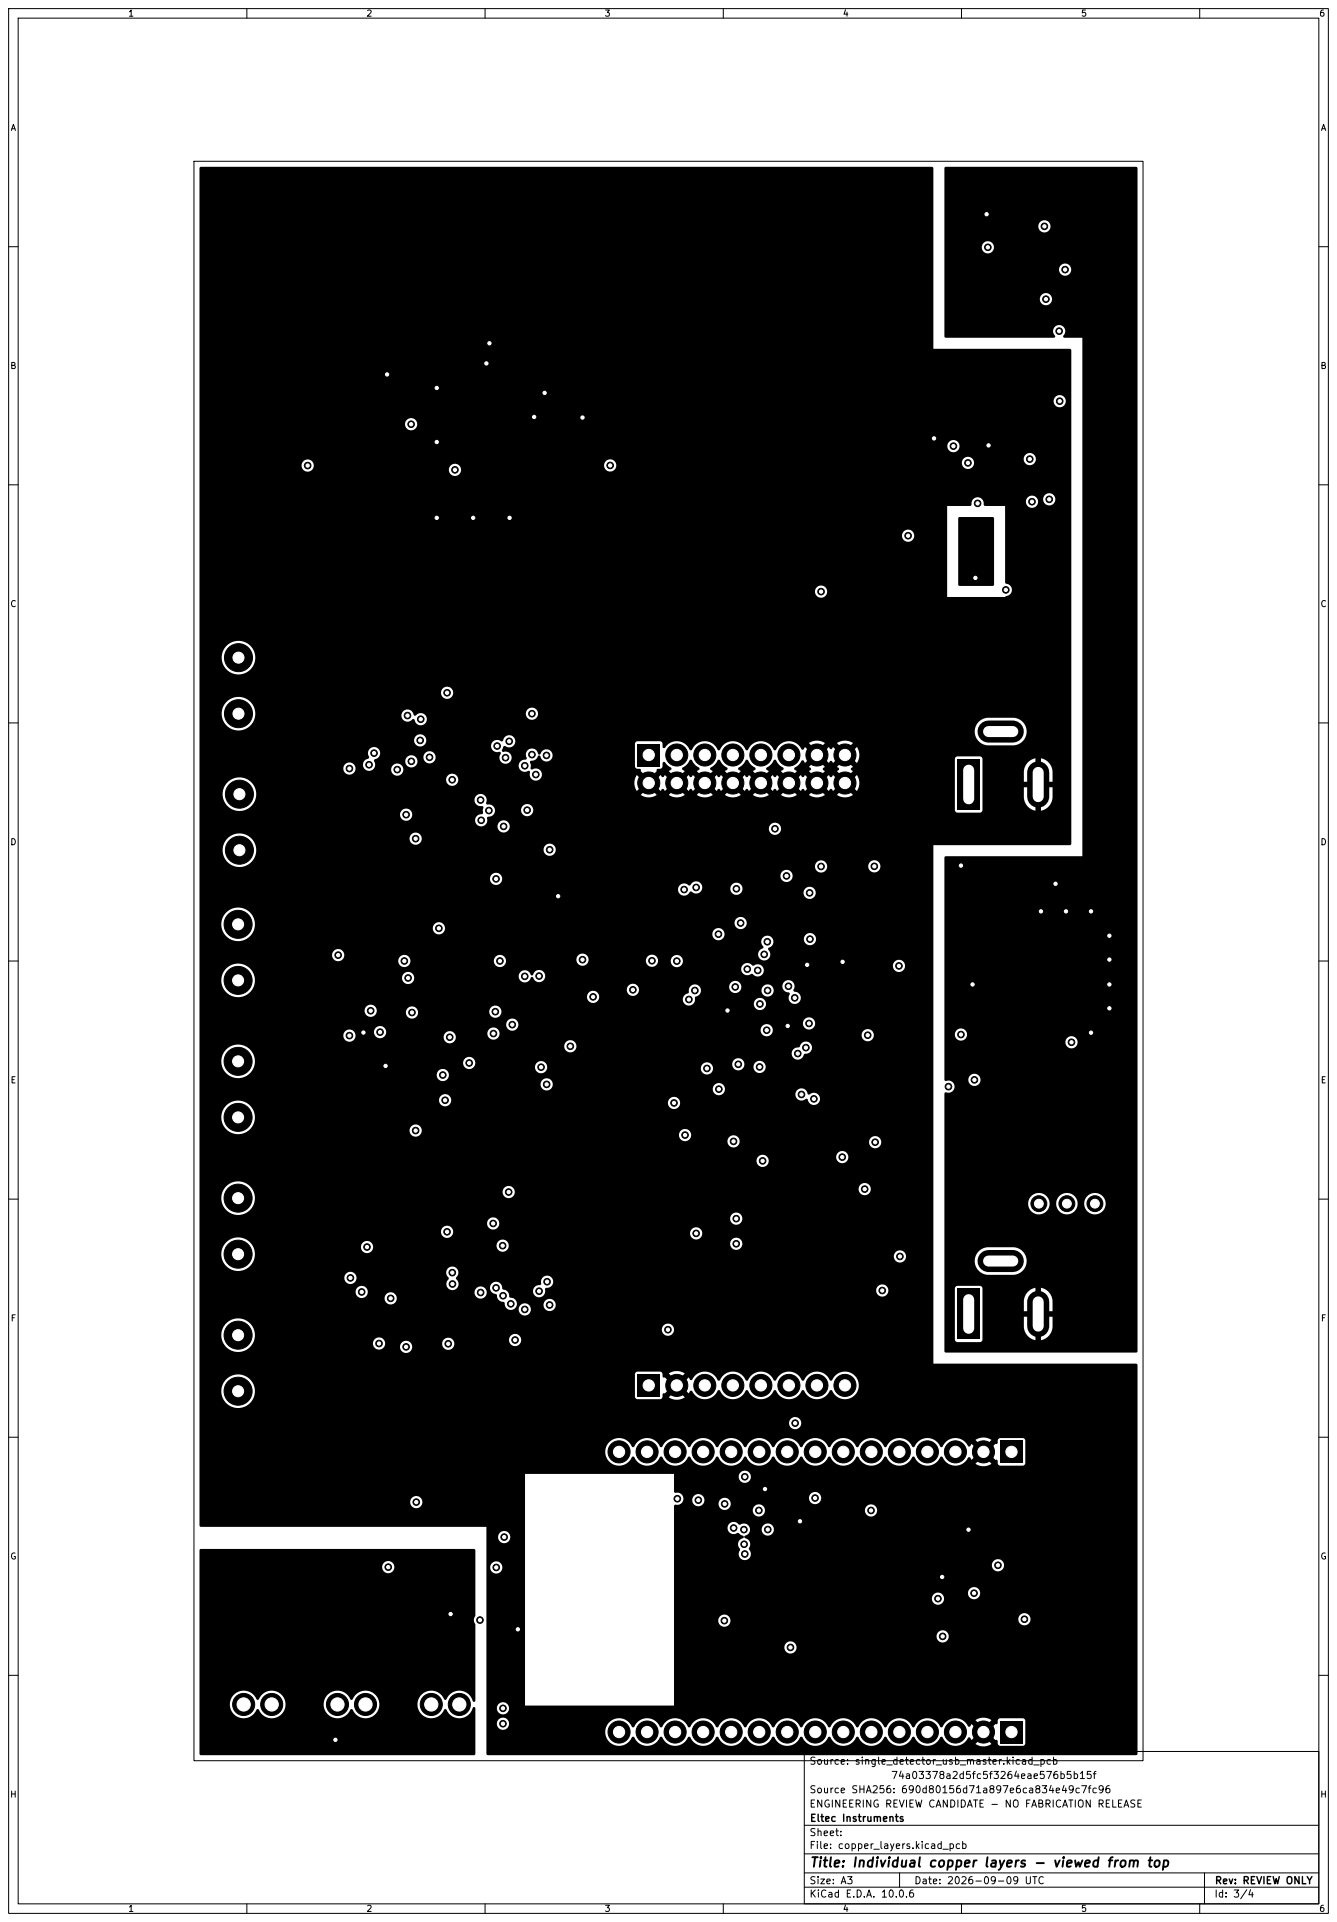
[picture p126: page 3]

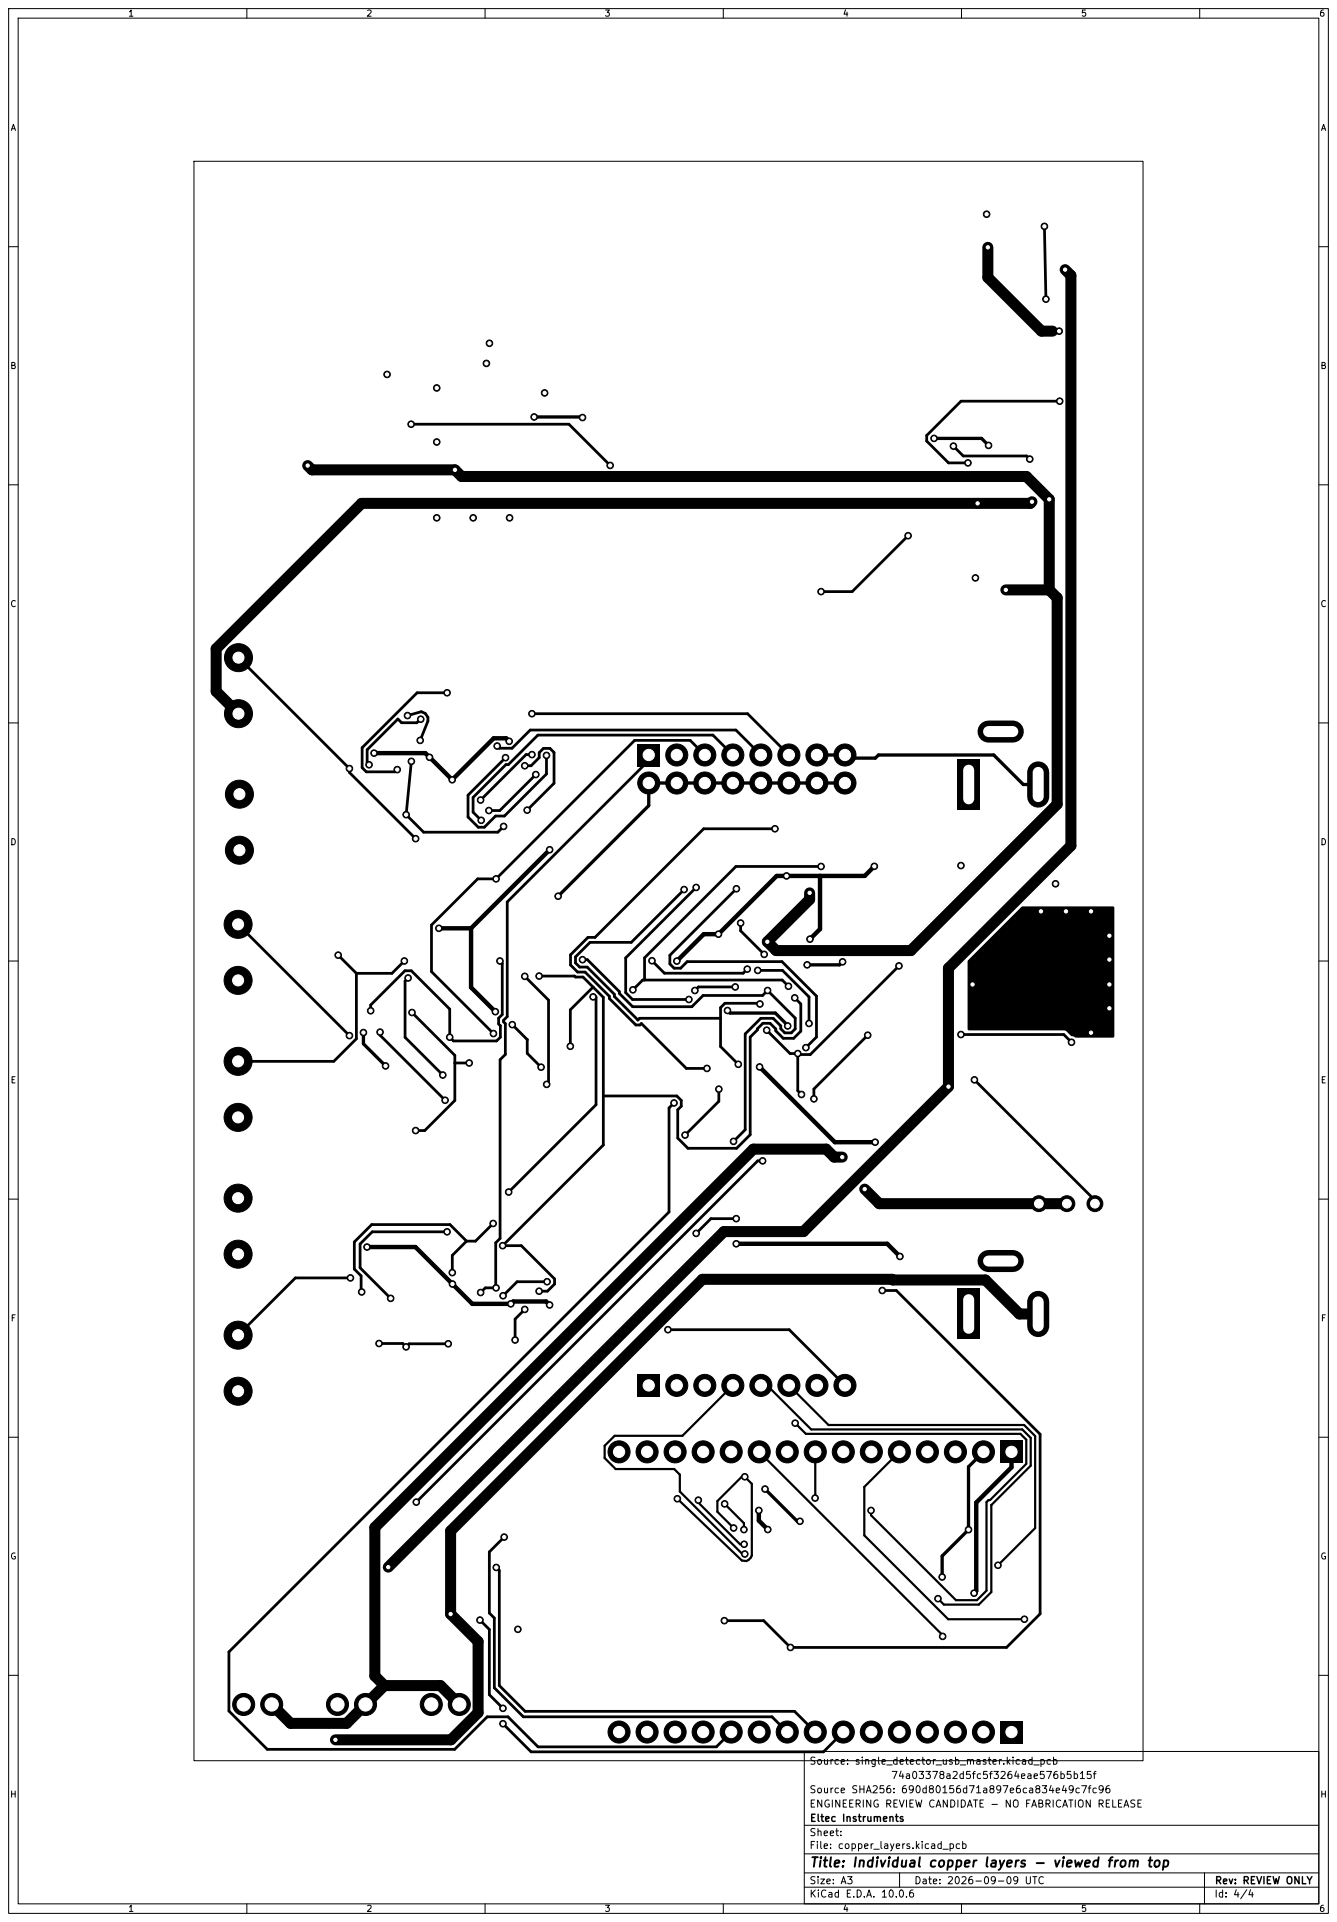
[picture p127: page 4]
