JCastel358/Eltec406mca/hardware/single_detector_usb_master_r1/exports/board_review/trial01_copper_b/assembly_top.pdf

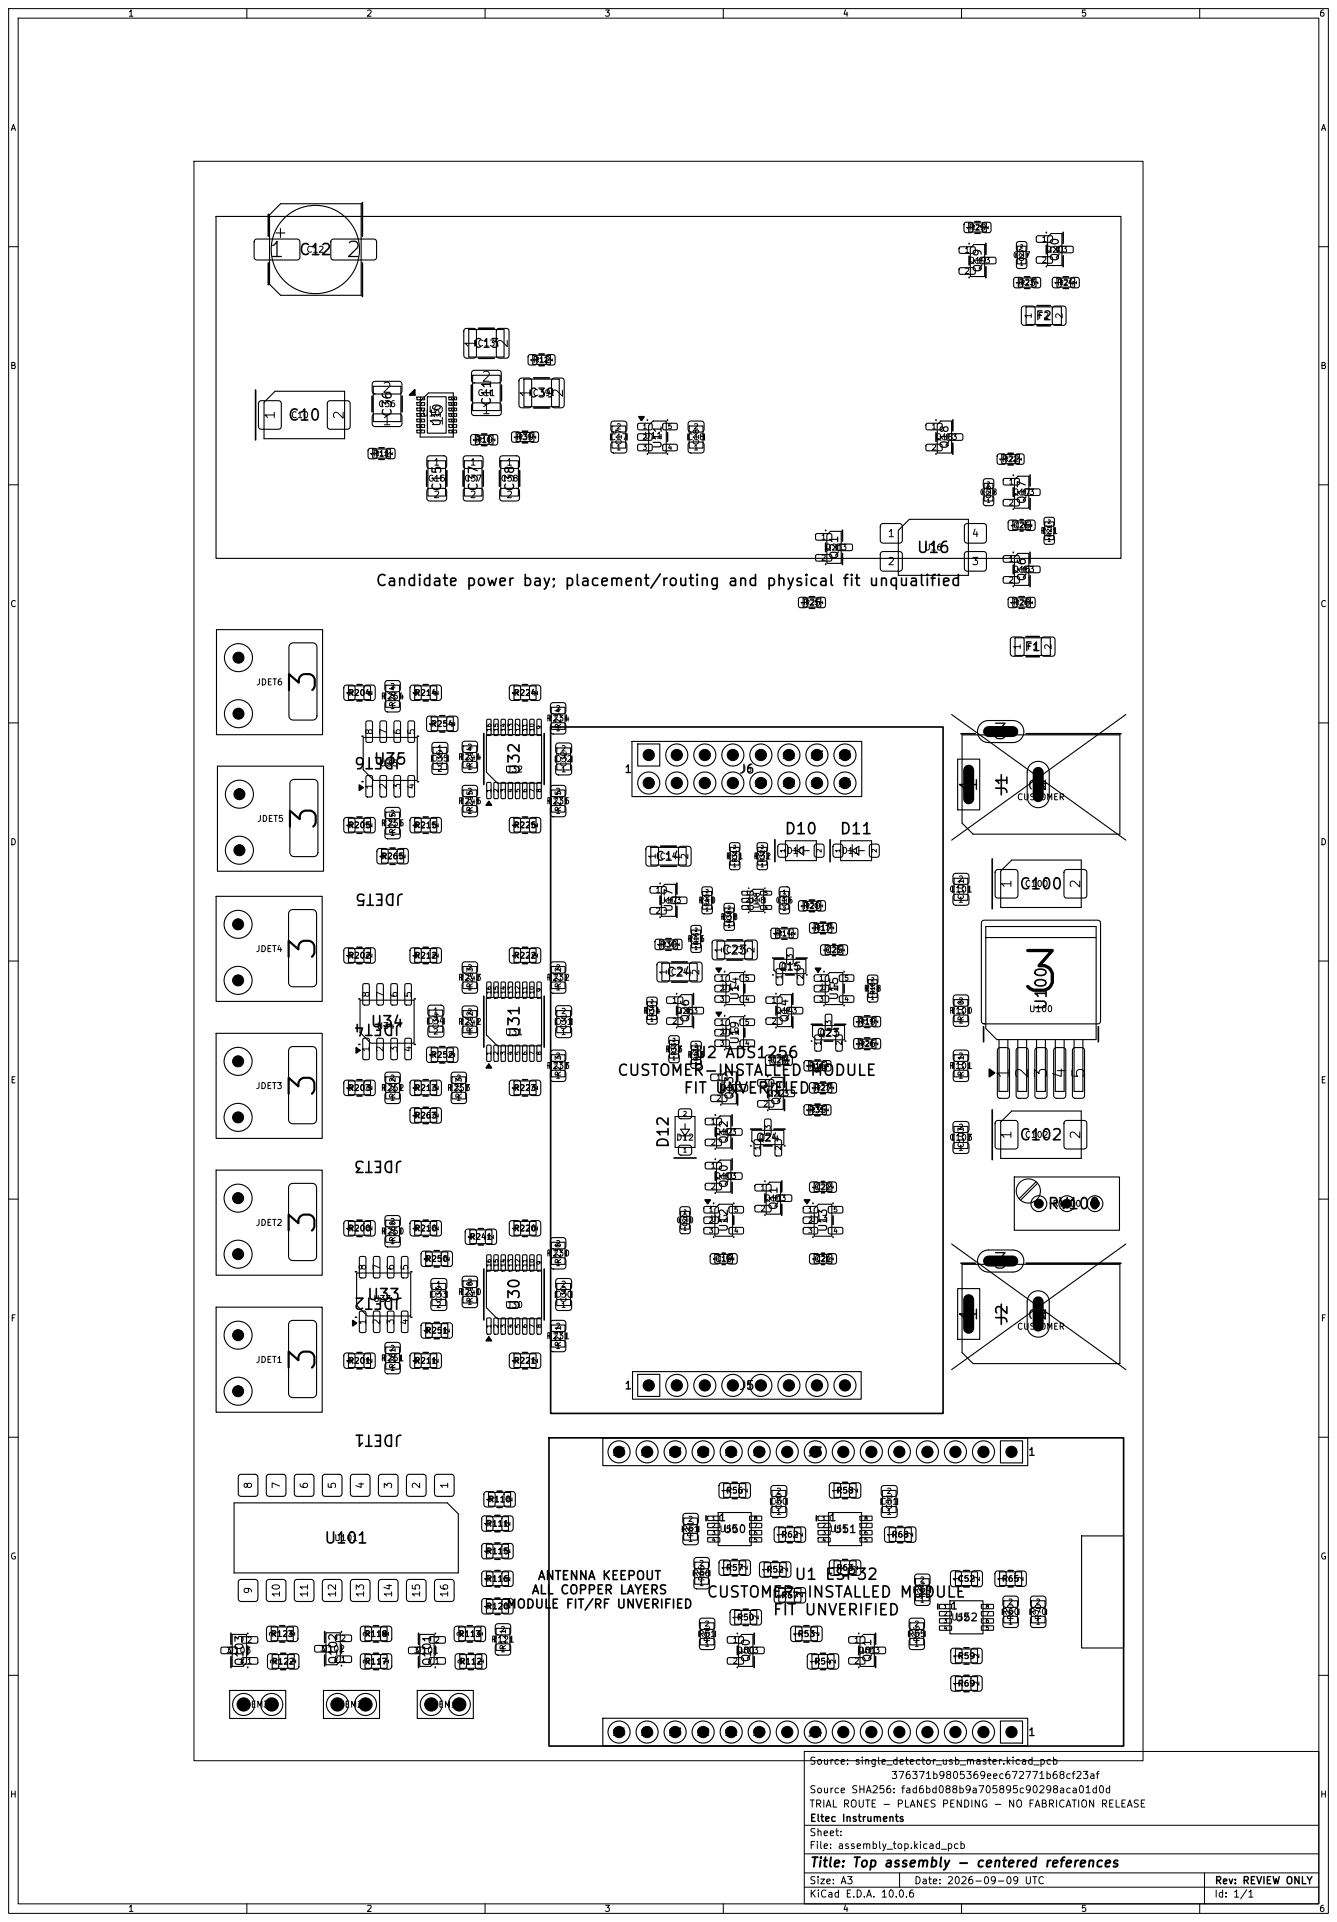
[picture p132: page 1]

Candidate power bay; placement/routing and physical fit unqualified

MODULE FIT/RF UNVERIFIED

Source SHA256: fad6bd088b9a705895c90298aca01d0d
TRIAL ROUTE - PLANES PENDING - NO FABRICATION RELEASE
Eltec Instruments
Sheet:
File: assembly_top.kicad_pcb
Title: Top assembly - centered references

Size: A3 | Rev: REVIEW ONLY
KiCad E.D.A. 10.0.6 | Id: 1/1
