JCastel358/Eltec406mca/hardware/single_detector_usb_master_r1/exports/board_review/trial01_copper_b/copper_layers.pdf

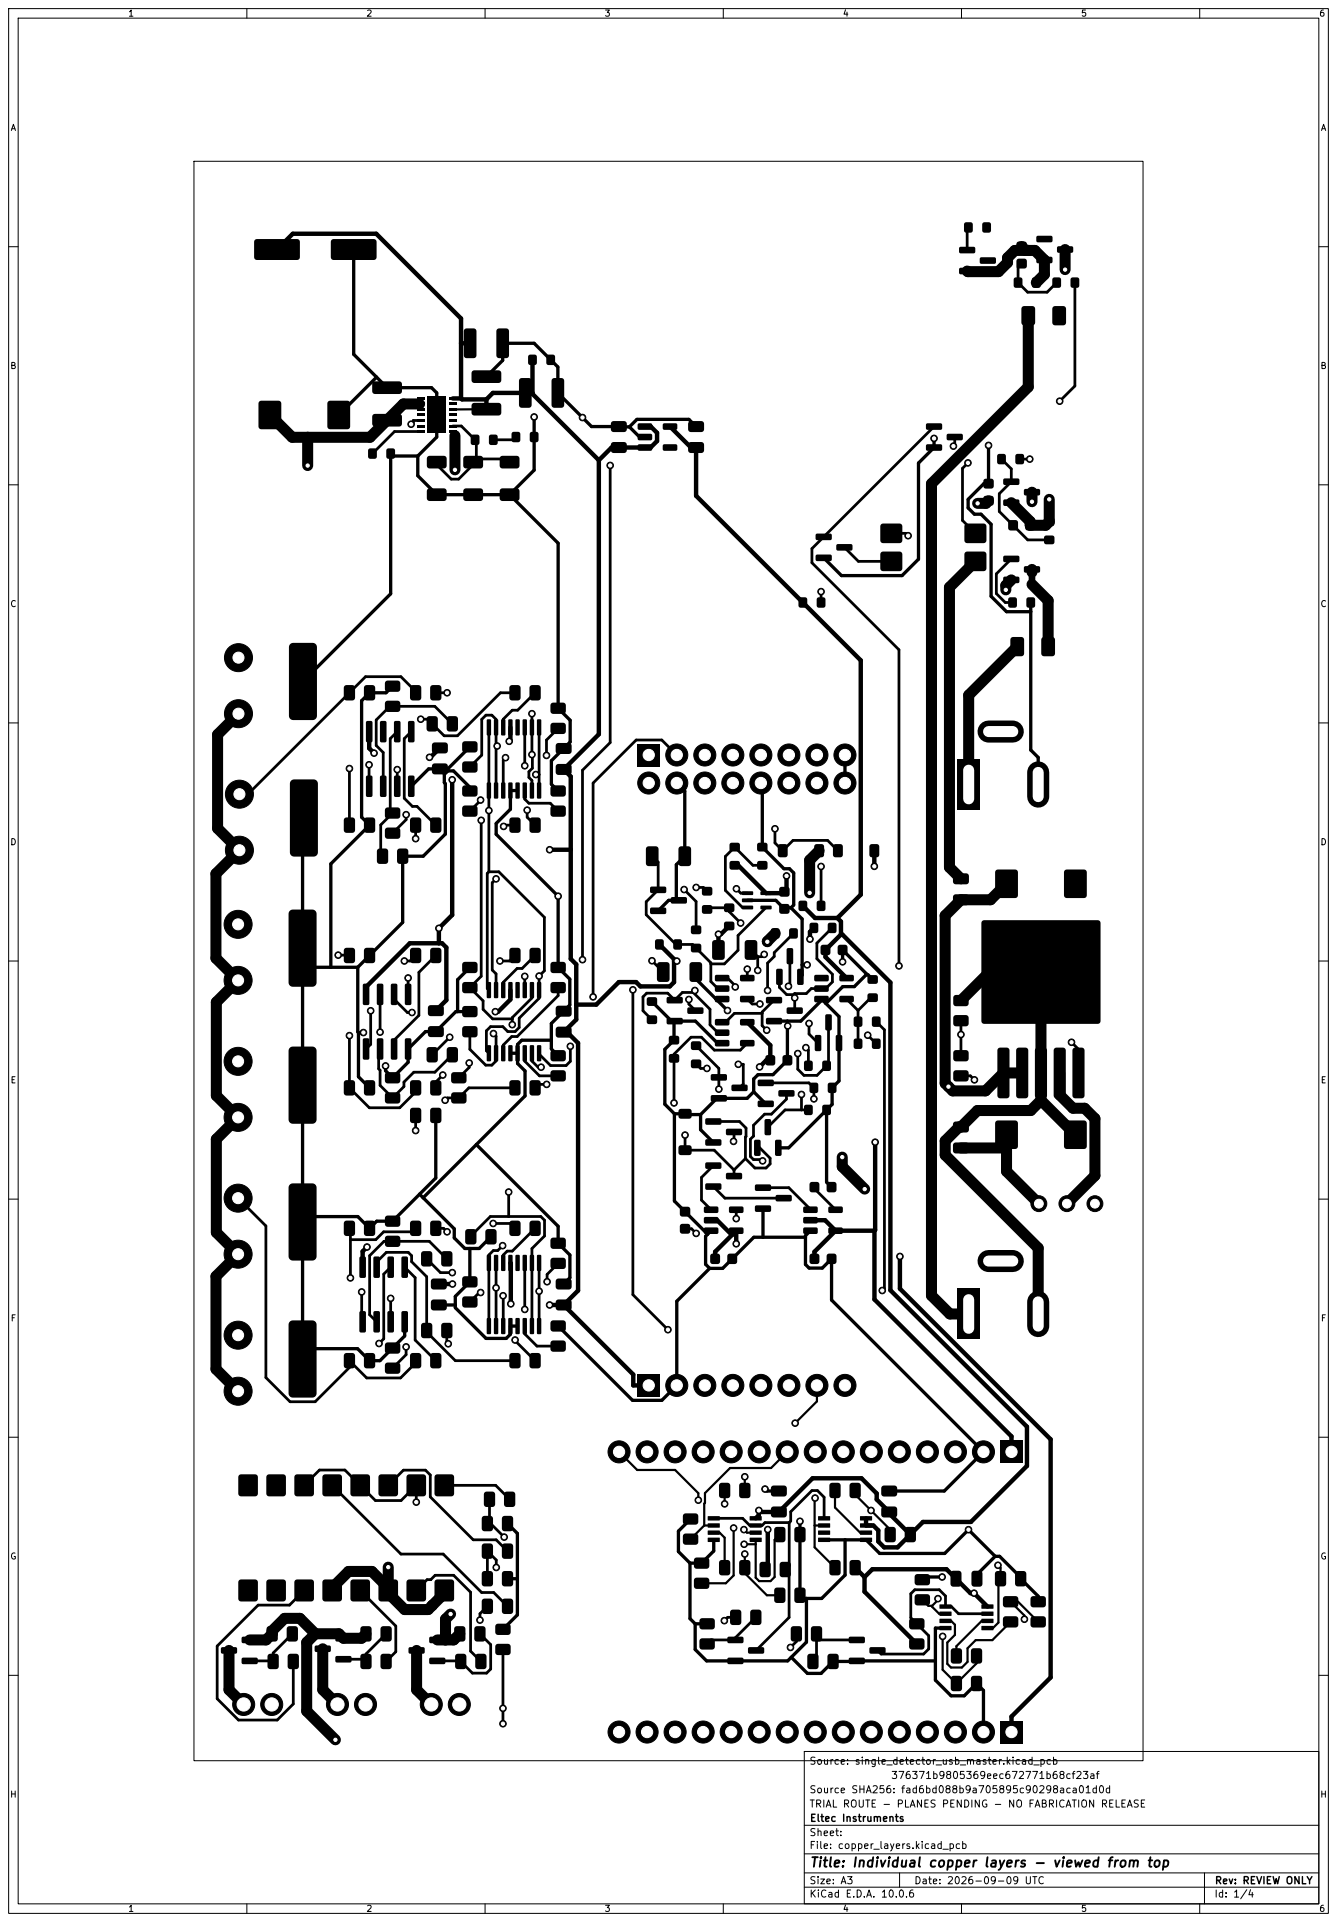
[picture p133: page 1]

Source SHA256: fad6bd088b9a705895c90298aca01d0d
TRIAL ROUTE - PLANES PENDING - NO FABRICATION RELEASE
Eltec Instruments
Sheet:
File: copper_layers.kicad_pcb
Title: Individual copper layers - viewed from top

Size: A3 | Rev: REVIEW ONLY
KiCad E.D.A. 10.0.6 | Id: 1/4

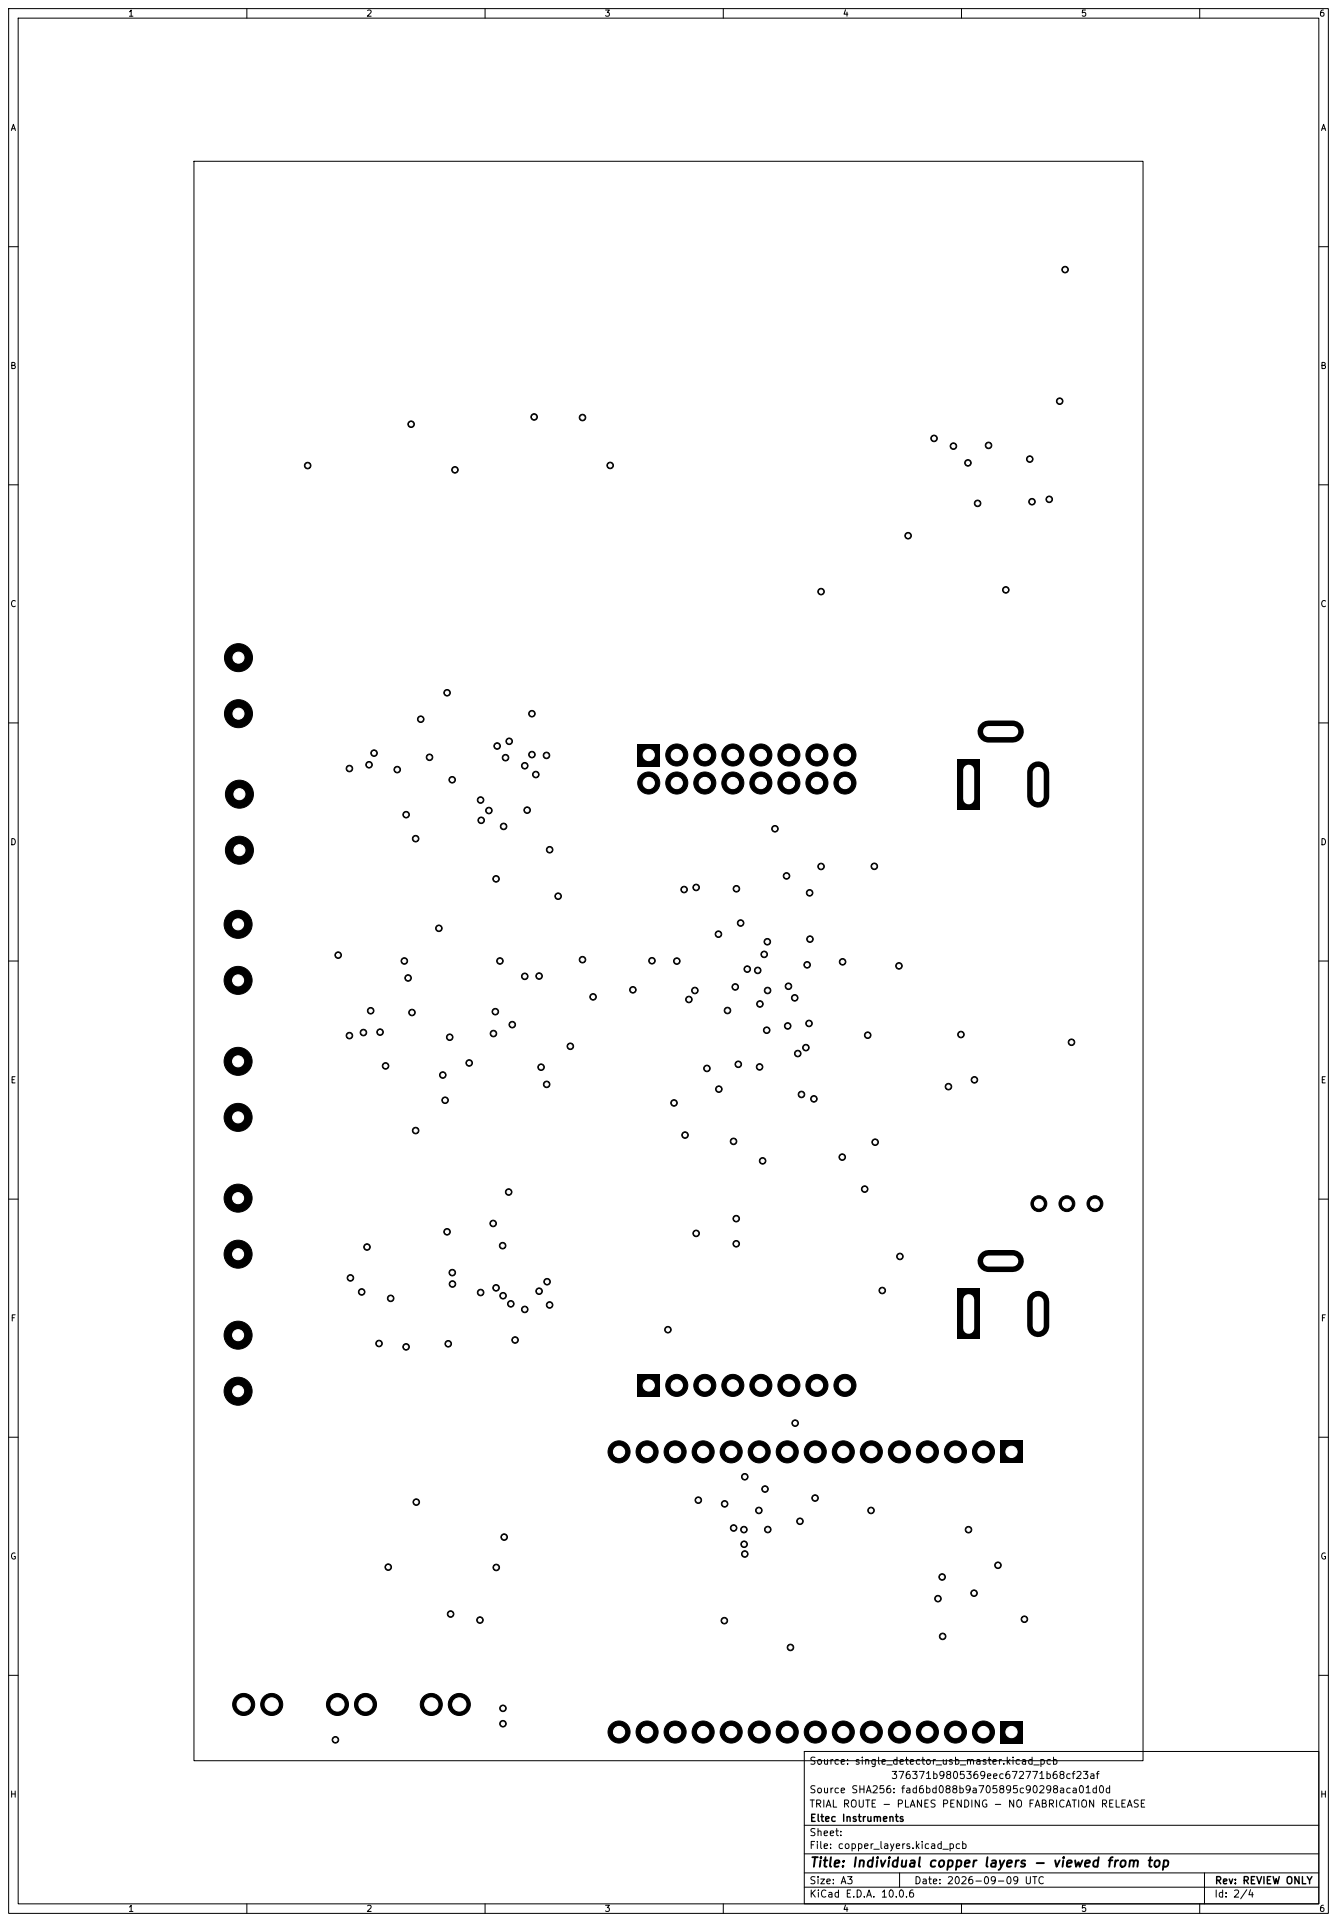
[picture p134: page 2]

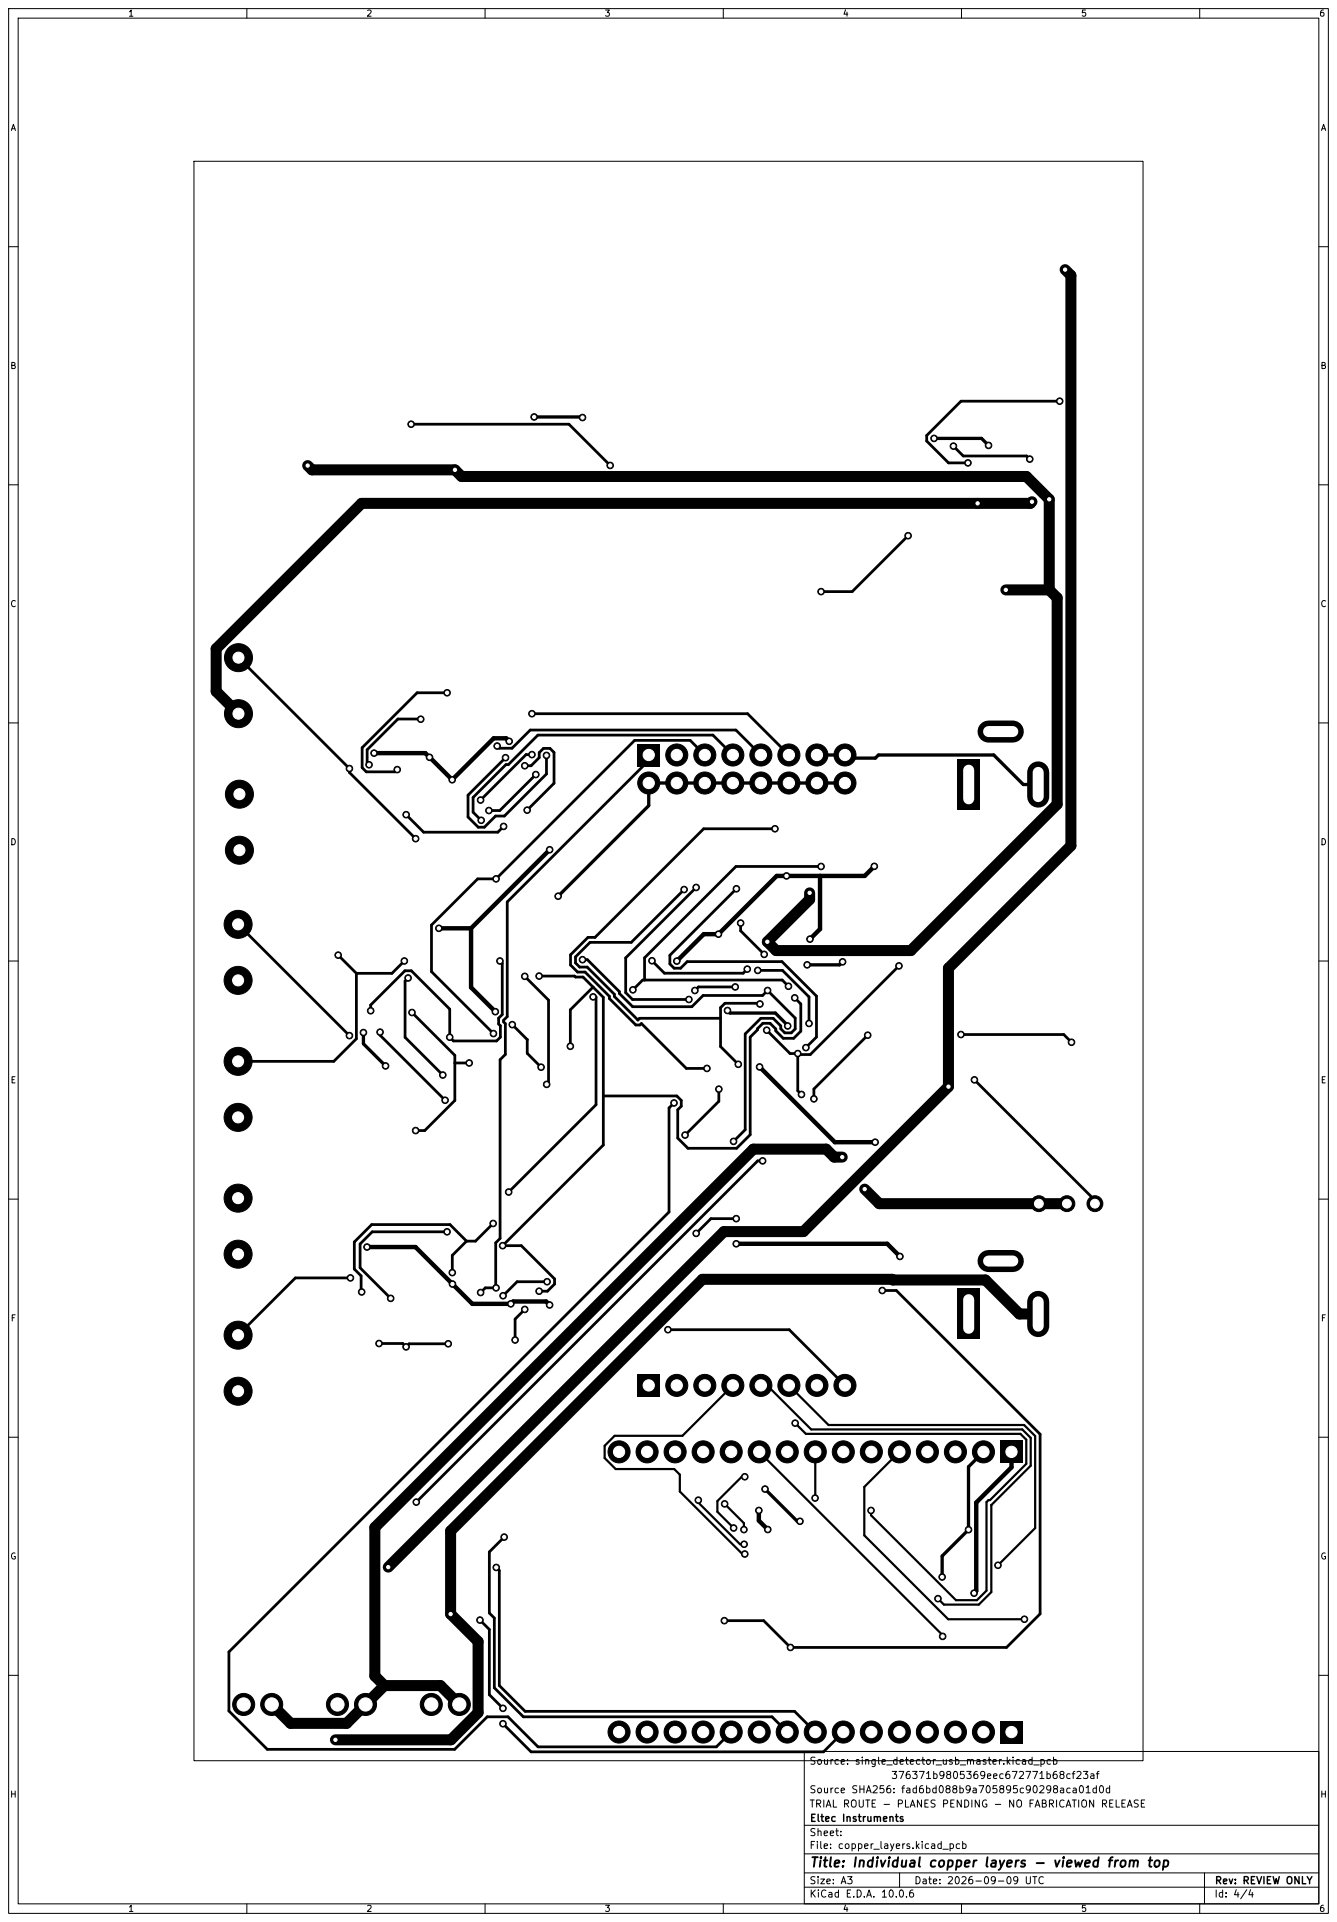
[picture p135: page 4]
