JCastel358/Eltec406mca/tmp/emitter_stage_check/project/emitter_regulator.kicad_sch

## KiCad design tmp/emitter_stage_check/project/emitter_regulator.kicad_sch (2026-09-09)

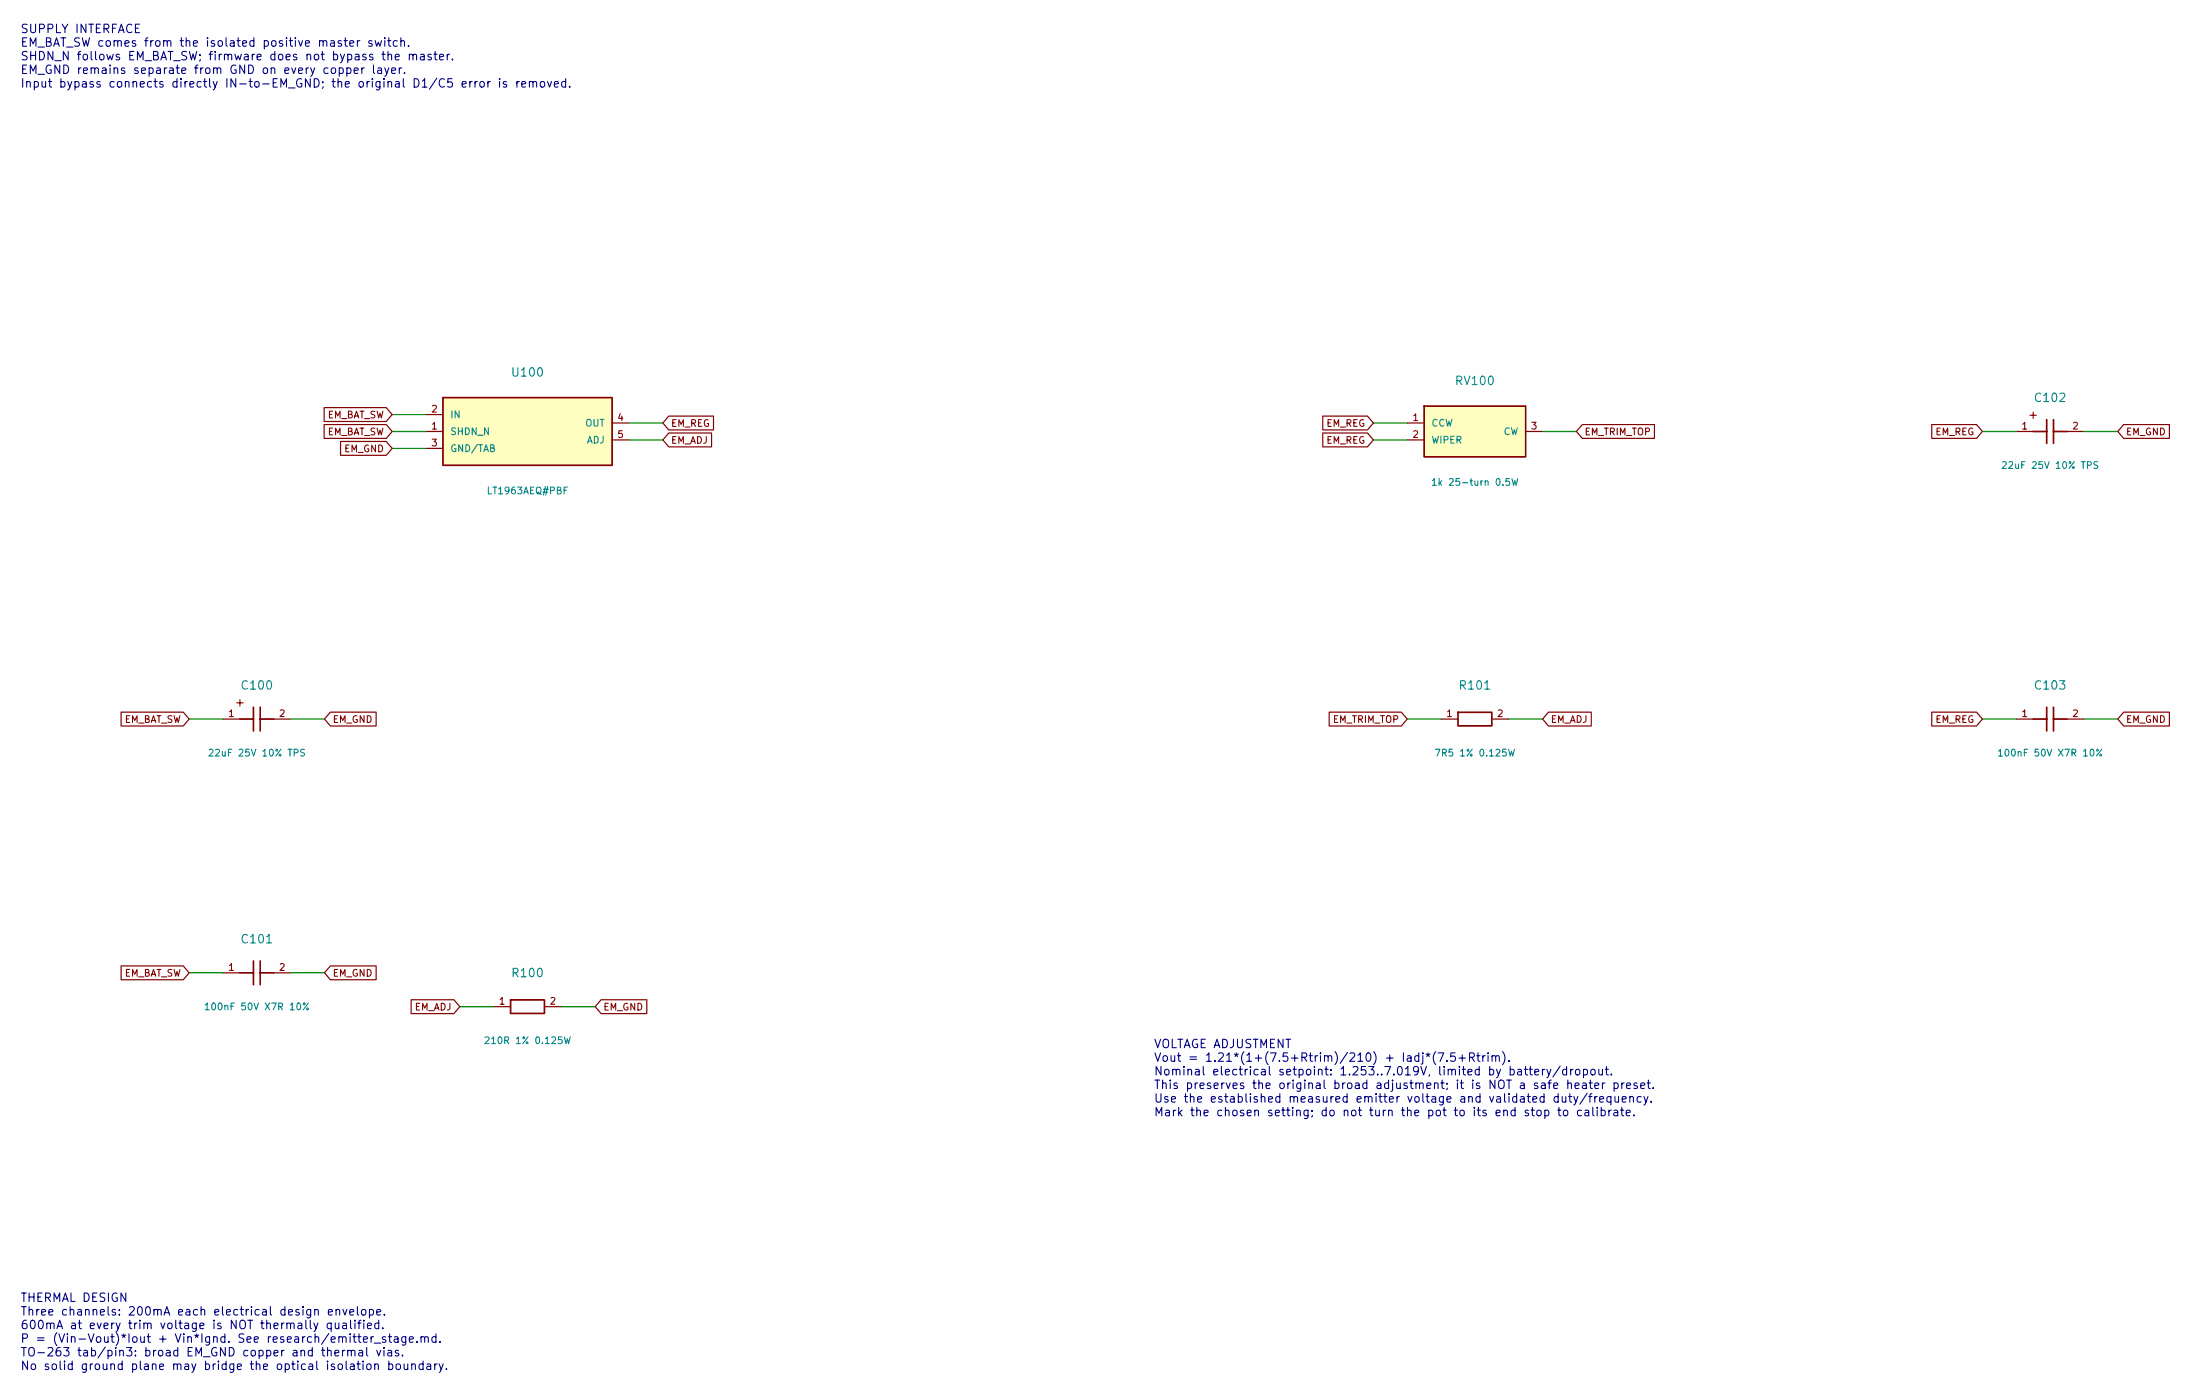
[picture p168: schematic emitter_regulator.kicad_sch]

Parts:
C100, C102: 22uF 25V 10% TPS; CP_EIA-7343-31_Kemet-D; MPN TPSD226K025R0200; LCSC C284839
C101, C103: 100nF 50V X7R 10%; C_0805_2012Metric; MPN CL21B104KBCNNNC
R100: 210R 1% 0.125W; R_0805_2012Metric; MPN RC0805FR-07210RL
R101: 7R5 1% 0.125W; R_0805_2012Metric; MPN RC0805FR-077R5L
RV100: 1k 25-turn 0.5W; Potentiometer_Bourns_3296W_Vertical; MPN 3296W-1-102LF; LCSC C57089
U100: LT1963AEQ#PBF; TO-263-5_TabPin3; MPN LT1963AEQ#PBF; LCSC C20415348

Connections:
EM_ADJ: R100.1, R101.2, U100.5 (ADJ)
EM_BAT_SW: C100.1, C101.1, U100.1 (SHDN_N), U100.2 (IN)
EM_GND: C100.2, C101.2, C102.2, C103.2, R100.2, U100.3 (GND/TAB)
EM_REG: C102.1, C103.1, RV100.1 (CCW), RV100.2 (WIPER), U100.4 (OUT)
EM_TRIM_TOP: R101.1, RV100.3 (CW)

Notes on the sheet:
SUPPLY INTERFACE EM_BAT_SW comes from the isolated positive master switch. SHDN_N follows EM_BAT_SW; firmware does not bypass the master. EM_GND remains separate from GND on every copper layer. Input bypass connects directly IN-to-EM_GND; the original D1/C5 error is removed.
VOLTAGE ADJUSTMENT Vout = 1.21*(1+(7.5+Rtrim)/210) + Iadj*(7.5+Rtrim). Nominal electrical setpoint: 1.253..7.019V, limited by battery/dropout. This preserves the original broad adjustment; it is NOT a safe heater preset. Use the established measured emitter voltage and validated duty/frequency. Mar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
THERMAL DESIGN Three channels: 200mA each electrical design envelope. 600mA at every trim voltage is NOT thermally qualified. P = (Vin-Vout)*Iout + Vin*Ignd. See research/emitter_stage.md. TO-263 tab/pin3: broad EM_GND copper and thermal vias. No solid ground plane may bridge the optical isolation 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
