JCastel358/Eltec406mca/hardware/single_detector_usb_master_r1/source_reference/ESP32_test_board/ESP32_test_board.kicad_sch

## KiCad design hardware/single_detector_usb_master_r1/source_reference/ESP32_test_board/ESP32_test_board.kicad_sch (2026-09-09)

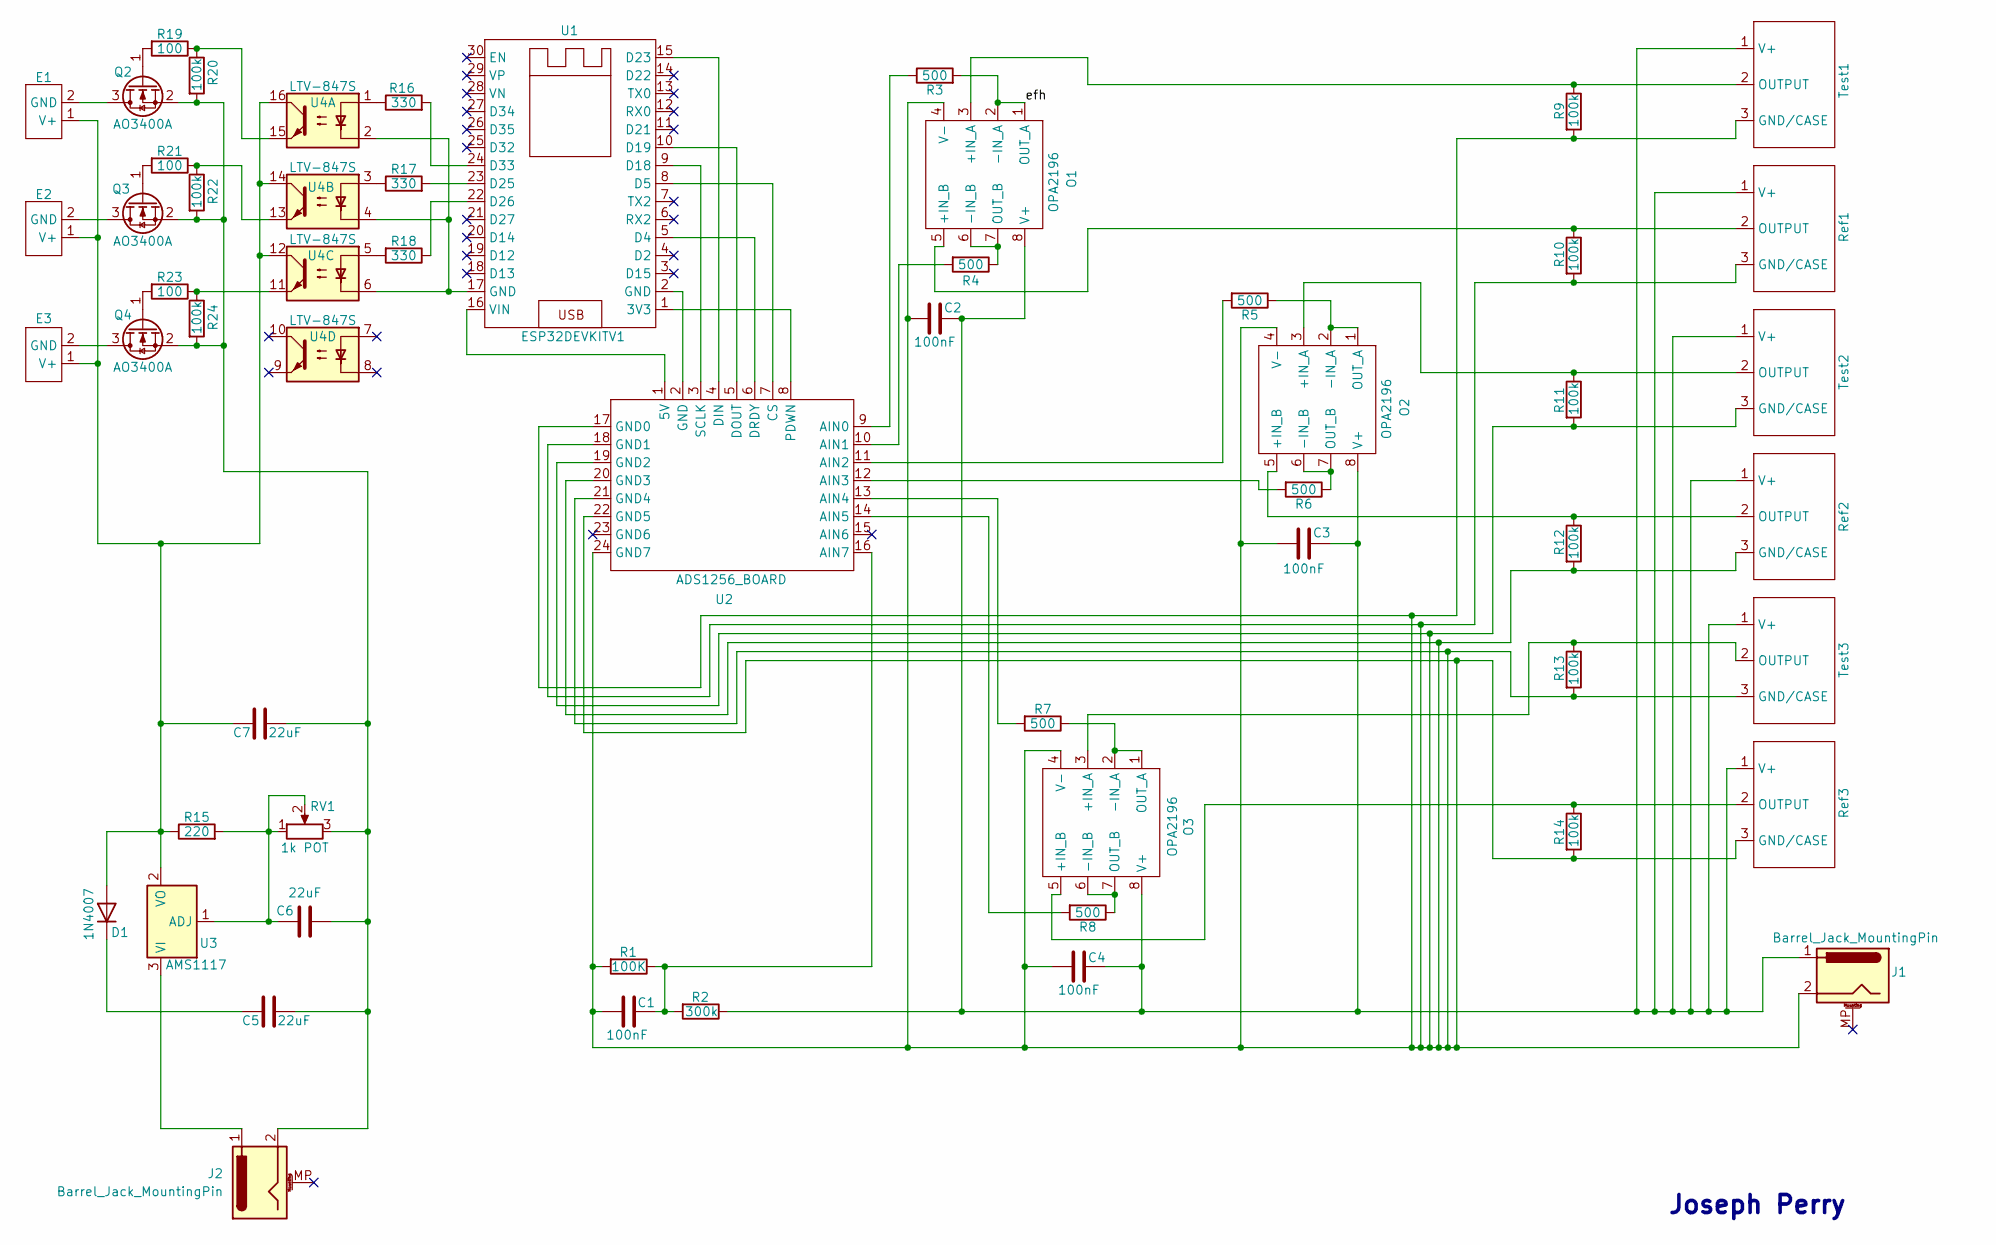
[picture p169: schematic ESP32_test_board.kicad_sch]

Parts:
C1, C2, C3, C4: 100nF; C_0805_2012Metric
C5, C6, C7: 22uF; C_1206_3216Metric
D1: 1N4007; D_SOD-123
E1, E2, E3: IR-56; Emitter
J1, J2: Barrel_Jack_MountingPin; BarrelJack_GCT_DCJ200-10-A_Horizontal
O1, O2, O3: OPA2196; SOIC-8_3.9x4.9mm_P1.27mm
Q2, Q3, Q4: AO3400A; SOT-23
R1: 100K; R_0805_2012Metric
R2: 300k; R_0805_2012Metric
R3, R4, R5, R6, R7, R8: 500; R_0805_2012Metric
R9, R10, R11, R12, R13, R14, R20, R22, R24: 100k; R_0805_2012Metric
R15: 220; R_0805_2012Metric
R16, R17, R18: 330; R_0805_2012Metric
R19, R21, R23: 100; R_0805_2012Metric
RV1: 1k POT; Potentiometer_Bourns_3296W_Vertical
Ref1, Ref2, Ref3: Sensor
Test1, Test2, Test3: Sensor
U1: ESP32DEVKITV1; ESP32_DEVKITV1
U2: ADS1256_BOARD
U3: AMS1117; SOT-223-3_TabPin2
U4: LTV-847S; SMDIP-16_W9.53mm

Connections:
unnamed: C1.1, R1.1, R2.2, U2.16 (AIN7)
unnamed: C1.2, C2.2, C3.2, C4.2, J1.2, O1.4 (V-), O2.4 (V-), O3.4 (V-), R1.2, R9.2, R10.2, R11.2, R12.2, R13.2, R14.2, Ref1.3 (GND/CASE), Ref2.3 (GND/CASE), Ref3.3 (GND/CASE), Test1.3 (GND/CASE), Test2.3 (GND/CASE), Test3.3 (GND/CASE), U2.17 (GND0), U2.18 (GND1), U2.19 (GND2), U2.20 (GND3), U2.21 (GND4), U2.22 (GND5), U2.24 (GND7)
unnamed: C2.1, C3.1, C4.1, J1.1, O1.8 (V+), O2.8 (V+), O3.8 (V+), R2.1, Ref1.1 (V+), Ref2.1 (V+), Ref3.1 (V+), Test1.1 (V+), Test2.1 (V+), Test3.1 (V+)
unnamed: C5.1, C6.1, C7.1, J2.2, Q2.2 (S), Q3.2 (S), Q4.2 (S), R20.2, R22.2, R24.2, RV1.3
unnamed: C5.2, D1.1 (K)
unnamed: C6.2, R15.2, RV1.1, RV1.2, U3.1 (ADJ)
unnamed: C7.2, D1.2 (A), E1.1 (V+), E2.1 (V+), E3.1 (V+), R15.1, U3.2 (VO), U4.12, U4.14, U4.16
unnamed: E1.2 (GND), Q2.3 (D)
unnamed: E2.2 (GND), Q3.3 (D)
unnamed: E3.2 (GND), Q4.3 (D)
unnamed: J2.1, U3.3 (VI)
unnamed: O1.3 (+IN_A), R9.1, Test1.2 (OUTPUT)
unnamed: O1.5 (+IN_B), R10.1, Ref1.2 (OUTPUT)
unnamed: O1.6 (-IN_B), O1.7 (OUT_B), R4.1
unnamed: O2.1 (OUT_A), O2.2 (-IN_A), R5.1
unnamed: O2.3 (+IN_A), R11.1, Test2.2 (OUTPUT)
unnamed: O2.5 (+IN_B), R12.1, Ref2.2 (OUTPUT)
unnamed: O2.6 (-IN_B), O2.7 (OUT_B), R6.1
unnamed: O3.1 (OUT_A), O3.2 (-IN_A), R7.1
unnamed: O3.3 (+IN_A), R13.1, Test3.2 (OUTPUT)
unnamed: O3.5 (+IN_B), R14.1, Ref3.2 (OUTPUT)
unnamed: O3.6 (-IN_B), O3.7 (OUT_B), R8.1
unnamed: Q2.1 (G), R19.2
unnamed: Q3.1 (G), R21.2
unnamed: Q4.1 (G), R23.2
unnamed: R3.1, U2.9 (AIN0)
unnamed: R4.2, U2.10 (AIN1)
unnamed: R5.2, U2.11 (AIN2)
unnamed: R6.2, U2.12 (AIN3)
unnamed: R7.2, U2.13 (AIN4)
unnamed: R8.2, U2.14 (AIN5)
unnamed: R16.1, U4.1
unnamed: R16.2, U1.24 (D33)
unnamed: R17.1, U4.3
unnamed: R17.2, U1.23 (D25)
unnamed: R18.1, U1.22 (D26)
unnamed: R18.2, U4.5
unnamed: R19.1, R20.1, U4.15
unnamed: R21.1, R22.1, U4.13
unnamed: R23.1, R24.1, U4.11
unnamed: U1.1 (3V3), U2.8 (PDWN)
unnamed: U1.2 (GND), U2.2 (GND)
unnamed: U1.5 (D4), U2.6 (DRDY)
unnamed: U1.8 (D5), U2.7 (CS)
unnamed: U1.9 (D18), U2.3 (SCLK)
unnamed: U1.10 (D19), U2.5 (DOUT)
unnamed: U1.15 (D23), U2.4 (DIN)
unnamed: U1.16 (VIN), U2.1 (5V)
unnamed: U1.17 (GND), U4.2, U4.4, U4.6
efh: O1.1 (OUT_A), O1.2 (-IN_A), R3.2

Notes on the sheet:
Joseph Perry
