JCastel358/Eltec406mca/tech_app/v4_emitter/eltec_406mca_emitter_tester.py

"""
Eltec 406MCA emitter tester v4 - guided workflow with a full visual overhaul.

The measurement engine, wiring, and guided flow are identical to v3; v4 is a
presentation-layer rebuild styled after eltecinstruments.com:

    - Deep Eltec-blue gradient app bar with an animated signal trace
    - Numbered step rail ("01 / 02 / 03") with animated progress transitions
    - Rounded, soft-shadow cards with the Eltec technical gradient accent
    - Custom hover-animated rounded buttons and an animated toggle switch
    - Count-up result tiles, PASS/FAIL banner sweep, scanning-beam scope view
    - Dark navy oscilloscope panel with grid + glow traces (site "dark section"
      look), JetBrains Mono / Consolas for all technical readouts

This app drives the test rig itself: the LabJack T7-Pro generates a PWM signal
that switches a MOSFET to drive the black-body emitter. The 406MCA sensor is
read WITHOUT the AM502 amplifier - a unity-gain (voltage-follower) op-amp buffer
feeds the LabJack a low-impedance signal while preserving the ~0.667 V DC offset
and the small AC waveform.

Wiring:
    AIN0 = buffered sensor signal (carries BOTH the DC offset and the AC signal)
    AIN1 = 9V battery through a 100k/100k divider (divide-by-2), so the LabJack
           watches the supply that powers the op-amp buffer + sensor and blocks
           testing once it sags too low. Reads on the +/-10 V range (Vbat/2).
    AIN2 = PWM / MOSFET-gate drive, looped back as the polarity/sync reference
    DIO0 = PWM output to the MOSFET gate (common ground with the emitter supply)

The emitter is always driven with a fixed 50% duty-cycle square wave, so the
technician never has to think about PWM settings - they only pick the filter.

Guided flow:
    1. Enter batch number, tester name, and filter/setup, then press Enter.
    2. Place the sensor in the rig and press Enter.
    3. The app reads the DC offset (PWM off), then turns on the PWM emitter and
       measures sensitivity and polarity, shows the numbers and a GOOD/BAD
       polarity verdict, and turns the screen green (PASS) or red (FAIL).
       Leave a comment, capture the waveform for troubleshooting, or watch the
       live waveform while it reads.

Run:
    python eltec_406mca_emitter_tester.py
"""

from __future__ import annotations

import csv
import json
import math
import struct
import threading
import time
import tkinter as tk
import zlib
from dataclasses import dataclass, field as dataclass_field
from datetime import datetime
from pathlib import Path
from tkinter import font as tkfont
from tkinter import messagebox, ttk

import numpy as np

# Reuse the proven analysis + PWM engine from the v1 single-sensor tester so
# there is a single source of truth for the signal math and the LabJack device
# wrapper. That module lives in a sibling version folder (tech_app/v1_single_sensor),
# so add it to the import path.
import sys

_V1_TESTER_DIR = Path(__file__).resolve().parents[1] / "v1_single_sensor"
if str(_V1_TESTER_DIR) not in sys.path:
    sys.path.insert(0, str(_V1_TESTER_DIR))
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
