JCastel358/Eltec406mca/hardware/single_detector_usb_master_r1/source_reference/SingleDetectorCase.jpg

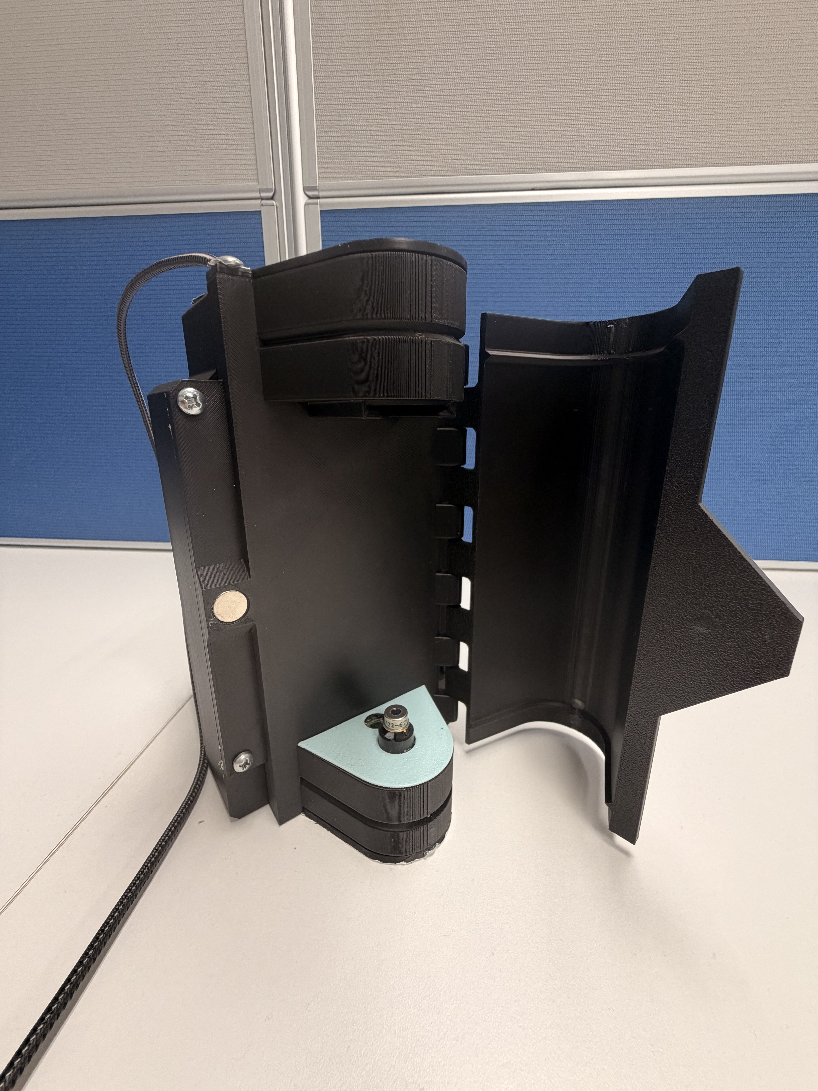
hardware/single_detector_usb_master_r1/source_reference/SingleDetectorCase.jpg
